jufo-ufo/Breadboard-Computer/paper/JuFo_Langfassung/Langfassung.pdf_correction.pdf

# Platinencomputer - Langfassung

### Alexander Wersching und Simon Walter

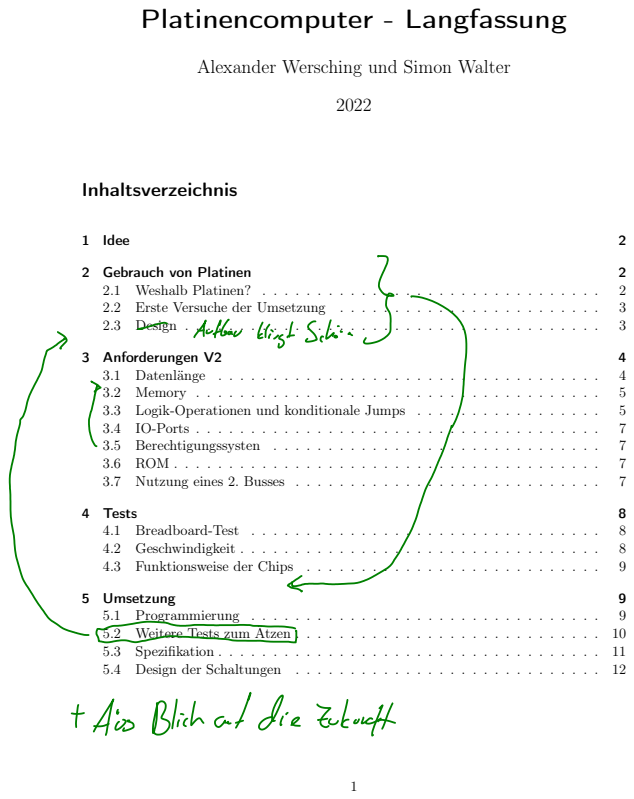
[picture p17: page 1]
Inhaltsverzeichnis; 1 Idee; 2 Gebrauch von Platinen; 3 Anforderungen V2; 4 Tests; 5 Umsetzung

### 1 Idee

Vor ca. 2 Jahren hatte Alex die Idee, er wolle einen 8-bit Computer bauen, die vor 2 Jahren beim Regionalwettbewerb München-West eingereichte Version einer anderen Gruppe
hat | dann | auch | das | Interresse | von | mir | (Simon) | geweckt.
Ein paar Monate später haben wir uns
dann dazu entschieden, tatsächlich einen
eigenen 8-bit-Computer zu bauen und haben auch bald angefangen erste Versuche auf dem Breadboard zu entwickeln. Es gab noch weder eine Möglichkeit diese erste Version automatisch zu betreiben, noch Daten zu schreiben/speichern, oder irgendwie mit der Umgebung zu interagieren, nur 3 Register, 2 Operationen und viele Knöpfe zum Bedienen.

### 2 Gebrauch von Platinen

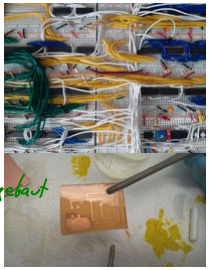
[picture p18: figure]

2.1 Weshalb Platinen?


Bald war aber klar, dass ein einfaches Verwenden von flachen Kabeln als Verbindung zwischen den Breadboards, das Kabelgewirr, das wir bei dem Projekt von vor 2 Jahren gesehen haben und nach Möglichkeit vermeiden wollten, um ein übersichtlicheres Design zu erreichen, nicht lösen kann.

Auf der Suche nach einer Alternative sind wir fast zwangsläufig auf Platinen gekommen, aber weil unser Computer ja nicht mehr wirklich selbst gemacht wäre, wenn wir diese nur professionell Ätzen lassen würden, wollten wir versuchen - zumindest einen Teil - selbst zu ätzen, auch wenn wir dadurch natürlich auf viele neue Probleme gestoßen sind...

2

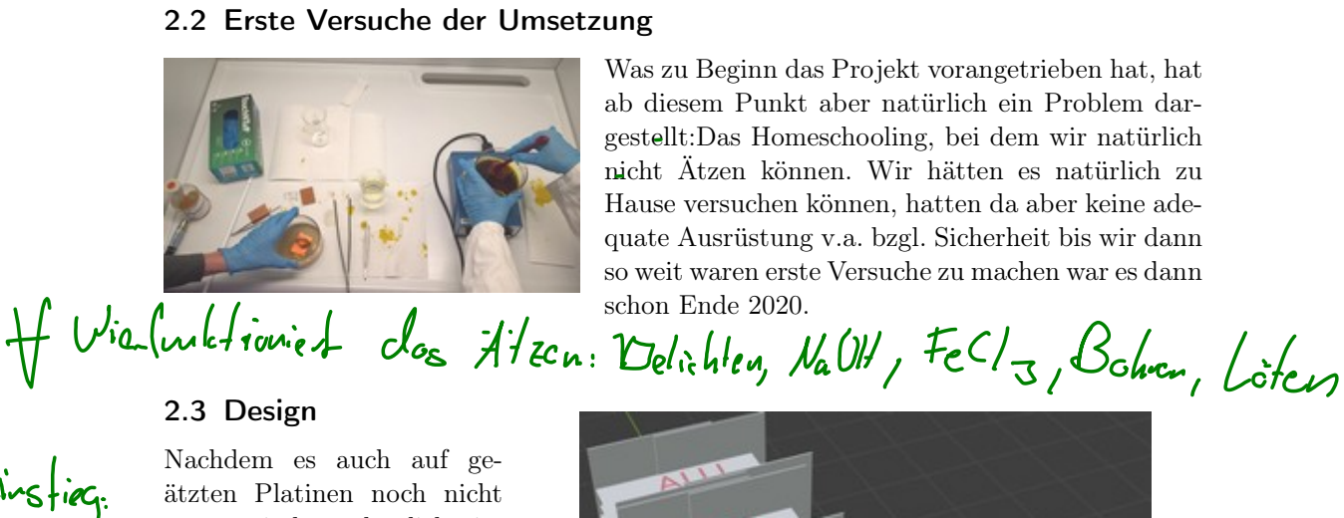
[picture p19: figure]
2.2 Erste Versuche der Umsetzung; schon Ende 2020.; 2.3 Design Nachdem es auch auf ge- ätzten Platinen noch nicht

Was zu Beginn das Projekt vorangetrieben hat, hat ab diesem Punkt aber natürlich ein Problem dargestellt:Das Homeschooling, bei dem wir natürlich nicht Ätzen können. Wir hätten es natürlich zu Hause versuchen können, hatten da aber keine adequate Ausrüstung v.a. bzgl. Sicherheit bis wir dann so weit waren erste Versuche zu machen war es dann


automatisch ordentlich ist und eine derart große Platine für uns nicht machbar gewesen wäre, haben
wir uns dann noch ein 3-
Dimensionales Design ausgedacht.

Offensichtlich ist das mit unseren aktuell geplanten Modulen: am Boden sitzt eine große Bus-Platine, auf der wir alle Module senkrecht
aufstecken.

3

### 3 Anforderungen V2

Im nächsten Lockdown hatten wir dann wieder viel Zeit zu planen, und der geplante Computer wurde immer komplexer.

3.1 Datenlänge
Aus den ursprünglich geplanten 8-bit wurden 16-bit Datenlänge:
Die Address- und Datenlänge besagt, wie viele binäre Ziffern (bits) für eine Adresse und Daten verwendet werden.
Je mehr Ziffern man verwendet desto größere Zahlen können in einer Operation verarbeitet werden wobei die maximal repräsentierbare Zahle 2n − 1 ist wenn n die Anzahl der Binären Ziffern (= Bits) ist.

n teilbar durch 8 zu machen, ist dabei relativ angenehm, weil 8 bit = 1 byte,
und Bytes sind nun mal die Grundlage für das meiste in der Informatik,
zudem kommen einige elementar ICs, z.B. Buffer oder Register, immer mit 8 bits.

Jedoch gilt, je mehr Bits man verwendet, desto mehr Schaltung braucht man und desto größer der Stromverbrauch, wodurch es für uns relativ schnell unrealistisch aufwendig wird

Wir haben uns daher für 16 bit entschieden, womit wir Zahlen bis zwischen 0 und 65535 darstellen können.
Diese Menge ist gerade große genug, um eine Zahl abzubilden, die für die meisten Programme groß genug ist, aber trotzdem auf Platinen noch einigermaßen handhabbar.

4

3.2 Memory
Um auch Daten oder Programme verwenden zu können haben wir dann als erstes noch einen größeren Speicher hinzu gefügt: Memory
Memory ist in 65536 (weil wir genau so viele Adressen in unseren 16bit speichen können) einzelne und unabhängige Speicherzellen (jede 16 Bit groß) aufgeteilt.
Der Computer kann damit auf 65536 words oder 131072 bytes (= 128 kib) direkt zugreifen.
(Die Größe messen wir in words (w) oder in kilowords (kiw), wobei 1 word = 2 bytes = 16 Bit sind.)

Memory wird dabei über LD- und STR-Instruktionen gesteuert.
Die LD-Instruktion kopiert einen Wert aus Memory und schreibt ihn in ein Ziel-Register, während STR an der angegebenen Adresse den Wert mit dem Wert des Quellen-Register überschreibt.

Um aber noch mehr Speicher zu bekommen und das später erwähnte Berechtigungssystem möglichst einfach umsetzen zu können haben wir noch Banken hinzugefügt:
Banken sind externe Memory Module, die eingesteckt werden können. Alle Banken sind gleich groß (16 kiw = 32 kib) und der Computer unterstützt maximal 65536 unterschiedliche Banken. Jede Bank hat dabei eine ID (BID), die von 0 bis 65535 reicht.
Der Computer hat zwei Bank-Slots (Slot 1 0x8000 - 0xbfff und Slot 2 0xc000 -0xffff).

Es kann auf jede dieser Slots eine der theoretisch 65536 Banken gelegt werden.
Bank 1 ist dafür gedacht, dass jeder Prozess dort in seiner eigenen Bank lebt, sodass in dem Prozess absolute Memory Adressen verwendet werden können, weil das Programm immer an der gleichen Stelle liegt. Außerdem wird in der Bank auch der Stack des jeweiligen Prozesses gespeichert, sodass dieser von anderen Prozessen nicht überschrieben werden kann.
Bank 2 dient als potentieller zusätzlichen Speicher des Prozesses, oder als allgemeineren Speicherort, um zwischen den Prozessen Daten zu übermitteln.

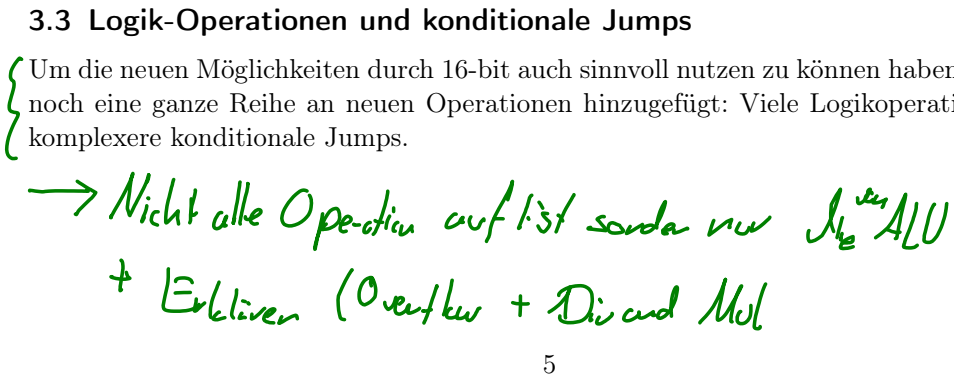
[picture p20: figure]
3.3 Logik-Operationen und konditionale Jumps; komplexere konditionale Jumps.

Um die neuen Möglichkeiten durch 16-bit auch sinnvoll nutzen zu können haben wir dann noch eine ganze Reihe an neuen Operationen hinzugefügt: Viele Logikoperationen und

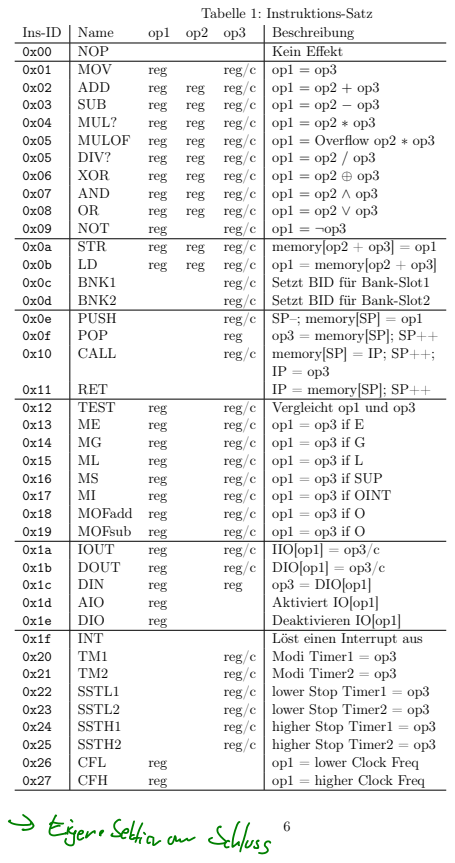
[picture p21: page 6]
Ins-ID; Name; Beschreibung; NOP; Kein Effekt; MOV; reg; reg/c; ADD; reg reg reg/c; SUB; MUL?; MULOF reg reg reg/c; op1 = Overflow op2 ∗ op3; DIV?; XOR; AND; NOT; STR; memory[op2 + op3] = op1; op1 = memory[op2 + op3]; BNK1; Setzt BID für Bank-Slot1; BNK2; Setzt BID für Bank-Slot2; PUSH; SP–; memory[SP] = op1; POP; op3 = memory[SP]; SP++; CALL; memory[SP] = IP; SP++;; RET; IP = memory[SP]; SP++; TEST; Vergleicht op1 und op3; op1 = op3 if SUP; op1 = op3 if OINT; MOFadd reg; MOFsub reg; IOUT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

Tabelle 1: Instruktions-Satz

3.4 IO-Ports
Dazu hat sich die Idee von komplexer IO-Interaktion mit dem Computer ergeben: universelle Ports zum Anschließen von Festplatten, Sensoren, einfachen Tastaturen, LCD-Displays und einer Grafikkarte.
Die theoretisch 65536 Anschlüsse, wobei jedem eine Anschluss-ID zugewiesen ist, kommunizieren mit IO-Geräten über 4 Kommandos, die als 4 separate Pins zwischen dem Controller und dem Gerät umgesetzt sind:
1. Einen Befehl an das IO-Gerät schicken (auf Programm-Ebene);
2. Daten zu einem vorherigen Befahl an das Gerät schreiben;
3. Die Anfrage der IO-Gerätes Daten an den Computer zurück zu schreiben, was bei diesem normalerweise einen Interrupt auslöst;
4. Bestätigen des Computers, das das Externe Gerät schreiben darf.

3.5 Berechtigungssysten
Die vermutlich die größte Änderung war danach, dass wir ein Berechtigungssystem einführen wollten. Dafür haben wir dann Flaggen, Interrupts und noch mehr Instruktionen hinzugefügt.

3.6 ROM
Um den Computer komplett unabhängig funktionsfähig machen zu können, haben wir uns dann überlegt einen Teil des RAMs durch ROM zu ersetzen, um automatisch Programme von einem externen Speichermedium laden zu können.

3.7 Nutzung eines 2. Busses
Um Memory innerhalb einer Instruktion zu beschreiben, muss dieses sowohl eine 16-bit Adresse über die Position in Memory erhalten, als auch den 16-bit Wert, der dort gespeichert werden soll, damit diese beiden Daten parallel übermittelt werden können brauchen wir also 2*16bit. Wir hätten dafür natürlich auch irgendwelche Kabel verlegen können, aber wir wollen in unserem System die Daten immer auf dem Bus haben, damit diese auch von anderen Modulen gelesen werden könnten, und die Adresse muss im Anwendungsfall als Stack vor Benutzung um eins erhöht oder verringert werden, was in unserem System durch die ALU erfolgen sollte, wobei diese nur auf den Bus ihre Daten auseben kann.

7

### 4 Tests

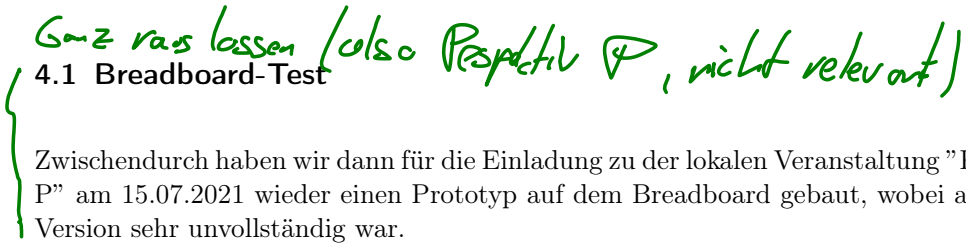
[picture p22: figure]
4.1 Breadboard-Test; Version sehr unvollständig war.

Zwischendurch haben wir dann für die Einladung zu der lokalen Veranstaltung ”Persvektive P” am 15.07.2021 wieder einen Prototyp auf dem Breadboard gebaut, wobei auch diese

4.2 Geschwindigkeit
Um einen Eindruck zu bekommen, wie komplex unsere Programme werden können, ohne übermäßig lange zu brauchen, haben wir dann versucht zu errechnen, wie schnell wir den Computer maximal laufen lassen können, ohne fehlerhafte Ergebnisse zu erhalten. Also haben den "Propagation-delay", die Zeit, bis der Chip den Output liefert, den der laut der Eingabe haben müsste, aller Komponenten gemessen, die wir verwenden wollen. Die meisten
Chips, die wir jetzt vorhaben zu verwenden, haben
eine Verzögerung von ungefähr 8 Nanosekunden, al-

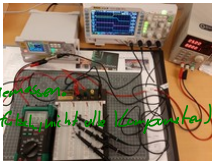
[picture p23: figure]

lerdings haben wir bei den verschiedenen Versionen, die wir getestet haben, teilweise weitaus höhere Werte bis zu 150ns erreicht, was an sich noch nicht so schlecht ist, aber wenn wir damit rechnen, dass wir Reihen von bis zu 40 Chips in einem Clock-Zyklus haben, limitiert das die Geschwindigkeit schon sehr.

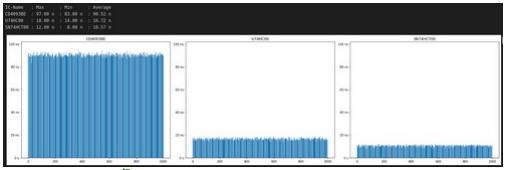
[picture p24: figure]

4.3 Funktionsweise der Chips
Wir wollen als Basis für unseren Computer ja Chips kaufen, aber wie funktionieren die eigentlich? Wir haben also versucht den Aufbau herauszufinden, indem wir einfach einen geöffnet haben, wobei ”Einfach” nicht so ganz stimmt, weil die Hülle aus Epoxidharz

8

besteht, was sich fast nicht auflösen lässt. Also mussten wir mechanisch abtragen, also Schleifen. Leider haben wir es damit nie geschafft das gesamte Silizium/die Verbindungsbahnen frei zu legen, sodass wir keinen Schaltplan erstellen könnten, es gab uns aber

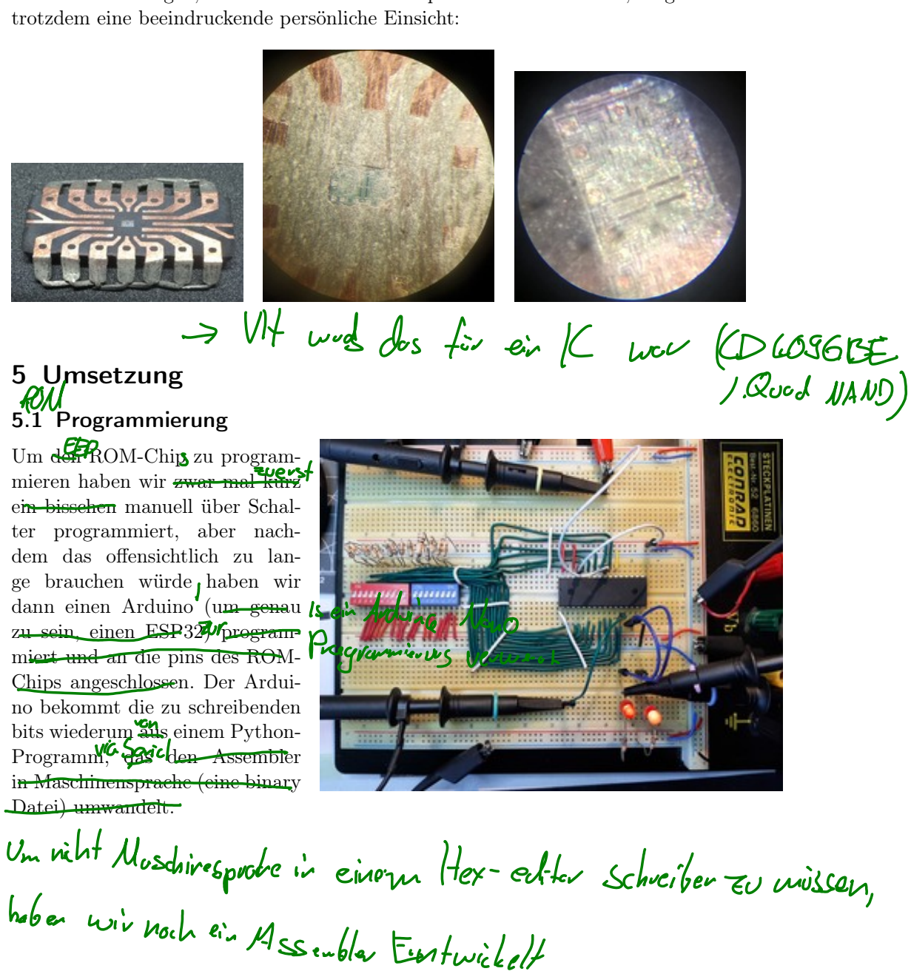
[picture p25: figure]
trotzdem eine beeindruckende persönliche Einsicht:; 5 Umsetzung; 5.1 Programmierung Um den ROM-Chip zu program- mieren haben wir zwar mal kurz ein bisschen manuell über Schal- ter programmiert, aber nach- dem das offensichtlich zu lan- ge brauchen würde haben wir dann einen Arduino (um genau zu sein, einen ESP32) program- miert und an die pins des ROM- Chips angeschlossen. Der Ardui- no bekommt die zu schreibenden bits wiederum aus einem Python- Programm, das den Assembler in Maschinensprache (eine binary Datei) umwandelt.

9

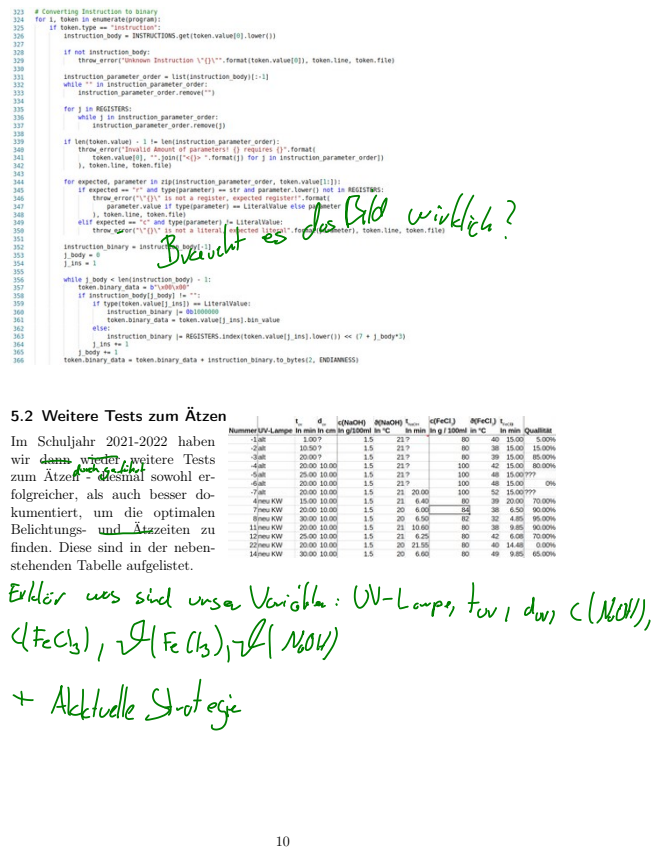
[picture p26: page 10]

5.2 Weitere Tests zum Ätzen
Im Schuljahr 2021-2022 haben
wir dann wieder weitere Tests
zum Ätzen - diesmal sowohl er-
folgreicher, als auch besser do-
kumentiert, um die optimalen
Belichtungs- und Ätzzeiten zu
finden. Diese sind in der neben-
stehenden Tabelle aufgelistet.

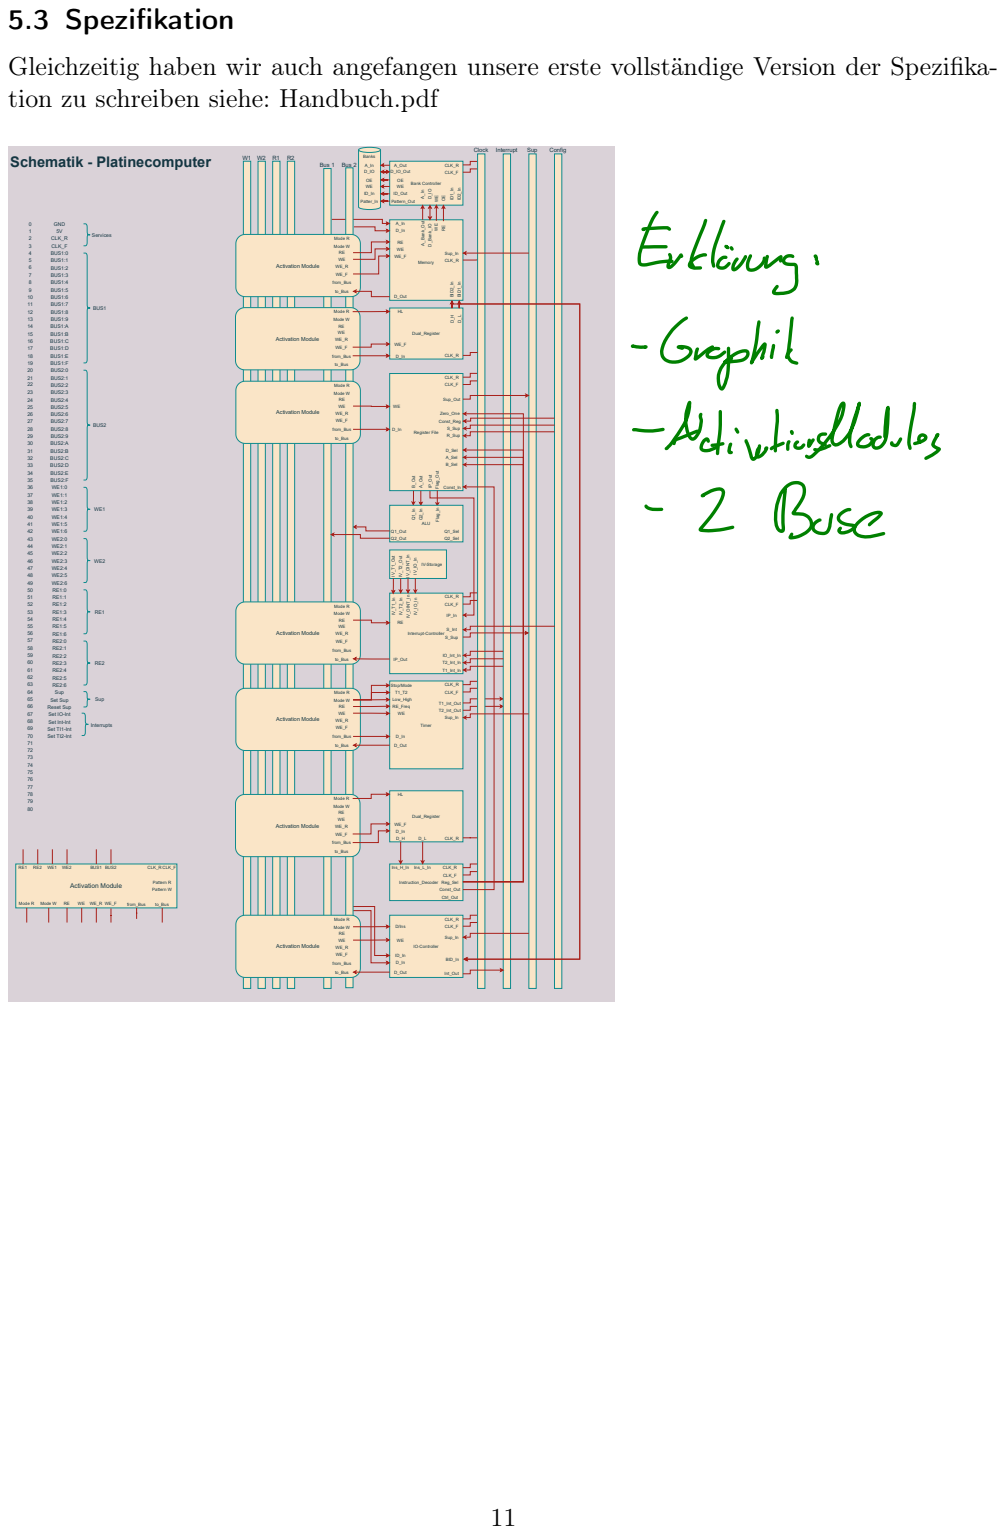
[picture p27: page 11]
Memory; D_Out; CLK_R WE A_Bank_Out; Bank Controller D_Bank_IO A_In D_IO WE; CLK_R; IO-Controller; D/Ins; CLK_F; Sup_In; Sup_In BID¹_In; Interrupt-Controller; IV-Storage; IV_T1_In IV_T1_Out RE; IP_Out; S_Sup; IO_Int_In; Int_Out; T1_Int_In; T2_Int_In; S_Int; CLK_FBID²_In; Instruction_Decoder; Ins_H_In; Ctrl_Out; Register File A_Out; Flag_Out; D_Sel; A_Sel; B_Sel; Sup_Out; R_Sup; Zero_One; B_Out; ALU; Q1_Out; Q2_Out; Q2_Sel Flag_In; Q1_Sel; Q2_In Timer; T1_Int_Out; T2_Int_Out; Low_High; Stop/Mode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

5.3 Spezifikation
Gleichzeitig haben wir auch angefangen unsere erste vollständige Version der Spezifika-
tion zu schreiben siehe: Handbuch.pdf

Set IO-Int
Set Int-Int
Set TI1-Int
Set TI2-Int

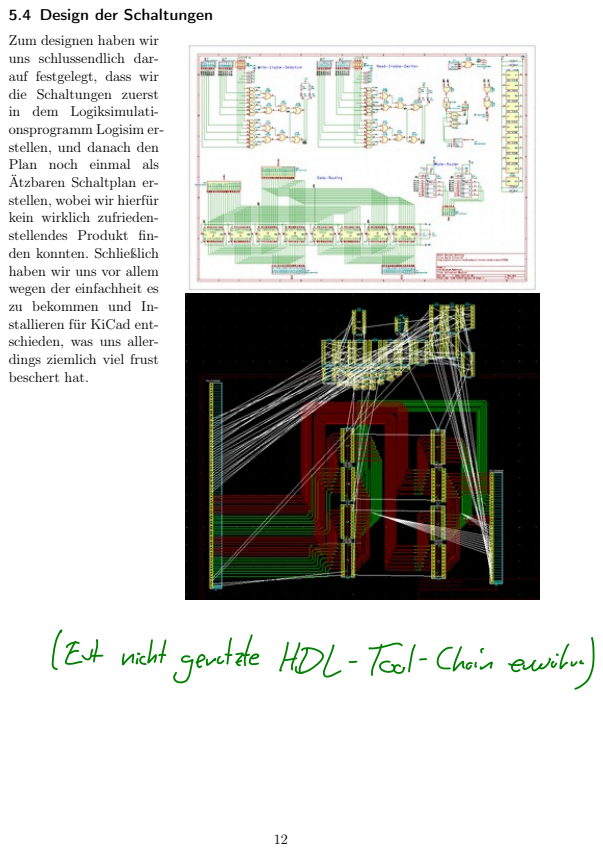
[picture p28: page 12]

5.4 Design der Schaltungen
Zum designen haben wir
uns schlussendlich dar-
auf festgelegt, dass wir
die Schaltungen zuerst
in dem Logiksimulati-
onsprogramm Logisim er-
stellen, und danach den
Plan noch einmal als
Ätzbaren Schaltplan er-
stellen, wobei wir hierfür
kein wirklich zufrieden-
stellendes Produkt fin-
den konnten. Schließlich
haben wir uns vor allem
wegen der einfachheit es
zu bekommen und In-
stallieren für KiCad ent-
schieden, was uns aller-
dings ziemlich viel frust
beschert hat.
