jufo-ufo/Breadboard-Computer/images/1Bilder_Dokumentation.odt

8Bit-Prozessor

23.7.2020:

- 1.er aufbau der Clock mit hilfe des NE555: noch mit starker Übersteuerung (Grund noch unbekannt)
- 1.er test einer Clock durch Spulen: Berechnungen haben gestimmt, noch keine “Dauerwelle”
- Erforschen der funktionen weiterer komponenten
- Vertrautmachen mit dem Oszi und der Stromquelle
