jufo-ufo/Breadboard-Computer/circets/Dual_Register/manufactor_sheet_top.pdf

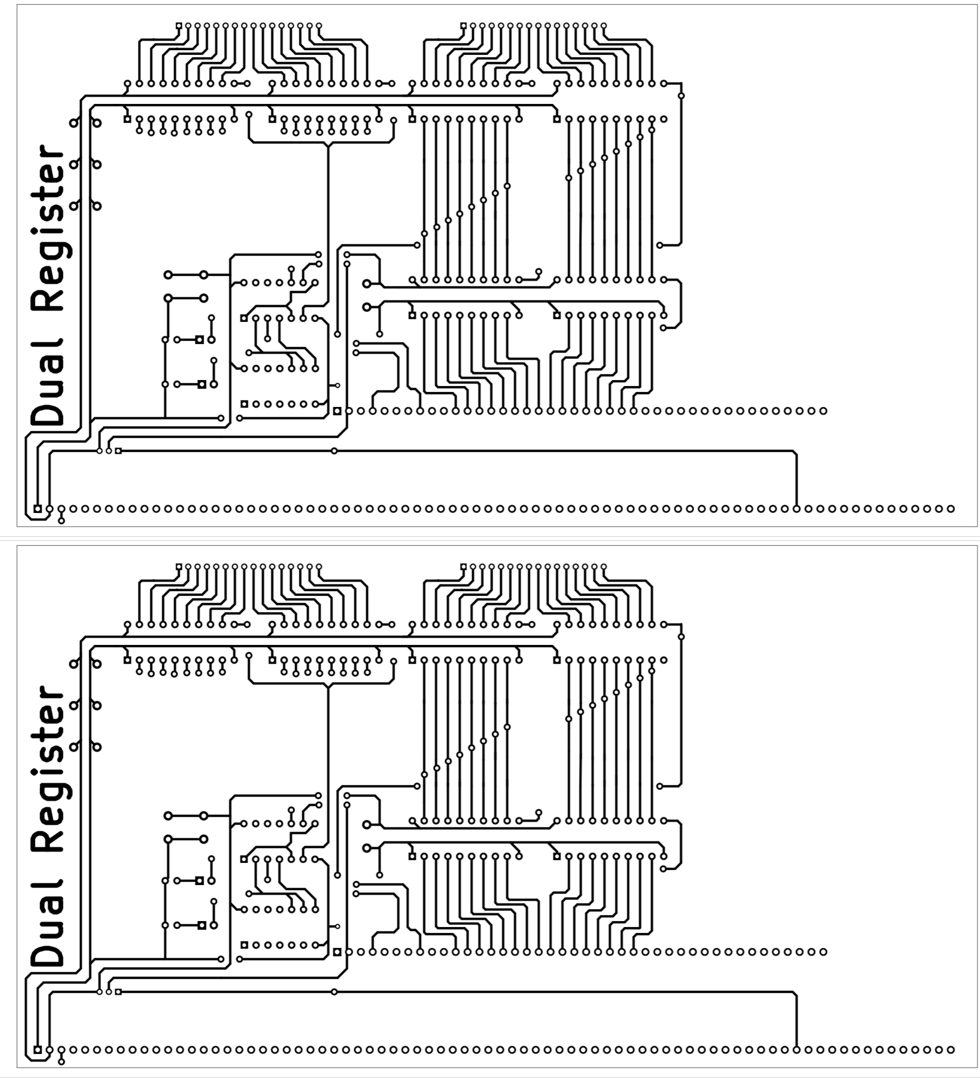
[picture p29: page 1]
