jufo-ufo/Breadboard-Computer/circets/Activation_Module/logic_schematic.png

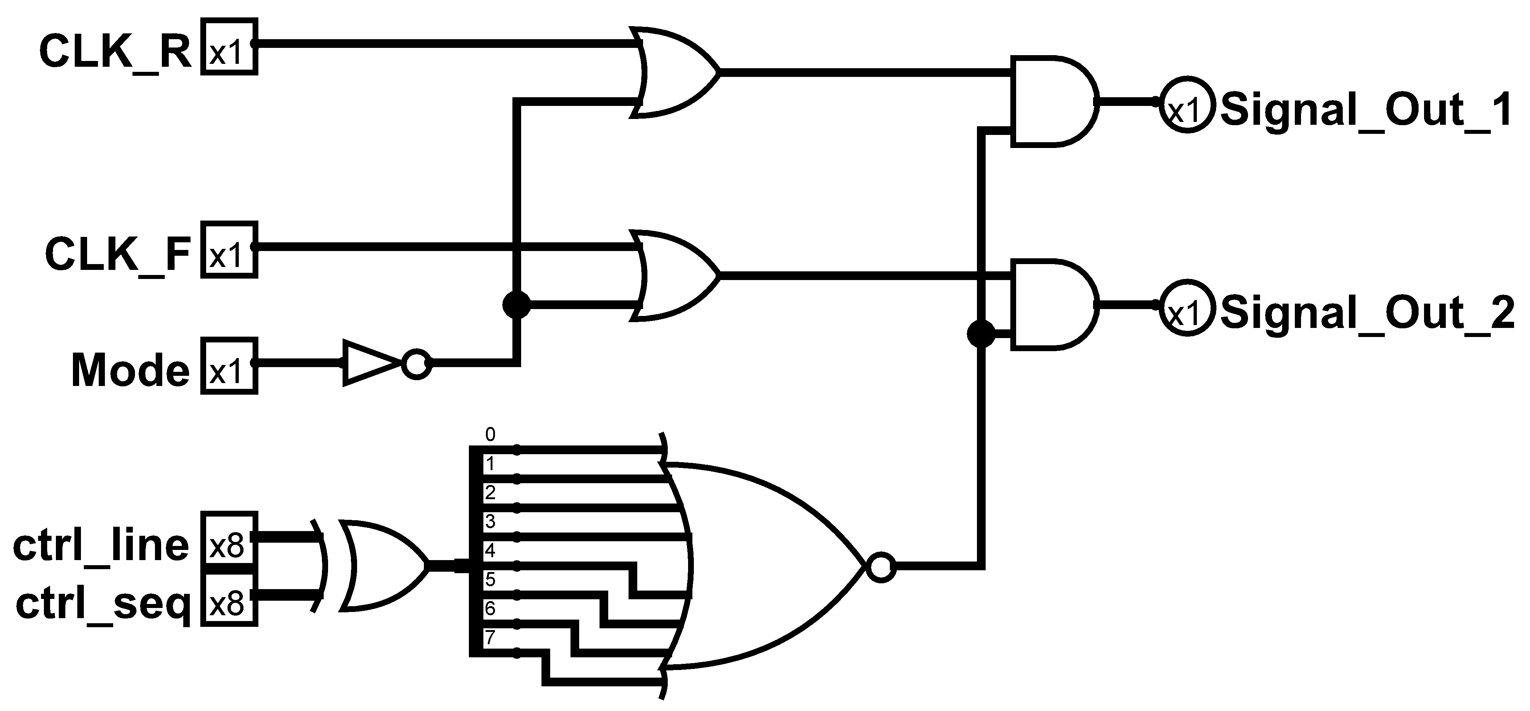
circets/Activation_Module/logic_schematic.png
