jufo-ufo/Breadboard-Computer/images/3D_Desighn_V2.png

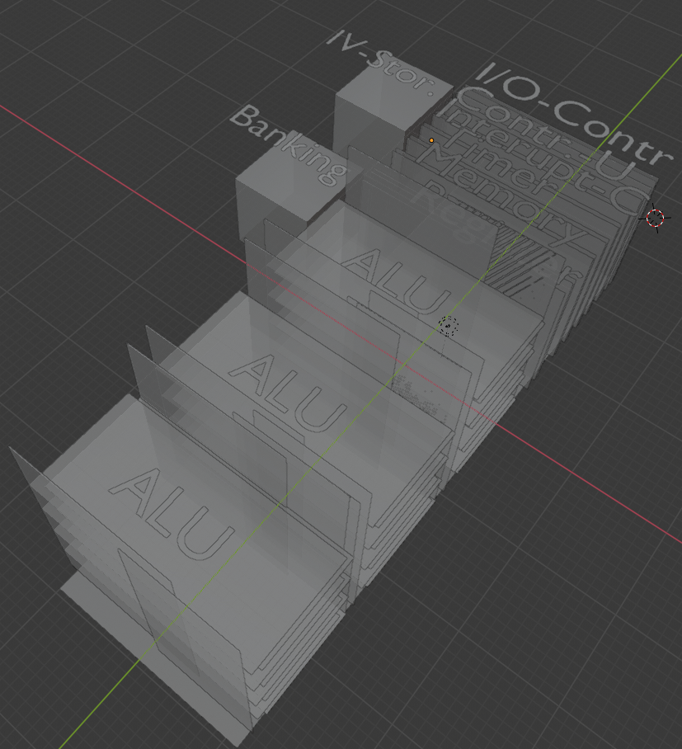
images/3D_Desighn_V2.png
