jufo-ufo/Breadboard-Computer/images/20211208_200820.jpg

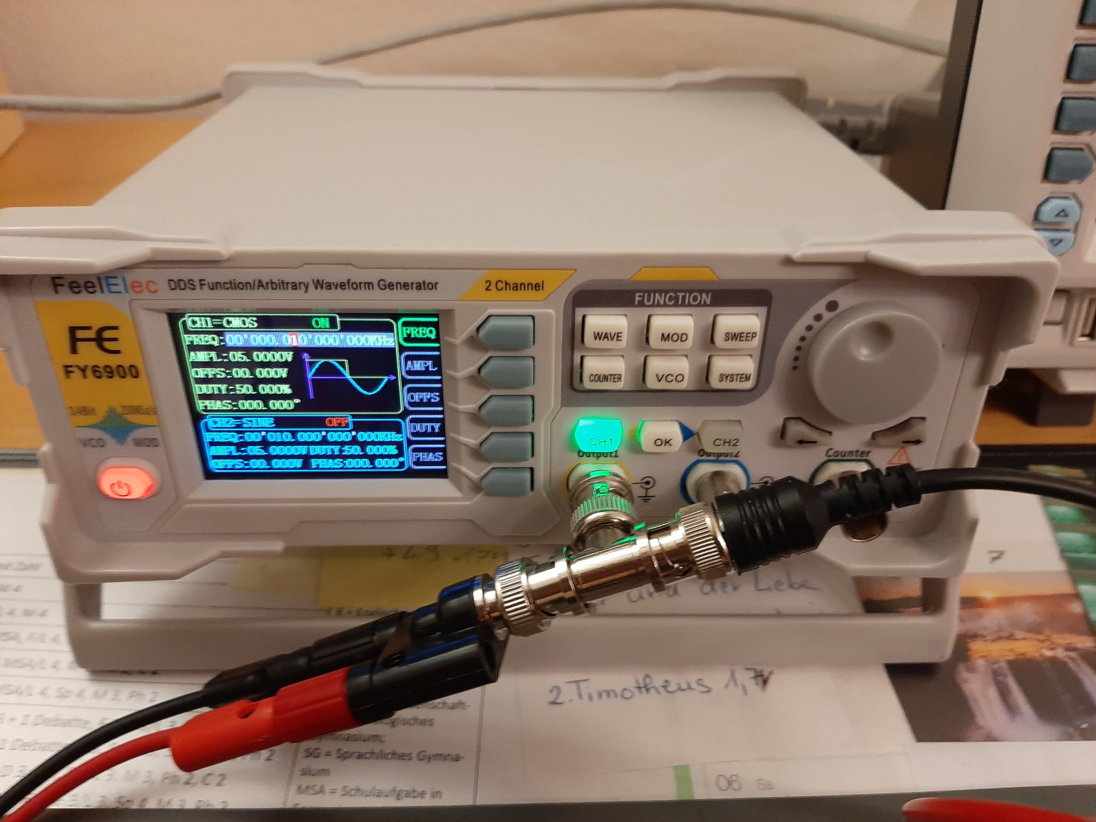
images/20211208_200820.jpg
