jufo-ufo/Breadboard-Computer/images/20211208_200826.jpg

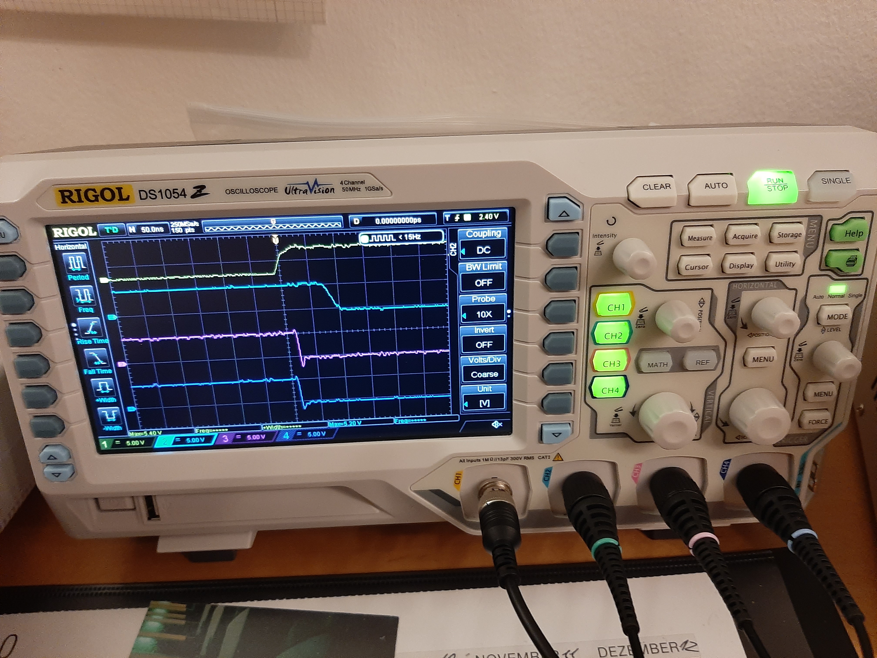
images/20211208_200826.jpg
