jufo-ufo/Breadboard-Computer/images/20211219_222546.jpg

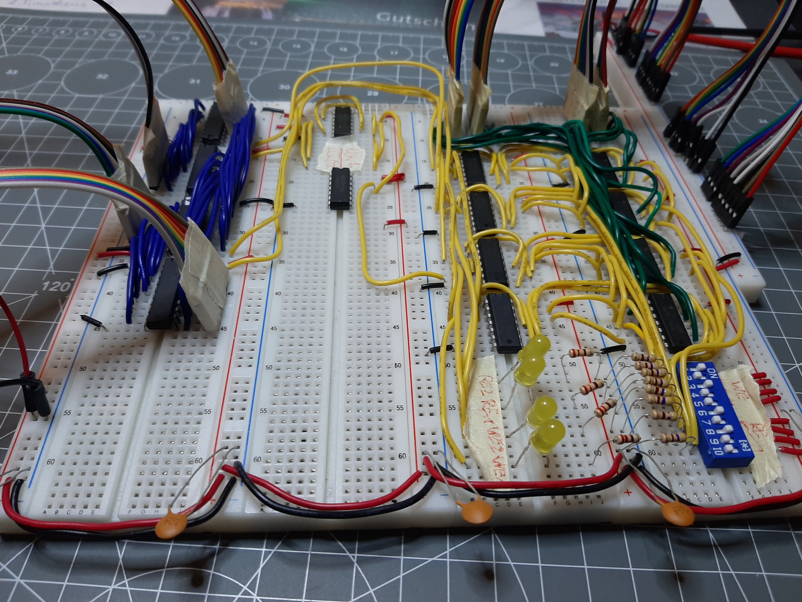
images/20211219_222546.jpg
