jufo-ufo/Breadboard-Computer/images/20211219_222552.jpg

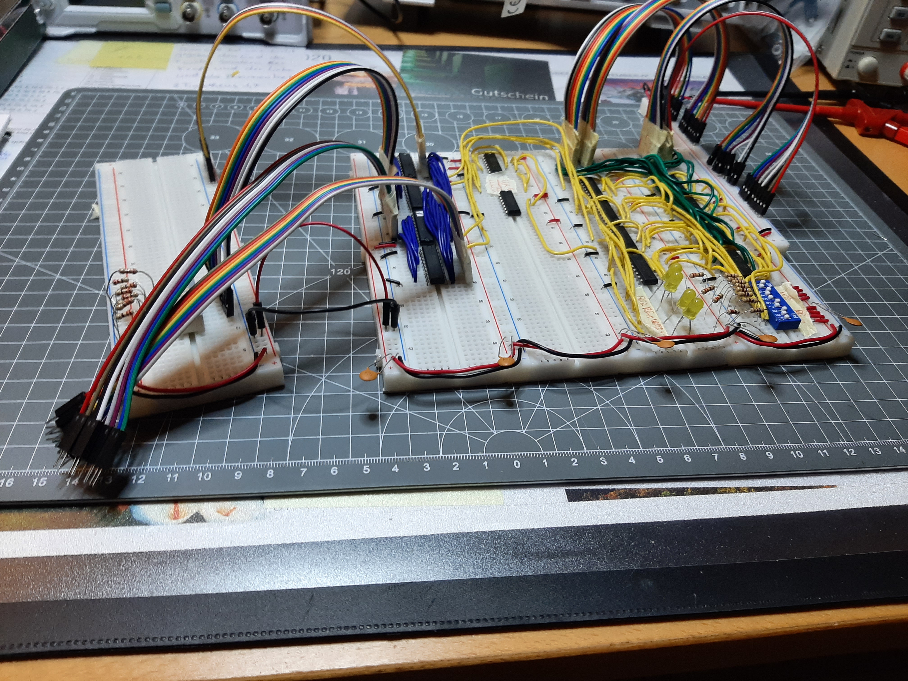
images/20211219_222552.jpg
