jufo-ufo/Breadboard-Computer/images/20220110_205530.jpg

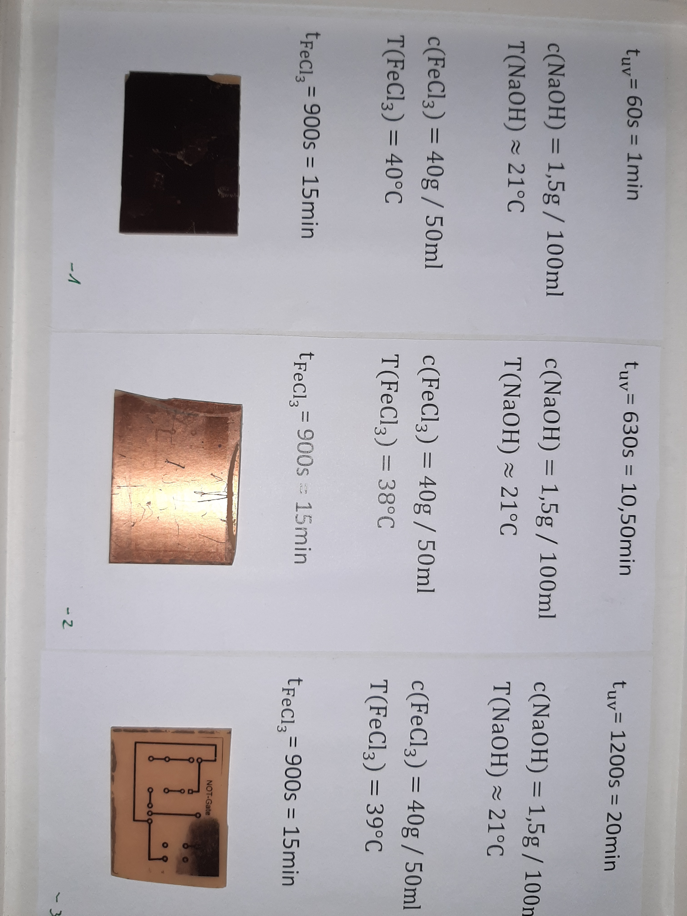
images/20220110_205530.jpg
