jufo-ufo/Breadboard-Computer/images/20220110_205549.jpg

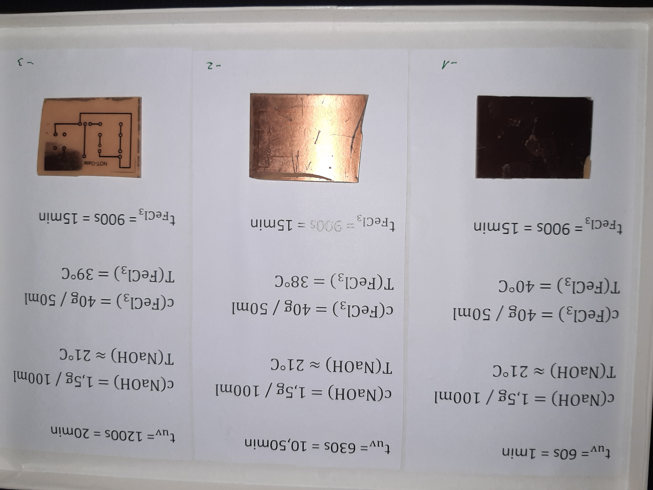
images/20220110_205549.jpg
