jufo-ufo/Breadboard-Computer/images/20220110_205553.jpg

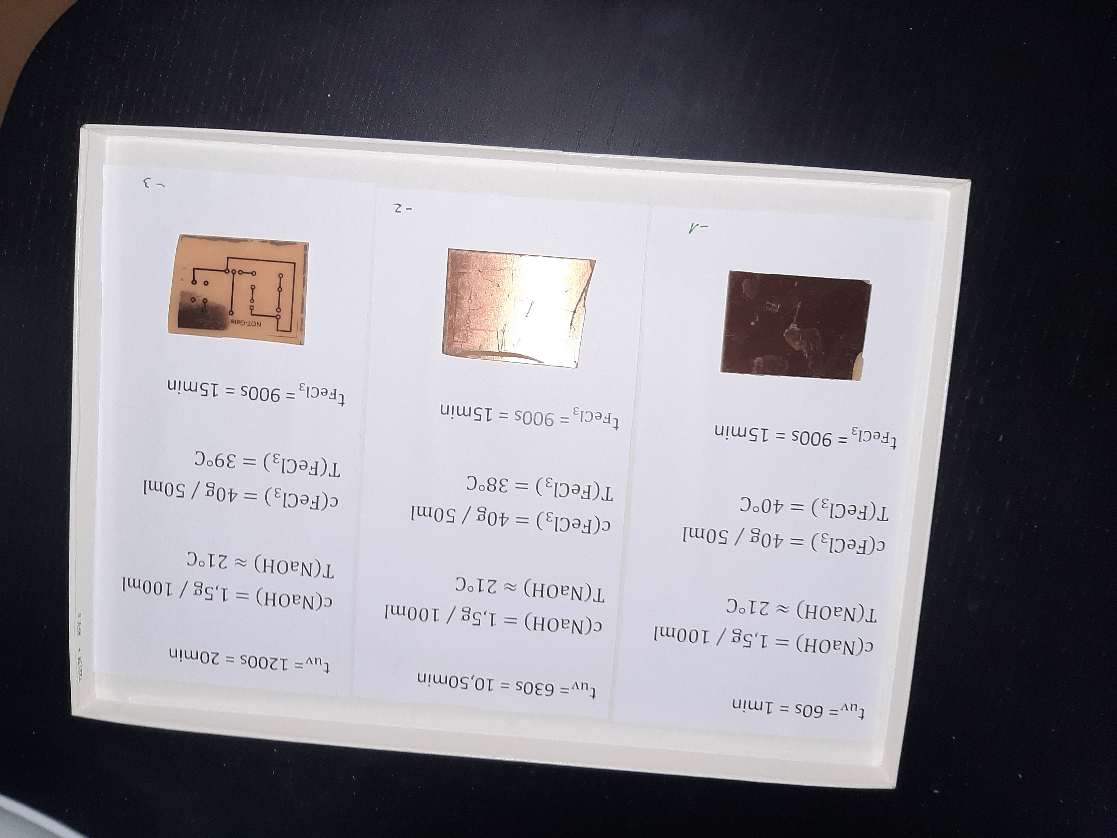
images/20220110_205553.jpg
