jufo-ufo/Breadboard-Computer/images/20220110_205558.jpg

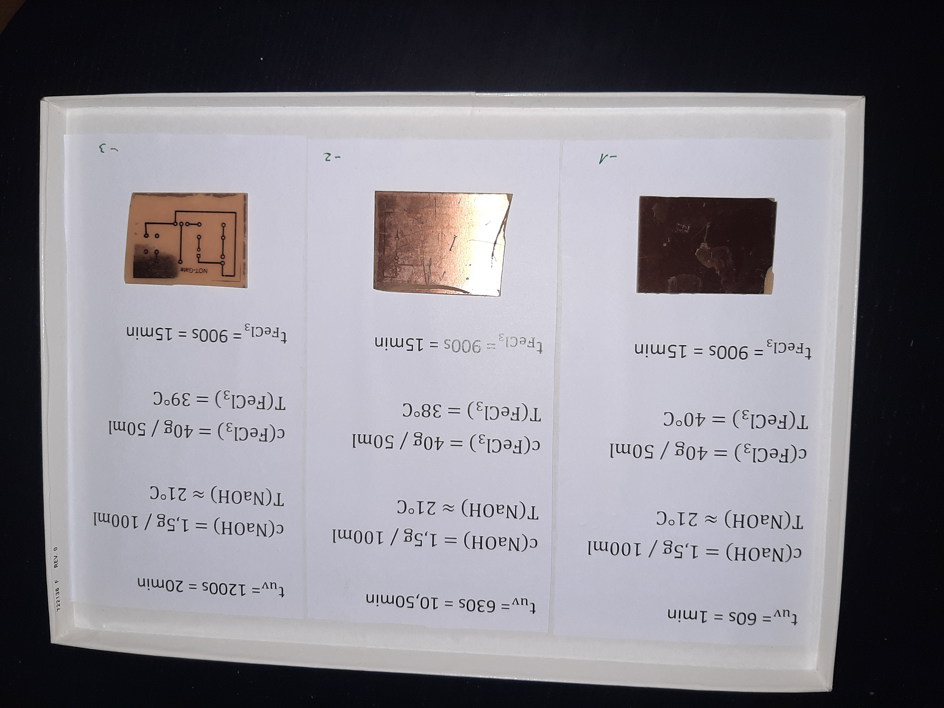
images/20220110_205558.jpg
