jufo-ufo/Breadboard-Computer/images/20220110_205615.jpg

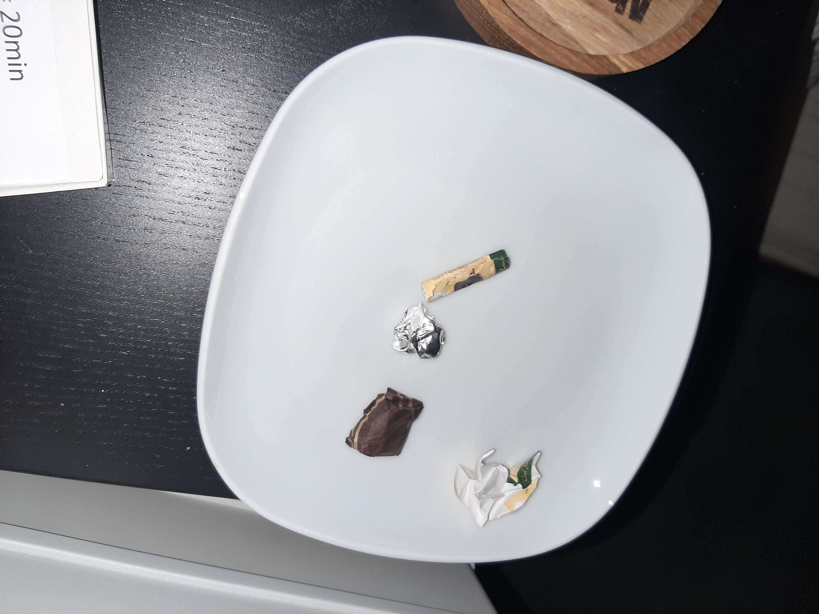
images/20220110_205615.jpg
