jufo-ufo/Breadboard-Computer/images/Activation_Module_V01_BB_01.jpg

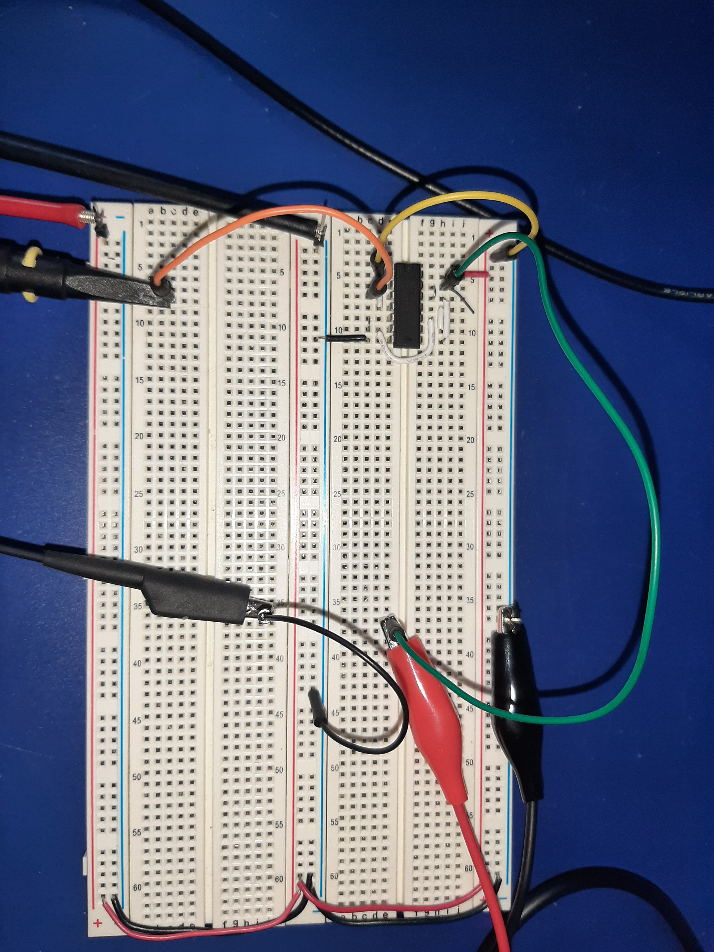
images/Activation_Module_V01_BB_01.jpg
