jufo-ufo/Breadboard-Computer/images/Activation_Module_V01_BB_02.jpg

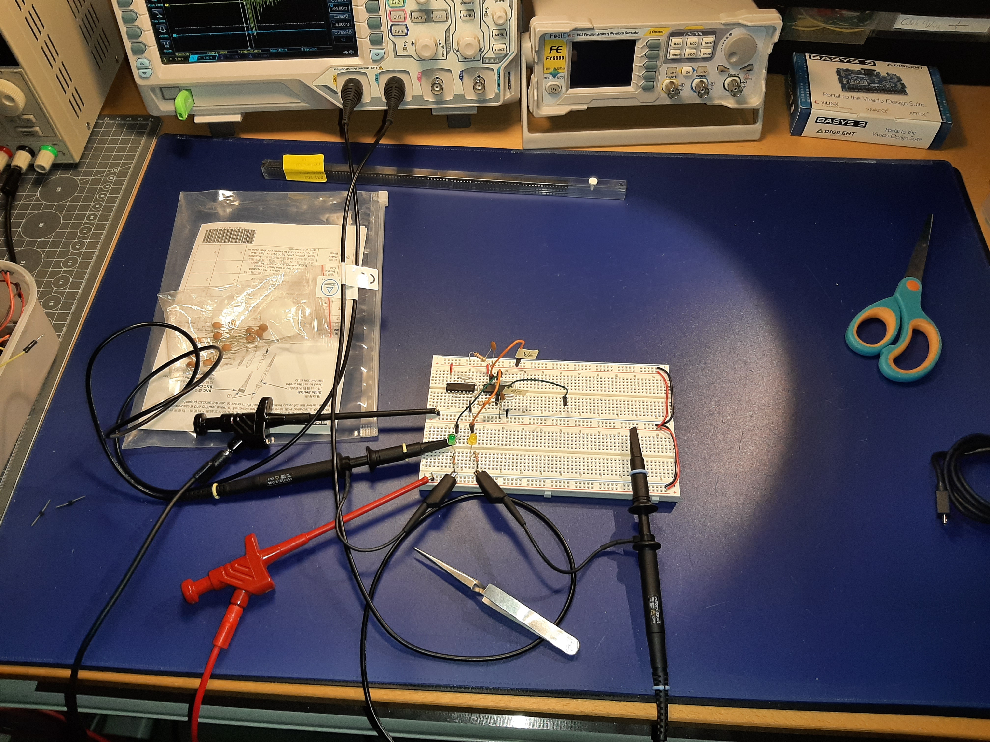
images/Activation_Module_V01_BB_02.jpg
