jufo-ufo/Breadboard-Computer/images/Activation_Module_V01_BB_03.jpg

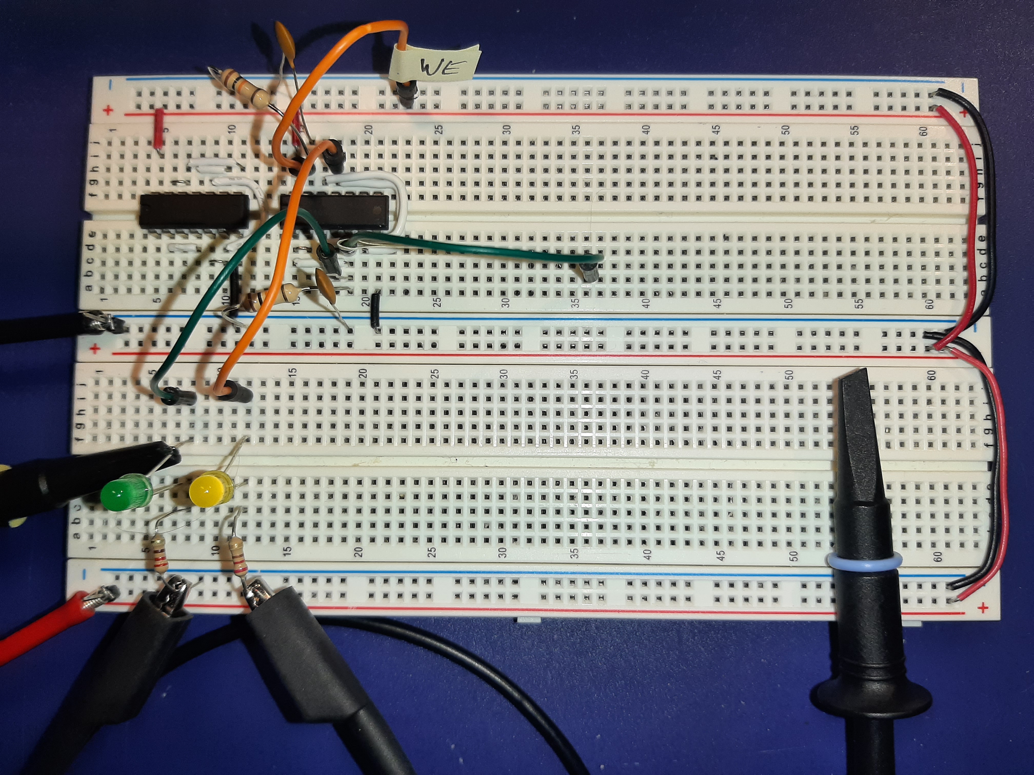
images/Activation_Module_V01_BB_03.jpg
