jufo-ufo/Breadboard-Computer/images/aetzen_tabelle.png

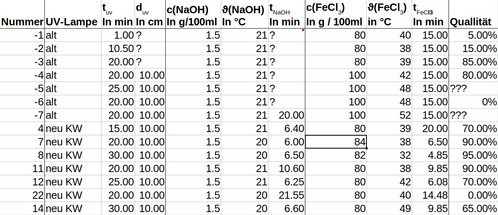
images/aetzen_tabelle.png
