jufo-ufo/Breadboard-Computer/images/Alt Lücken_01.jpg

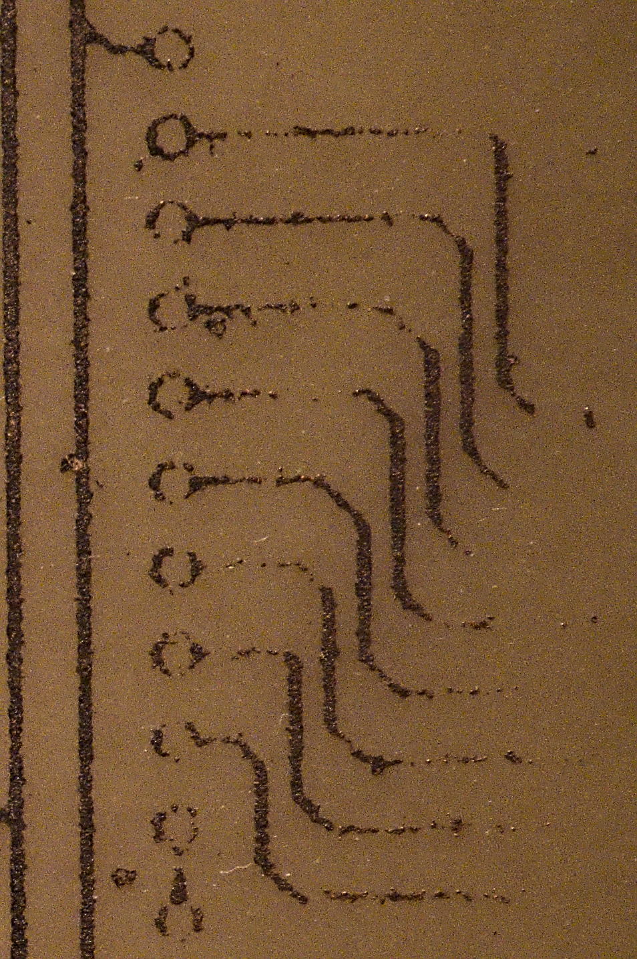
images/Alt Lücken_01.jpg
