jufo-ufo/Breadboard-Computer/images/ALU-1.PNG

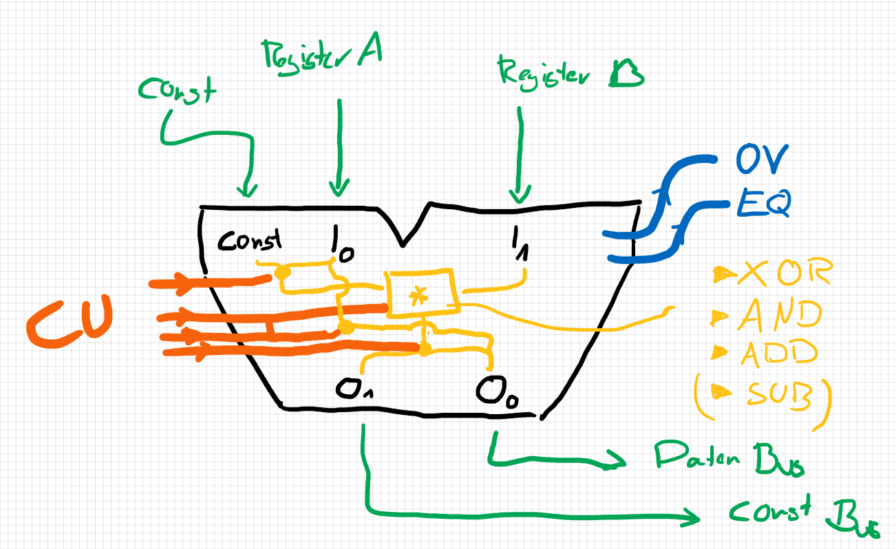
images/ALU-1.PNG
