jufo-ufo/Breadboard-Computer/images/AS6C1008-55PCN_A_LH_Load.png

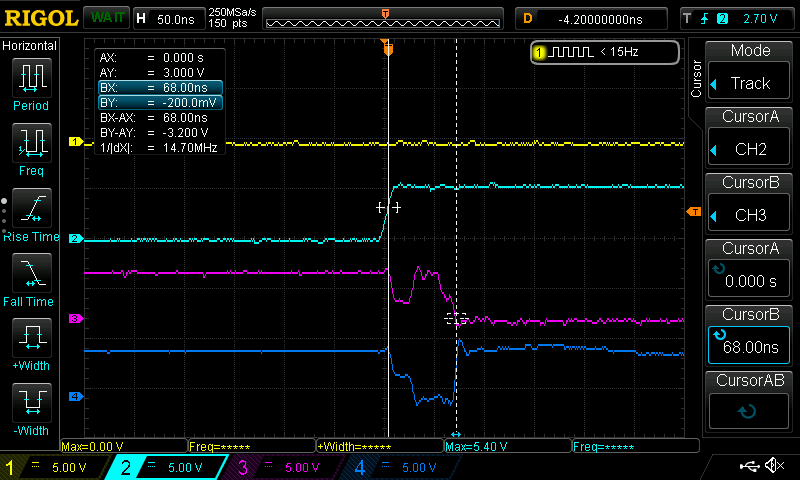
images/AS6C1008-55PCN_A_LH_Load.png
