jufo-ufo/Breadboard-Computer/images/AS6C1008-55PCN_OE_HL_Output.png

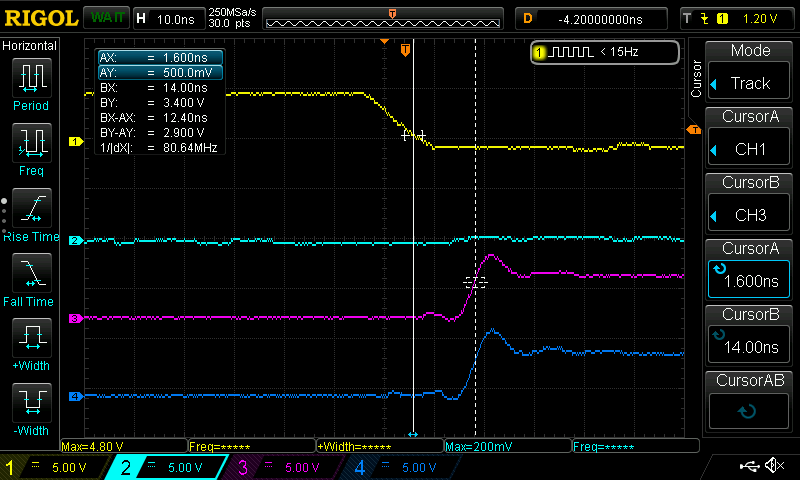
images/AS6C1008-55PCN_OE_HL_Output.png
