jufo-ufo/Breadboard-Computer/images/BreadBoards_02.jpg

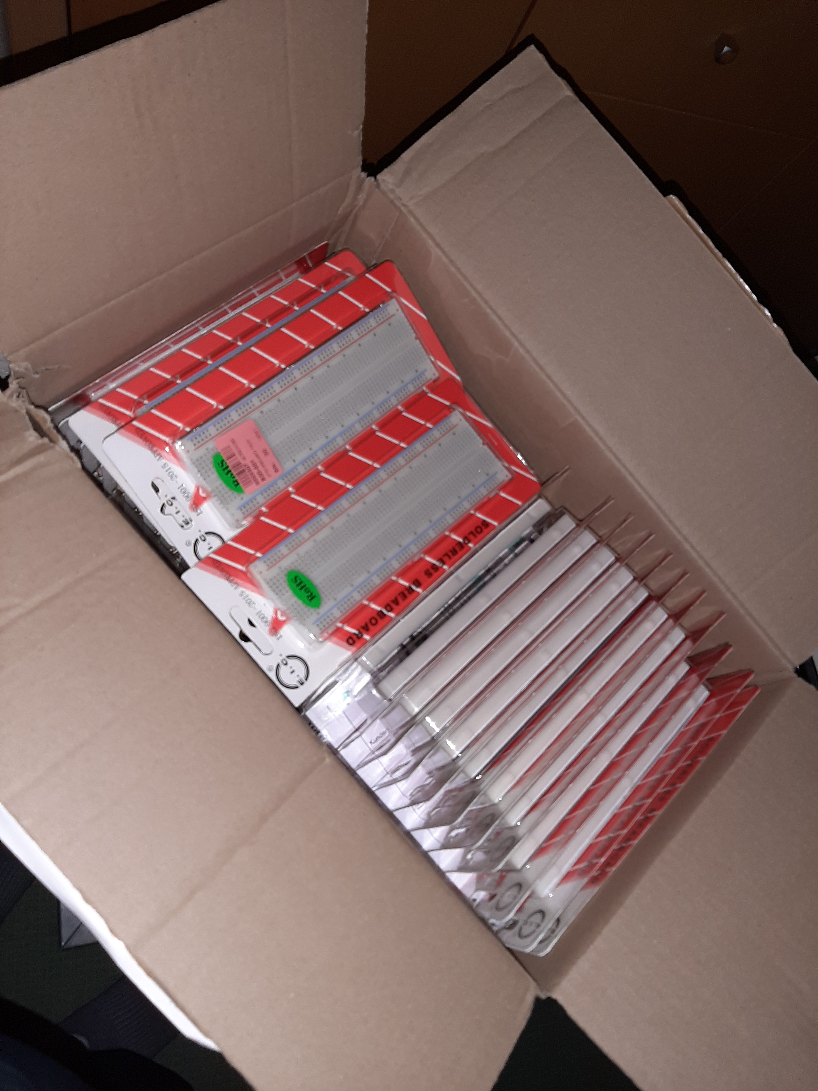
images/BreadBoards_02.jpg
