jufo-ufo/Breadboard-Computer/images/BreadBoards_03.jpg

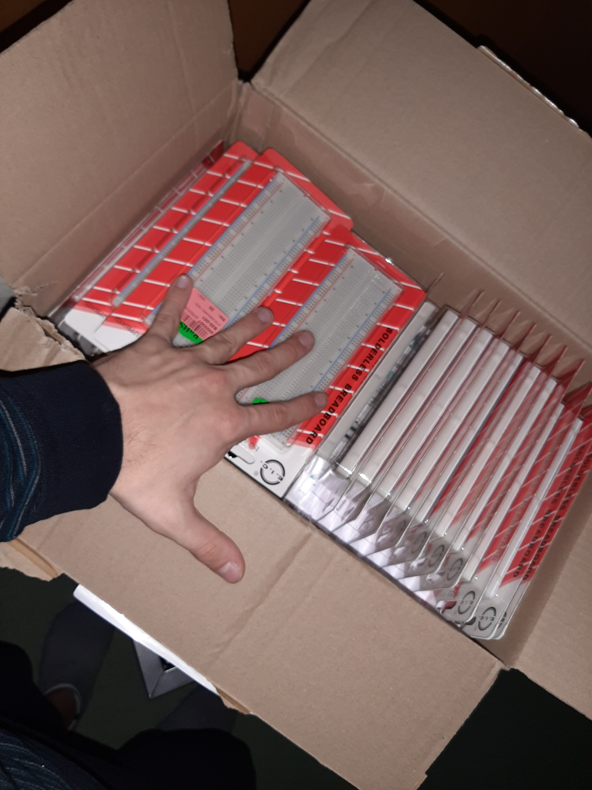
images/BreadBoards_03.jpg
