jufo-ufo/Breadboard-Computer/images/Button_01.jpg

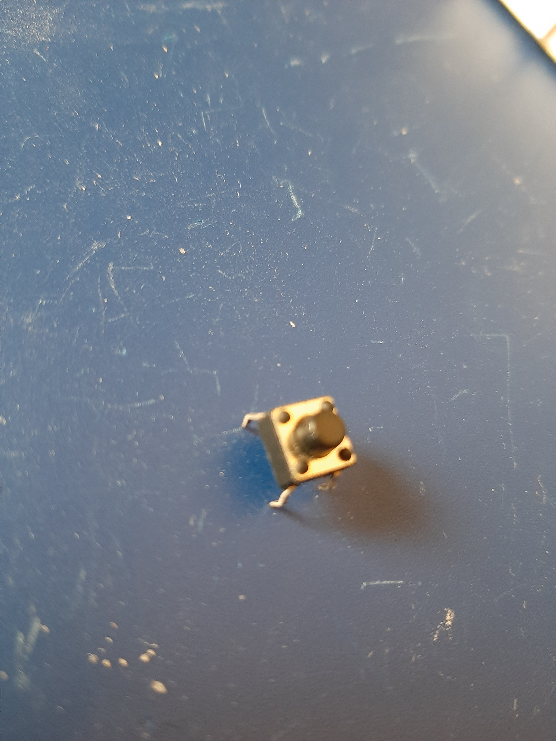
images/Button_01.jpg
