jufo-ufo/Breadboard-Computer/images/CD4098BE_HL.png

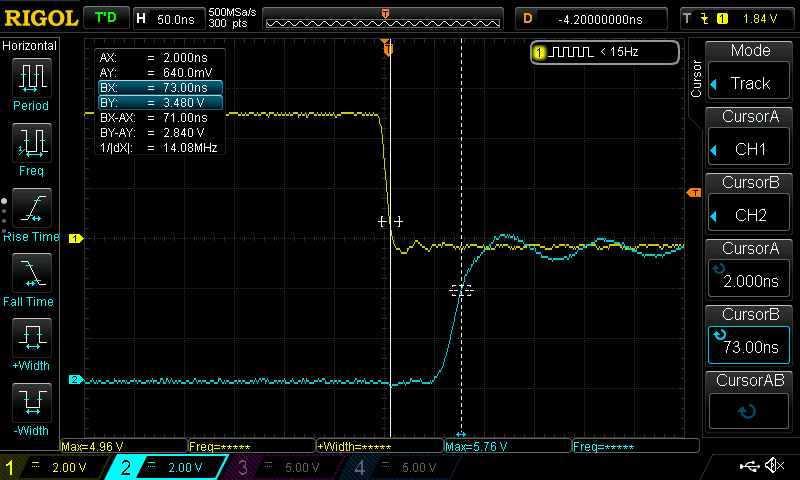
images/CD4098BE_HL.png
