jufo-ufo/Breadboard-Computer/images/computer_simple_logic_schmatic.png

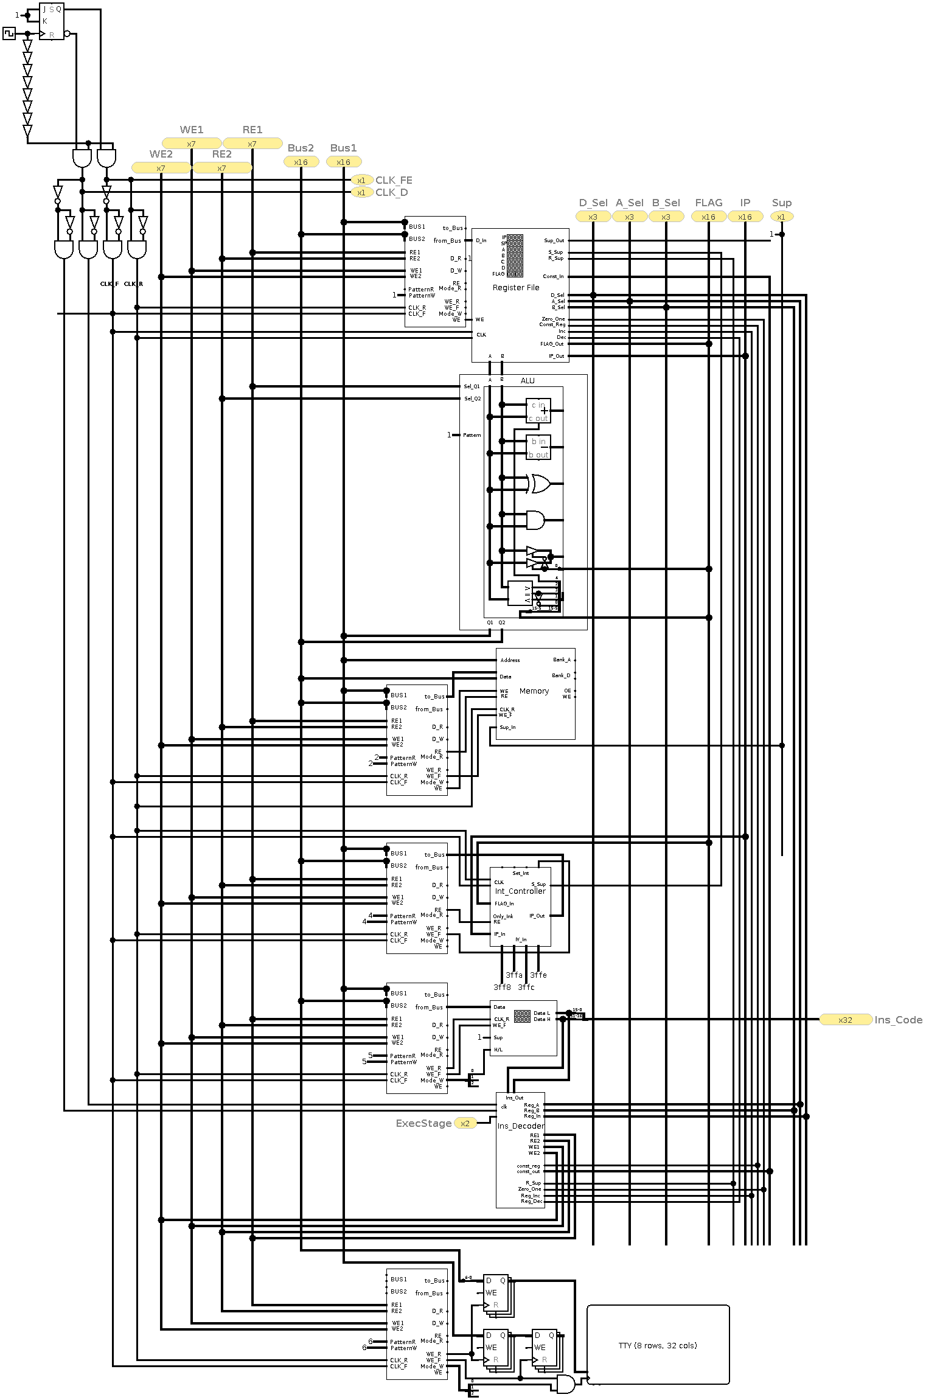
images/computer_simple_logic_schmatic.png
