jufo-ufo/Breadboard-Computer/images/Computer_V01_Chaos_07.jpg

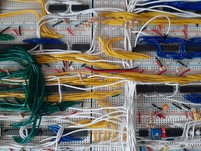
images/Computer_V01_Chaos_07.jpg
