jufo-ufo/Breadboard-Computer/images/Die Messung.jpg

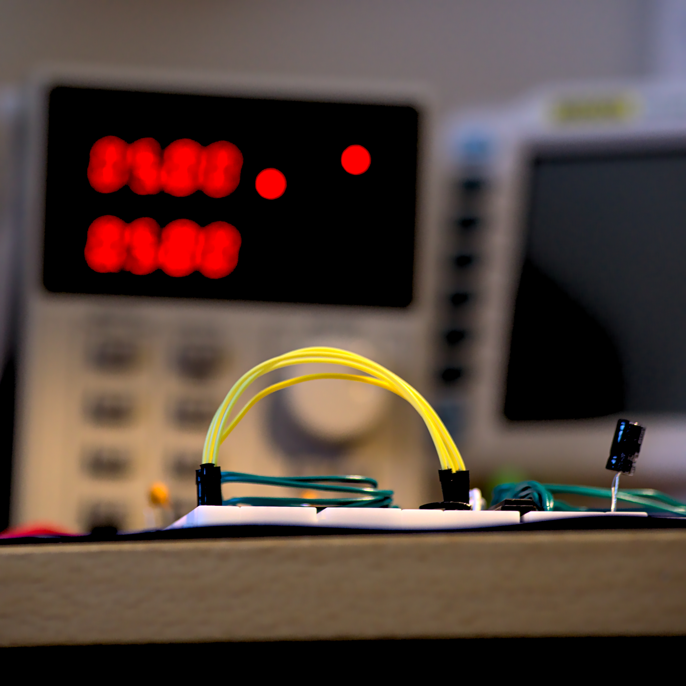
images/Die Messung.jpg
