jufo-ufo/Breadboard-Computer/images/E2_Cl_1,0,1_WP_20200723_15_37_34_Pro_Li.jpg

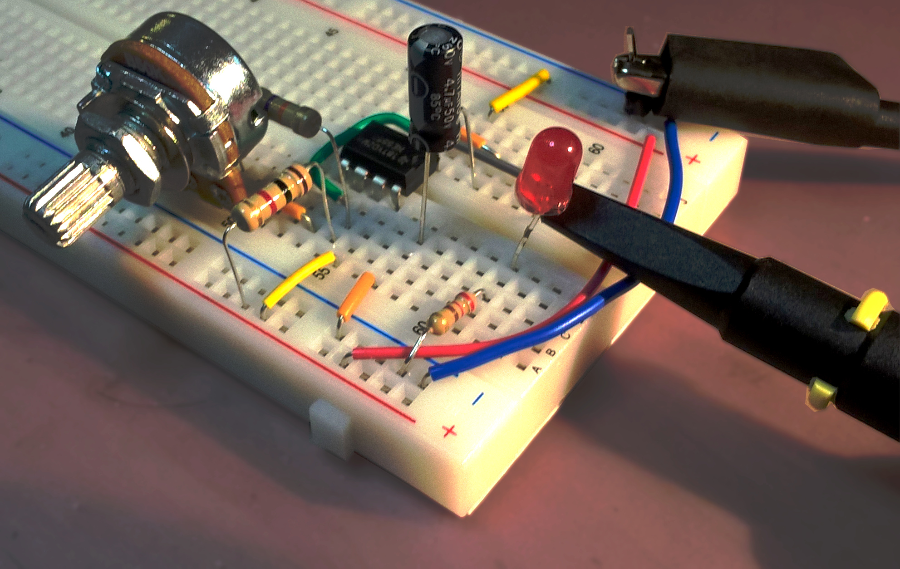
images/E2_Cl_1,0,1_WP_20200723_15_37_34_Pro_Li.jpg
