jufo-ufo/Breadboard-Computer/images/E2_Cl_1,1,1_WP_20200723_15_51_01_Pro_LI.jpg

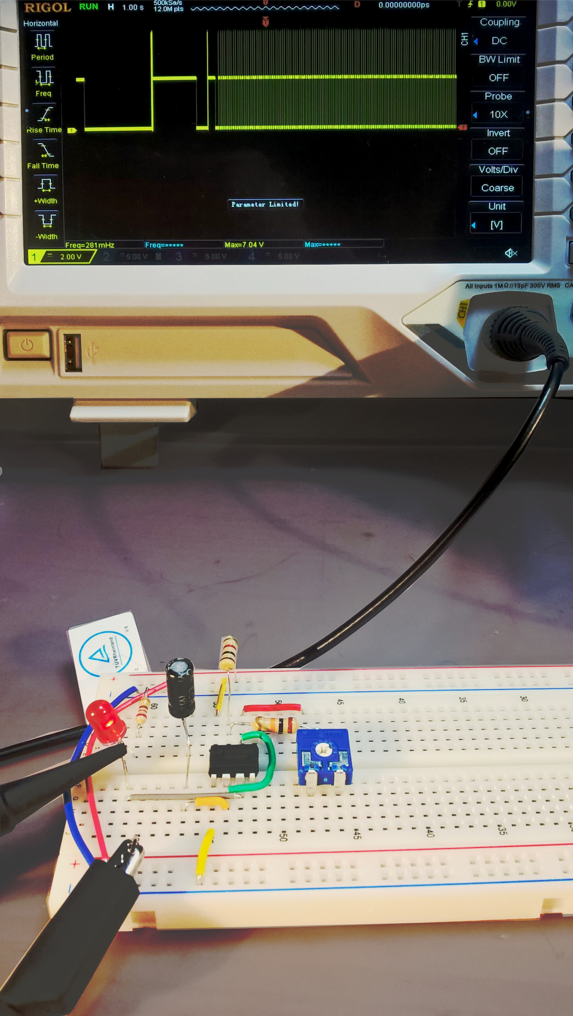
images/E2_Cl_1,1,1_WP_20200723_15_51_01_Pro_LI.jpg
