jufo-ufo/Breadboard-Computer/images/E2_Cl_2,0,1_WP_20200723_15_39_46_Pro_LI.jpg

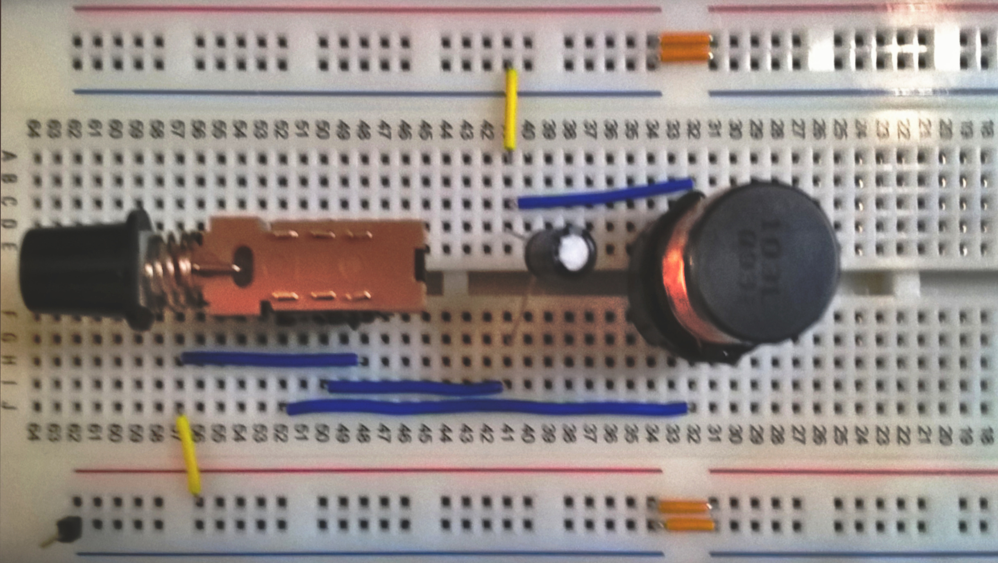
images/E2_Cl_2,0,1_WP_20200723_15_39_46_Pro_LI.jpg
