jufo-ufo/Breadboard-Computer/images/E_Cl_1,0,1_WP_20200723_15_37_34_Pro_Li.jpg

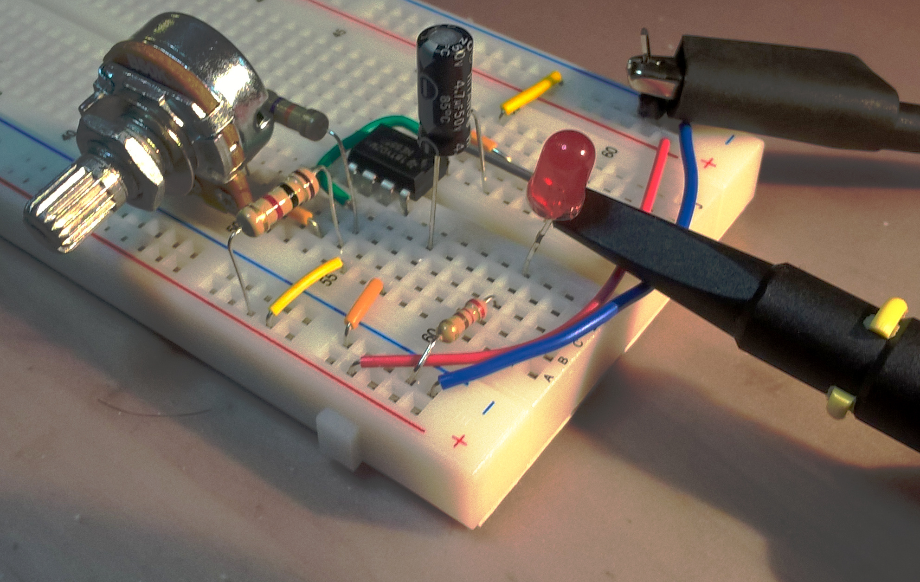
images/E_Cl_1,0,1_WP_20200723_15_37_34_Pro_Li.jpg
