jufo-ufo/Breadboard-Computer/images/E_Cl_1,0,1_WP_20200723_15_39_24_Pro_LI.jpg

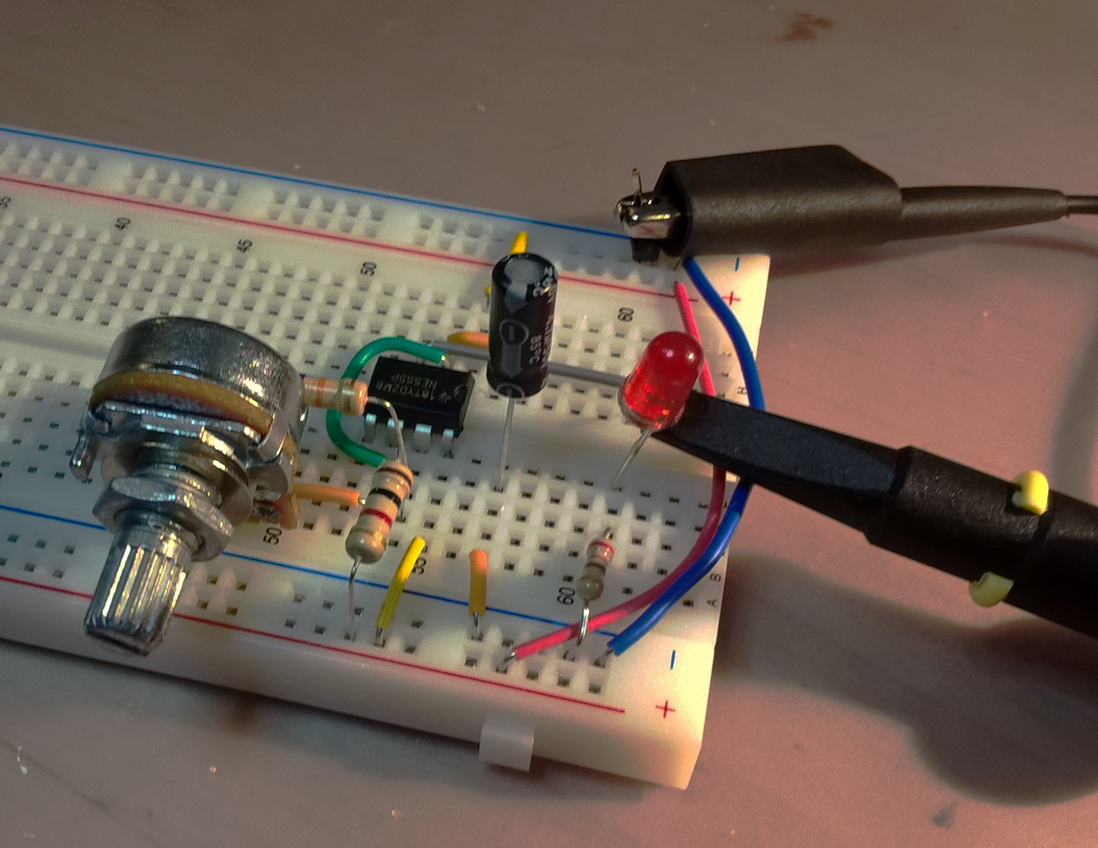
images/E_Cl_1,0,1_WP_20200723_15_39_24_Pro_LI.jpg
