jufo-ufo/Breadboard-Computer/images/E_Cl_1,1,1_WP_20200723_15_51_03_Pro_LI.jpg

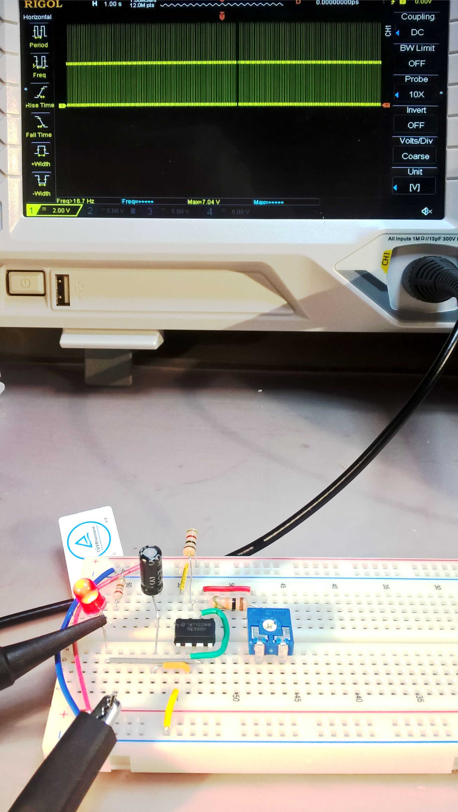
images/E_Cl_1,1,1_WP_20200723_15_51_03_Pro_LI.jpg
