jufo-ufo/Breadboard-Computer/images/E_Cl_2,0,1_WP_20200723_15_39_46_Pro_LI.jpg

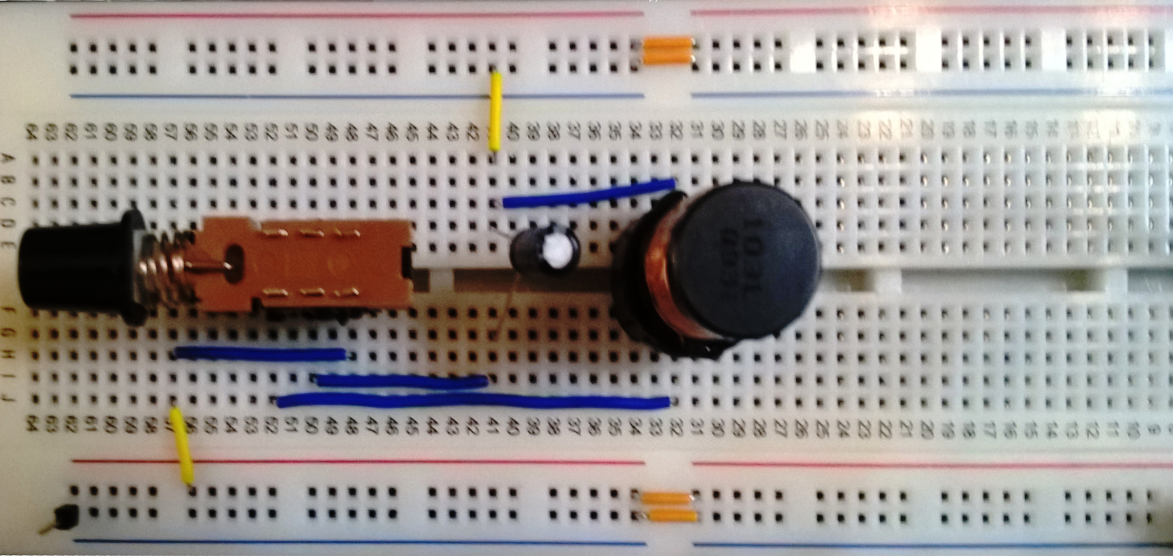
images/E_Cl_2,0,1_WP_20200723_15_39_46_Pro_LI.jpg
