jufo-ufo/Breadboard-Computer/images/Handy/AW1_01.jpg

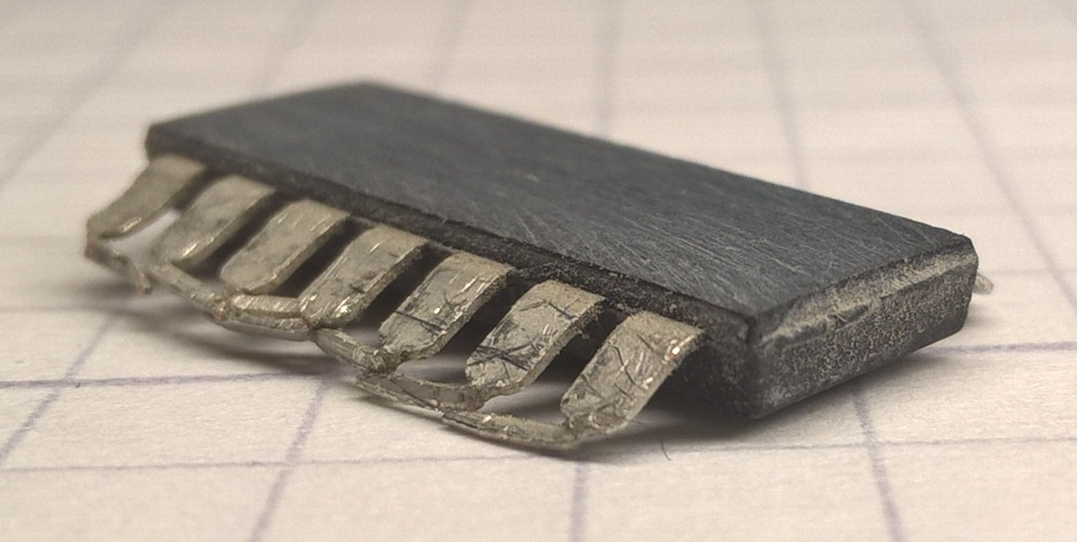
images/Handy/AW1_01.jpg
