jufo-ufo/Breadboard-Computer/images/Handy/AW1_04.jpg

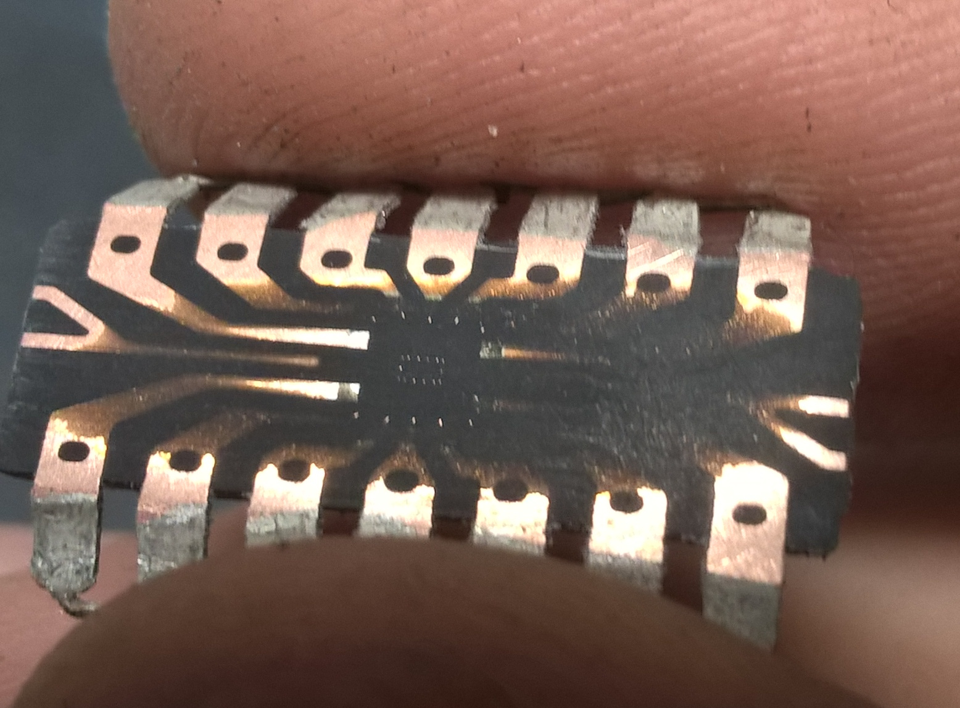
images/Handy/AW1_04.jpg
