jufo-ufo/Breadboard-Computer/images/Handy/AW1_07.jpg

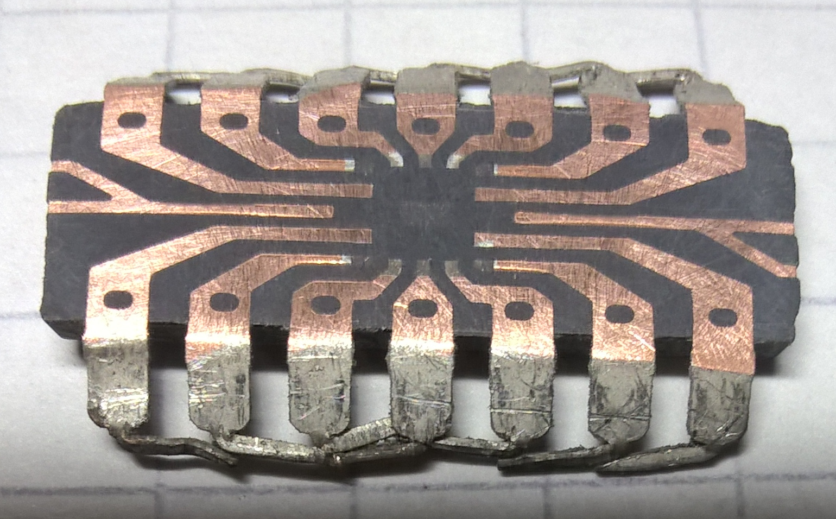
images/Handy/AW1_07.jpg
