jufo-ufo/Breadboard-Computer/images/Handy/AW1_08.jpg

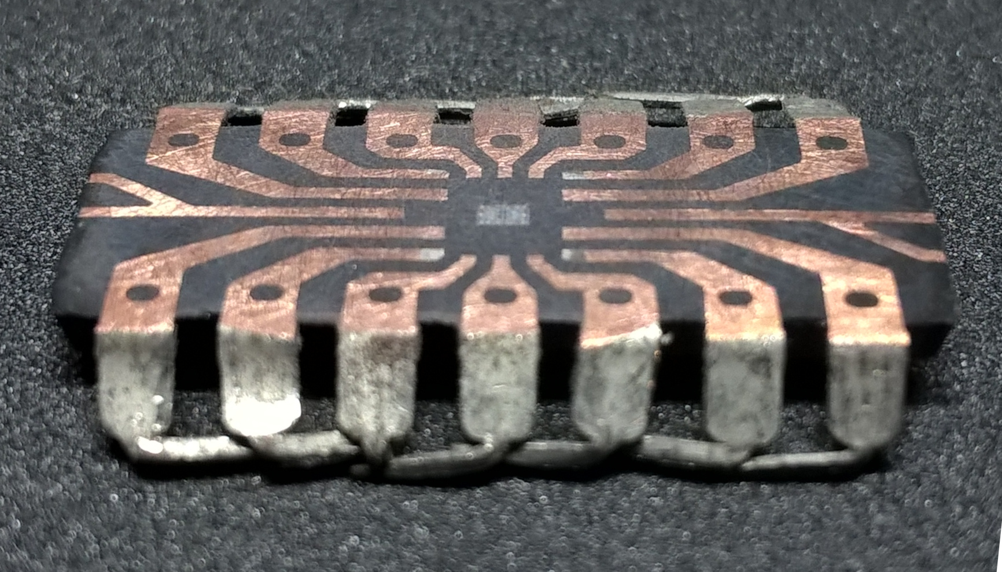
images/Handy/AW1_08.jpg
