jufo-ufo/Breadboard-Computer/images/Handy/AW1_11.jpg

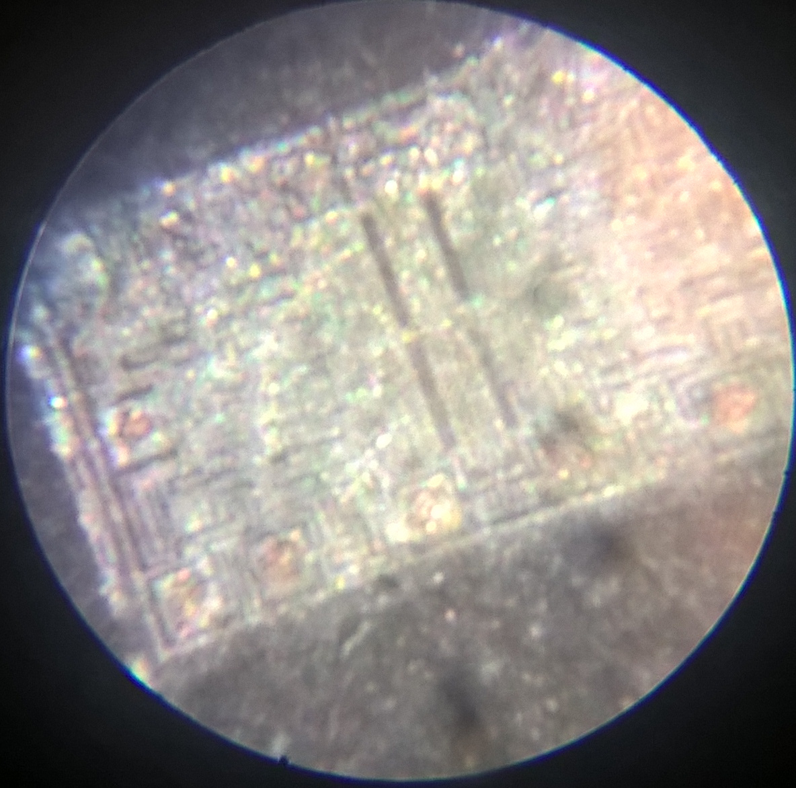
images/Handy/AW1_11.jpg
