jufo-ufo/Breadboard-Computer/images/Handy/AW1_12.jpg

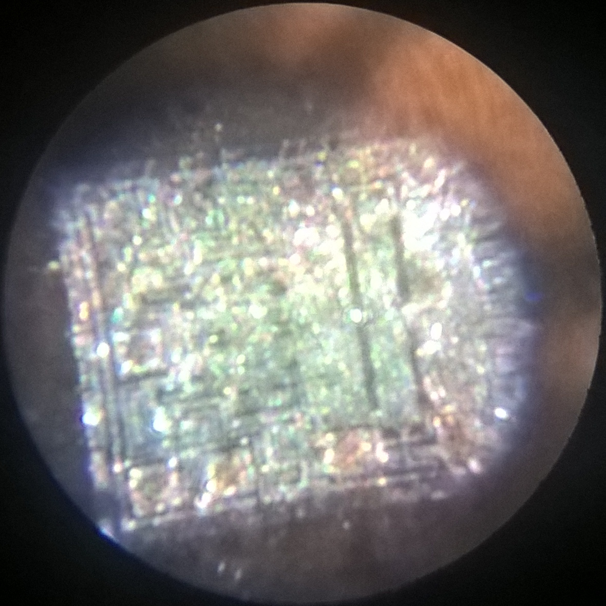
images/Handy/AW1_12.jpg
