jufo-ufo/Breadboard-Computer/images/Handy/Chip_Internal/WP_20210917_11_34_52_Pro.jpg

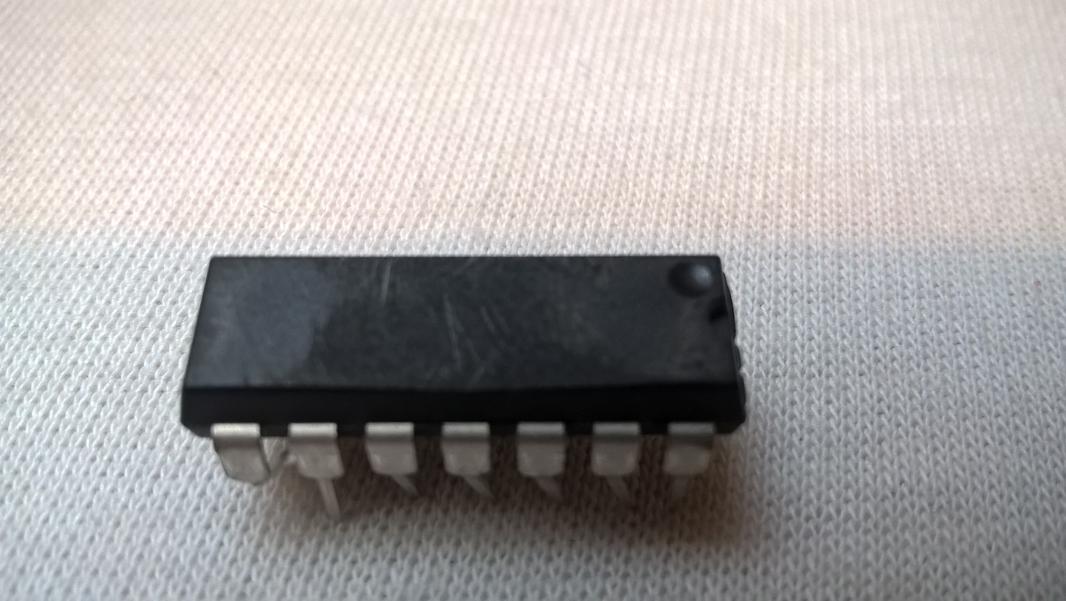
images/Handy/Chip_Internal/WP_20210917_11_34_52_Pro.jpg
