jufo-ufo/Breadboard-Computer/images/Handy/Chip_Internal/WP_20210917_15_44_31_Pro.jpg

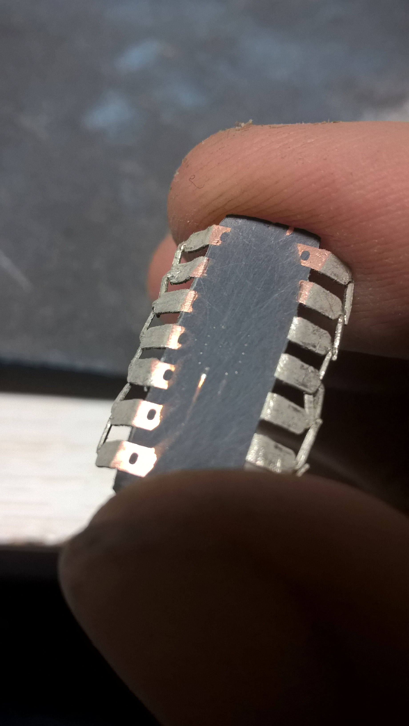
images/Handy/Chip_Internal/WP_20210917_15_44_31_Pro.jpg
