jufo-ufo/Breadboard-Computer/images/Handy/Chip_Internal/WP_20210917_15_47_55_Pro.jpg

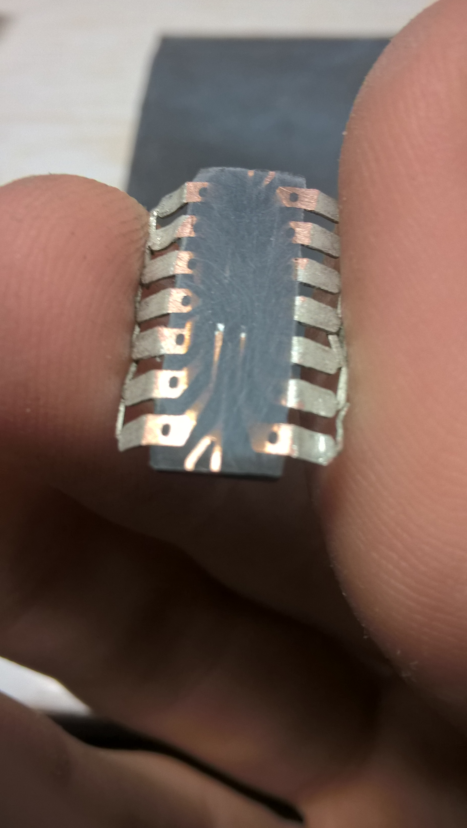
images/Handy/Chip_Internal/WP_20210917_15_47_55_Pro.jpg
