jufo-ufo/Breadboard-Computer/images/Handy/Chip_Internal/WP_20210917_15_48_05_Pro.jpg

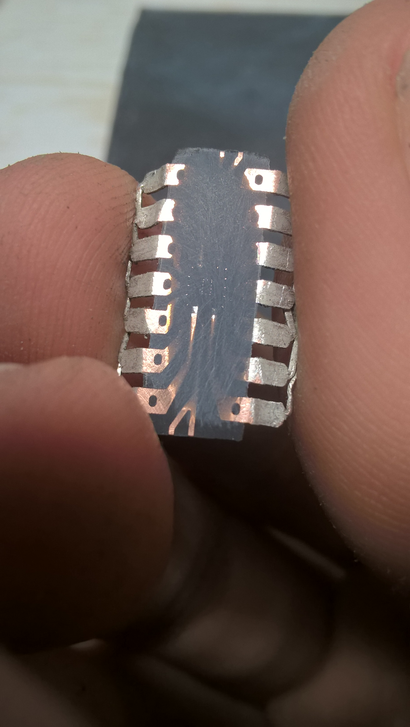
images/Handy/Chip_Internal/WP_20210917_15_48_05_Pro.jpg
