jufo-ufo/Breadboard-Computer/images/Handy/Chip_Internal/WP_20210917_15_48_15_Pro.jpg

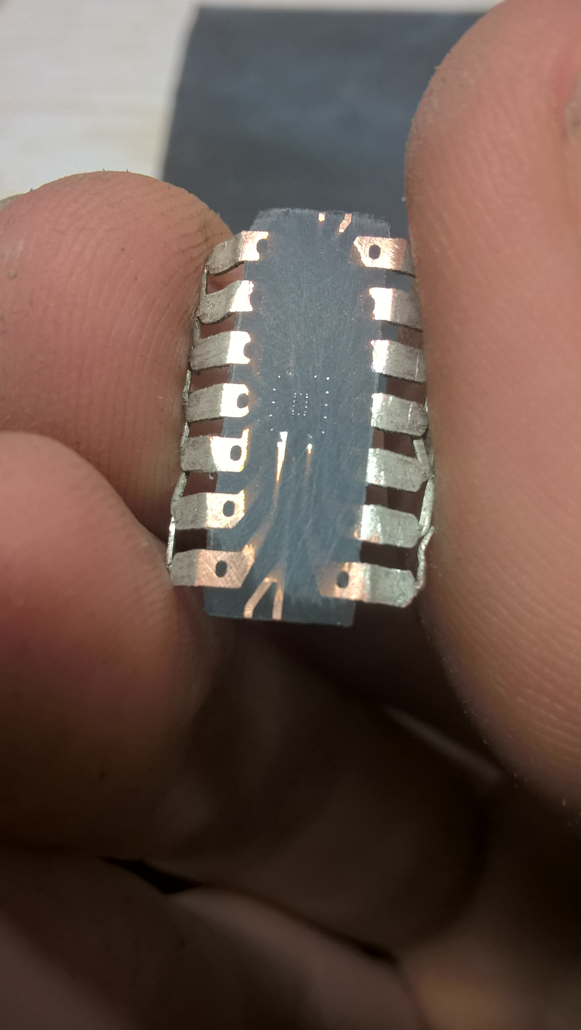
images/Handy/Chip_Internal/WP_20210917_15_48_15_Pro.jpg
