jufo-ufo/Breadboard-Computer/images/Handy/Chip_Internal/WP_20210917_16_27_23_Pro.jpg

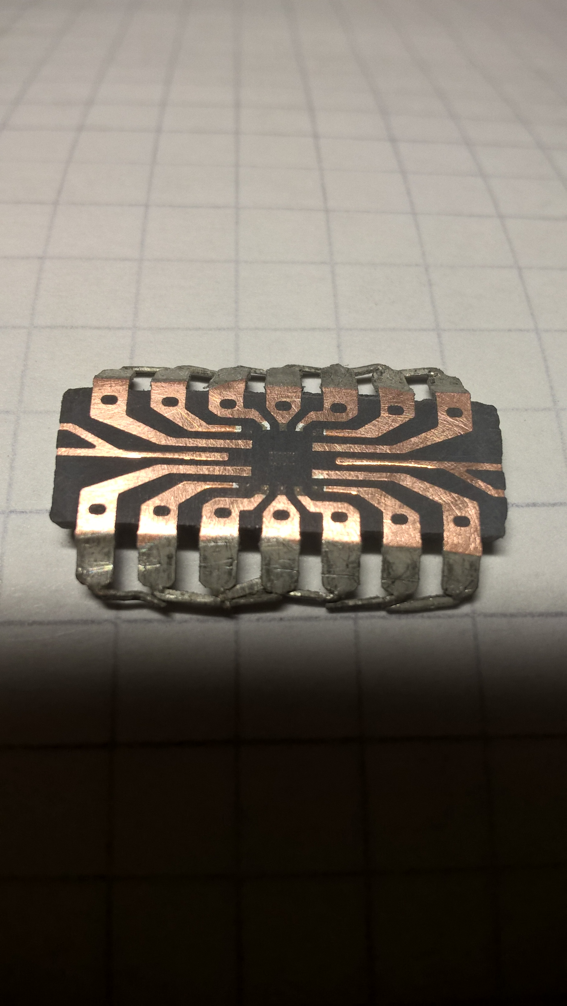
images/Handy/Chip_Internal/WP_20210917_16_27_23_Pro.jpg
