jufo-ufo/Breadboard-Computer/images/Handy/Chip_Internal/WP_20210917_16_41_42_Pro.jpg

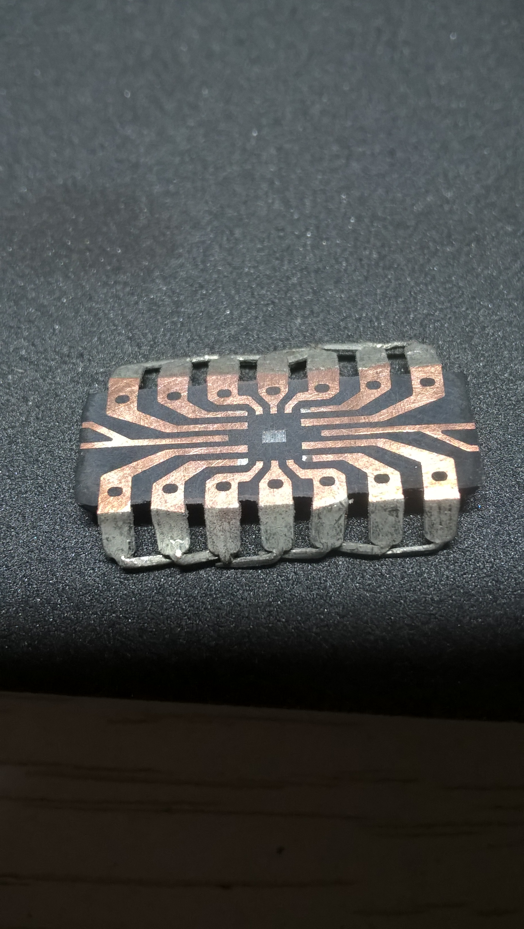
images/Handy/Chip_Internal/WP_20210917_16_41_42_Pro.jpg
