jufo-ufo/Breadboard-Computer/images/Handy/Chip_Internal/WP_20210917_16_53_45_Pro.jpg

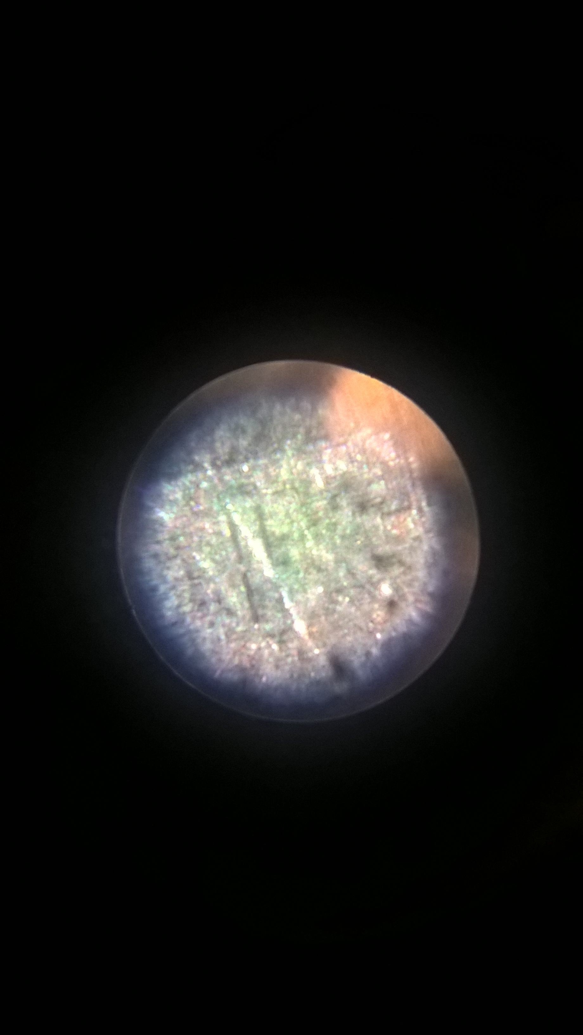
images/Handy/Chip_Internal/WP_20210917_16_53_45_Pro.jpg
