jufo-ufo/Breadboard-Computer/images/Handy/Chip_Internal/WP_20210917_17_05_36_Pro.jpg

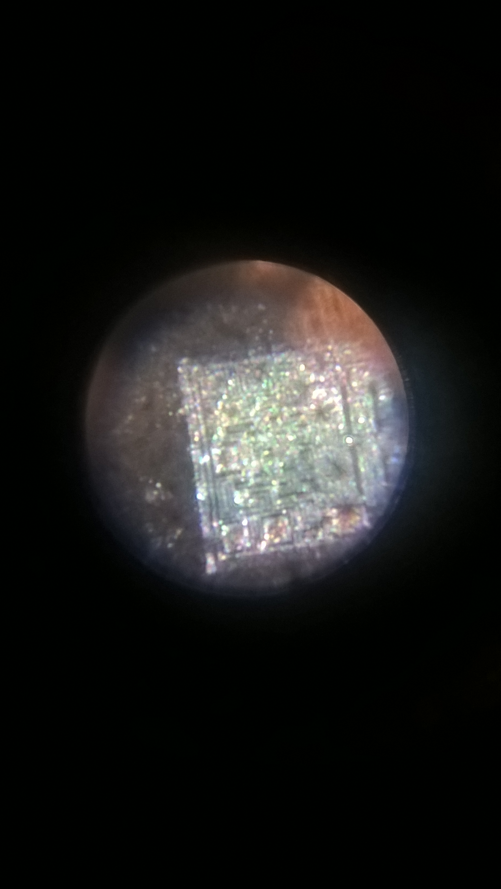
images/Handy/Chip_Internal/WP_20210917_17_05_36_Pro.jpg
