jufo-ufo/Breadboard-Computer/images/Handy/Chip_Internal/WP_20210917_17_08_53_Pro.jpg

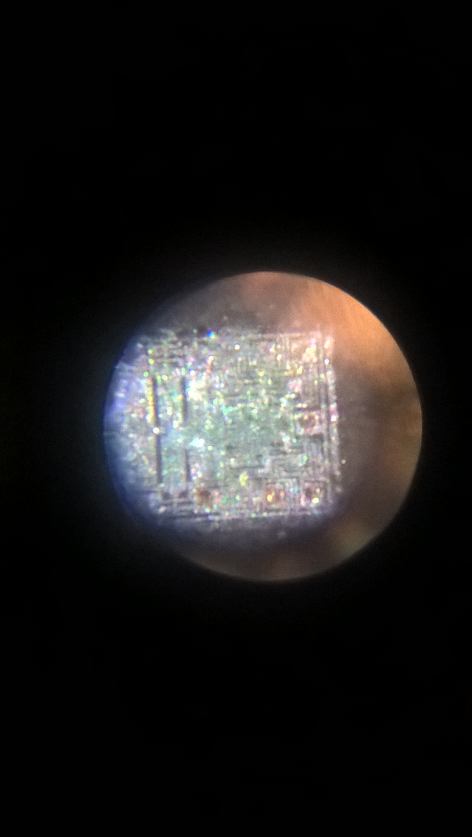
images/Handy/Chip_Internal/WP_20210917_17_08_53_Pro.jpg
