jufo-ufo/Breadboard-Computer/images/Handy/WP_20200723_15_39_46_Pro_LI.jpg

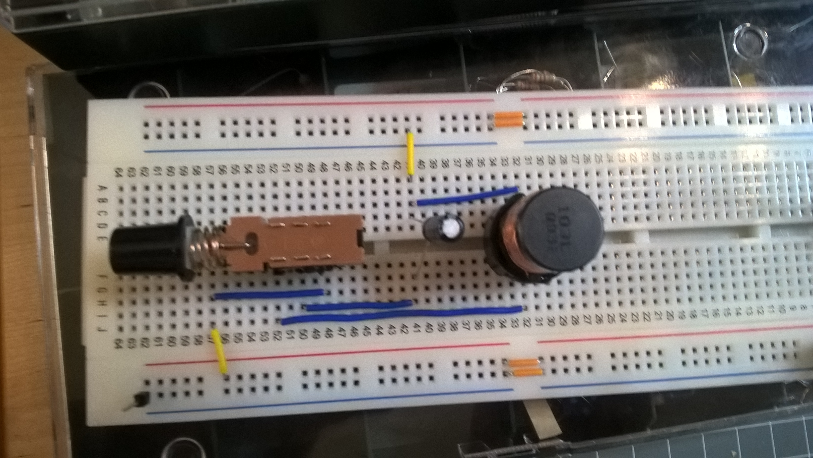
images/Handy/WP_20200723_15_39_46_Pro_LI.jpg
