jufo-ufo/Breadboard-Computer/images/Handy/WP_20200723_15_41_38_Pro_LI.jpg

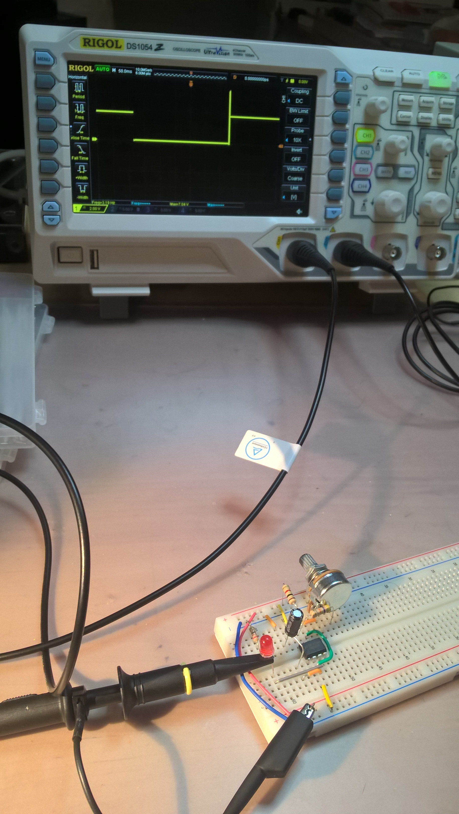
images/Handy/WP_20200723_15_41_38_Pro_LI.jpg
