jufo-ufo/Breadboard-Computer/images/Handy/WP_20200723_15_50_23_Pro_LI.jpg

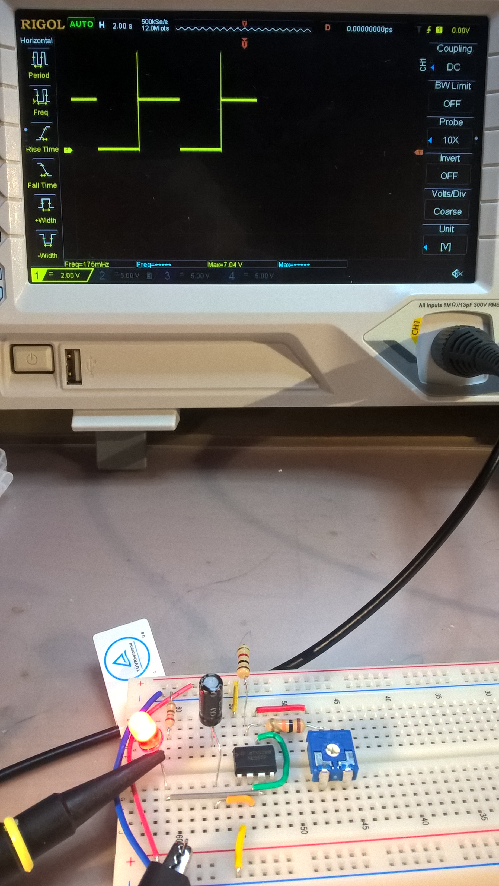
images/Handy/WP_20200723_15_50_23_Pro_LI.jpg
