jufo-ufo/Breadboard-Computer/images/Handy/WP_20200723_15_51_03_Pro.jpg

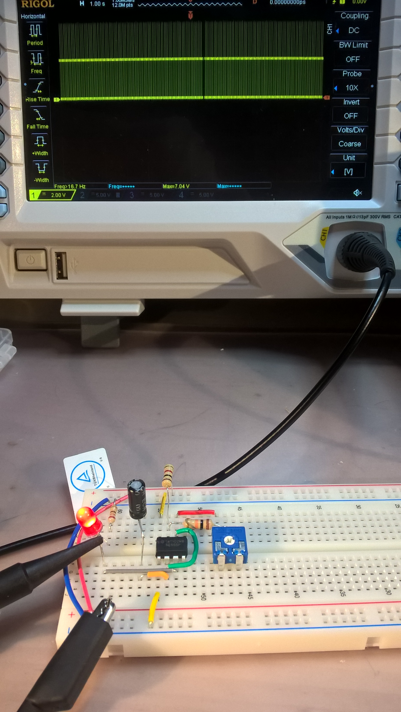
images/Handy/WP_20200723_15_51_03_Pro.jpg
