jufo-ufo/Breadboard-Computer/images/Handy/WP_20200723_15_52_55_Pro_LI.jpg

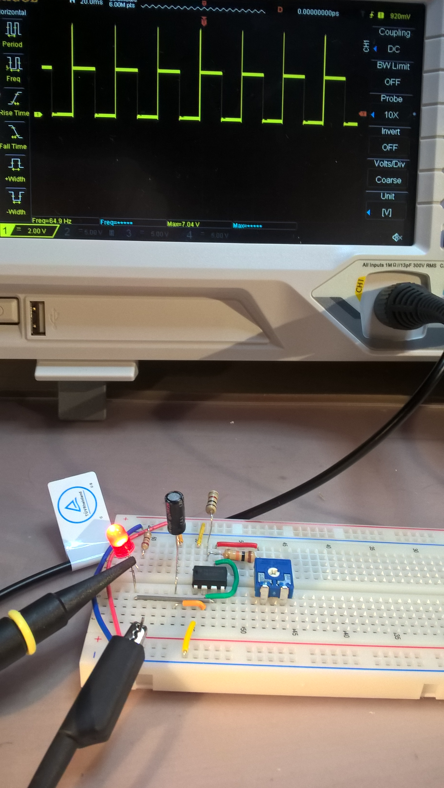
images/Handy/WP_20200723_15_52_55_Pro_LI.jpg
