jufo-ufo/Breadboard-Computer/images/Handy/WP_20200827_14_12_05_Pro.jpg

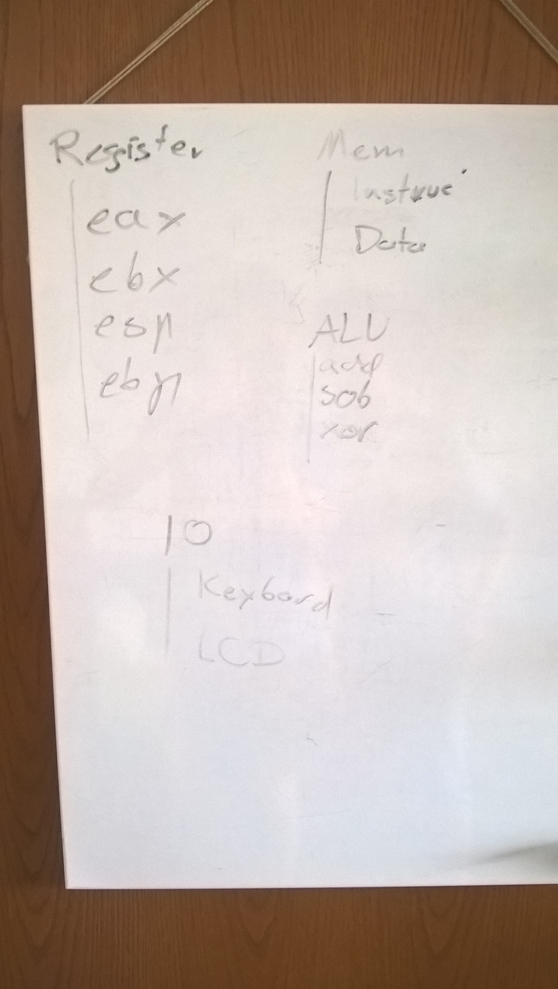
images/Handy/WP_20200827_14_12_05_Pro.jpg
