jufo-ufo/Breadboard-Computer/images/Handy/WP_20200827_16_18_14_Pro.jpg

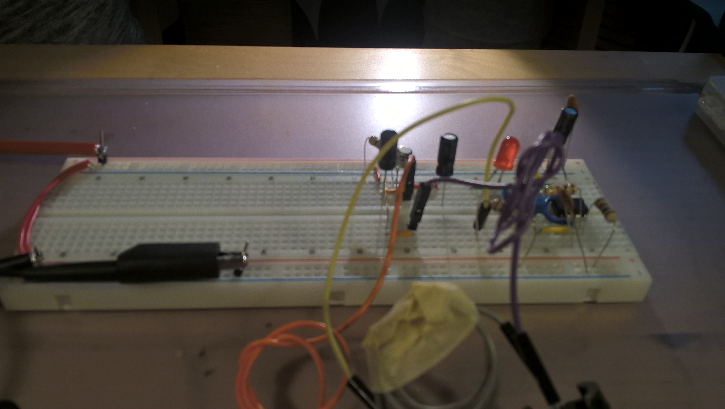
images/Handy/WP_20200827_16_18_14_Pro.jpg
