jufo-ufo/Breadboard-Computer/images/Handy/WP_20200827_16_18_53_Pro.jpg

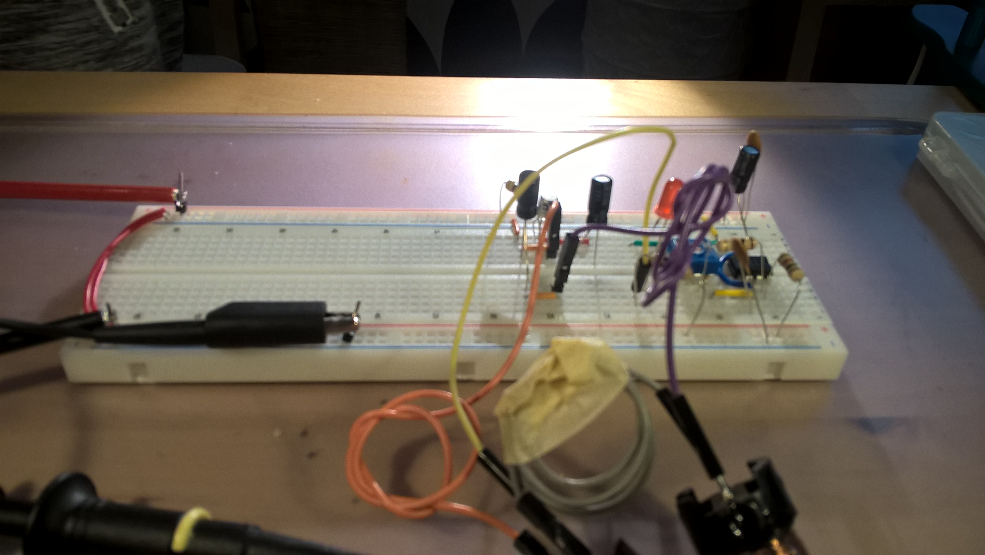
images/Handy/WP_20200827_16_18_53_Pro.jpg
