jufo-ufo/Breadboard-Computer/images/Handy/WP_20200827_16_18_55_Pro.jpg

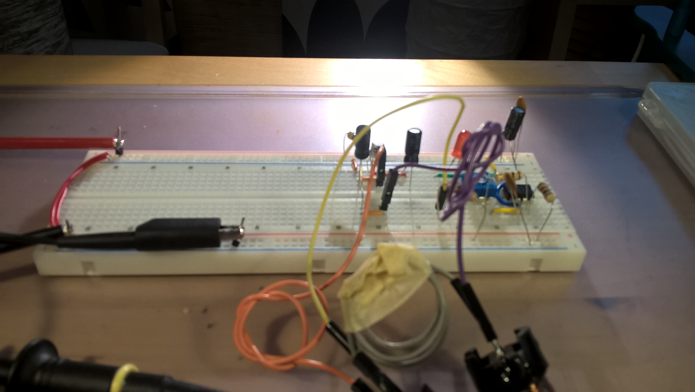
images/Handy/WP_20200827_16_18_55_Pro.jpg
