jufo-ufo/Breadboard-Computer/images/Handy/WP_20200827_16_19_35_Pro.jpg

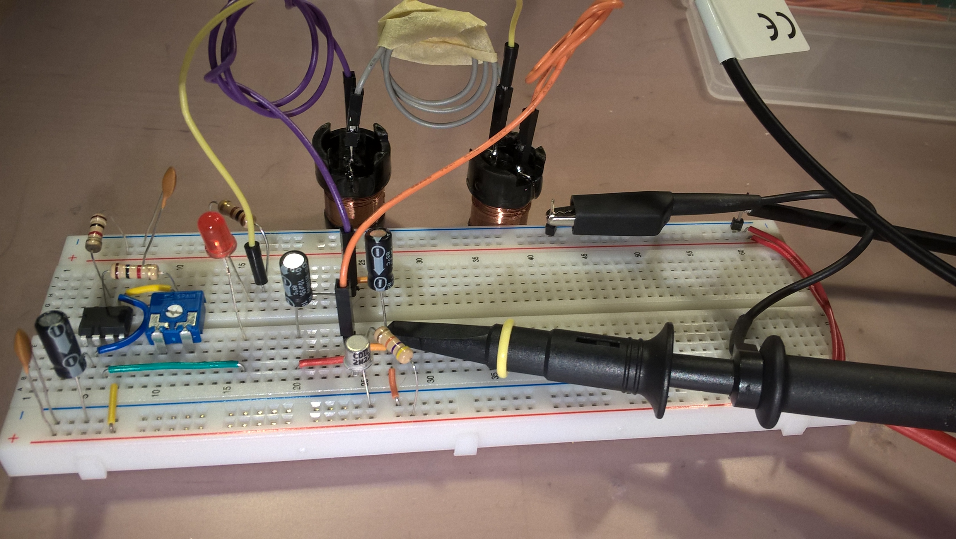
images/Handy/WP_20200827_16_19_35_Pro.jpg
