jufo-ufo/Breadboard-Computer/images/Handy/WP_20200827_16_19_47_Pro.jpg

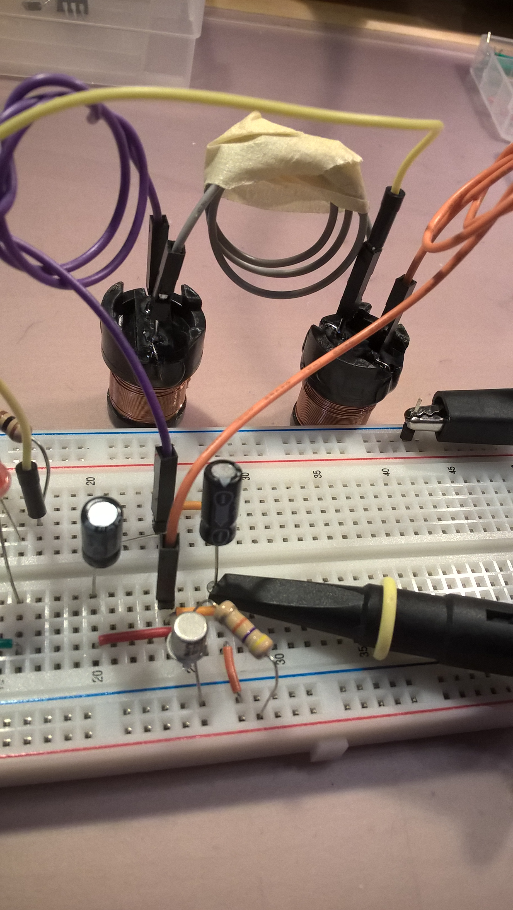
images/Handy/WP_20200827_16_19_47_Pro.jpg
