jufo-ufo/Breadboard-Computer/images/Handy/WP_20210613_11_29_26_Pro.jpg

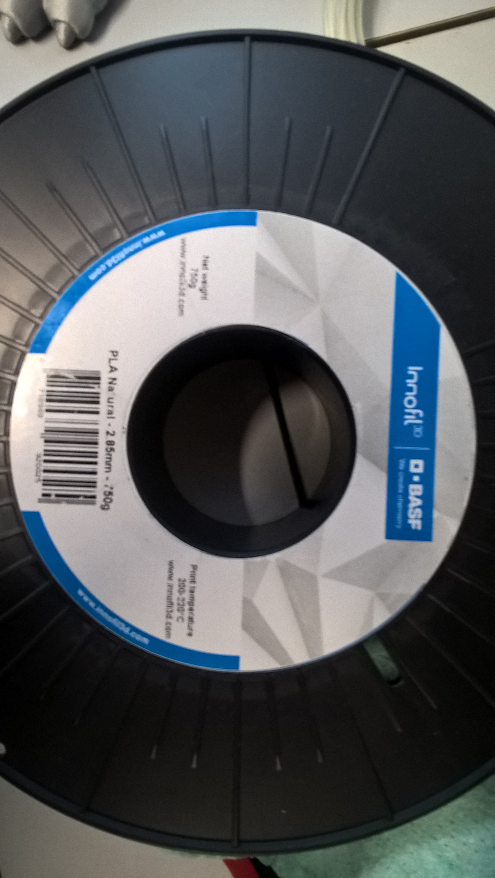
images/Handy/WP_20210613_11_29_26_Pro.jpg
