jufo-ufo/Breadboard-Computer/images/Handy/WP_20210613_11_29_43_Pro.jpg

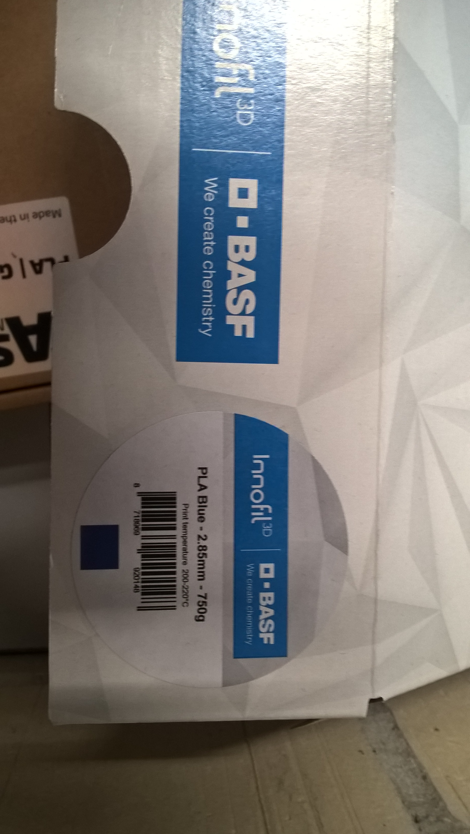
images/Handy/WP_20210613_11_29_43_Pro.jpg
