jufo-ufo/Breadboard-Computer/images/Handy/WP_20210704_20_40_22_Pro.jpg

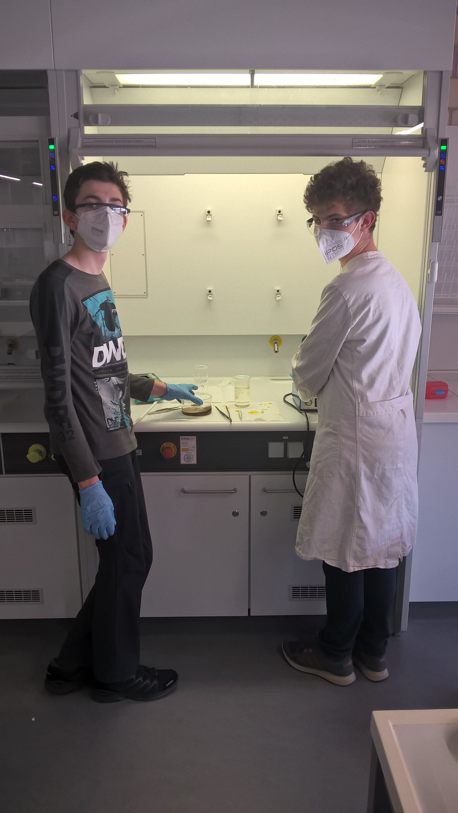
images/Handy/WP_20210704_20_40_22_Pro.jpg
