jufo-ufo/Breadboard-Computer/images/Handy/WP_20210704_20_40_26_Pro.jpg

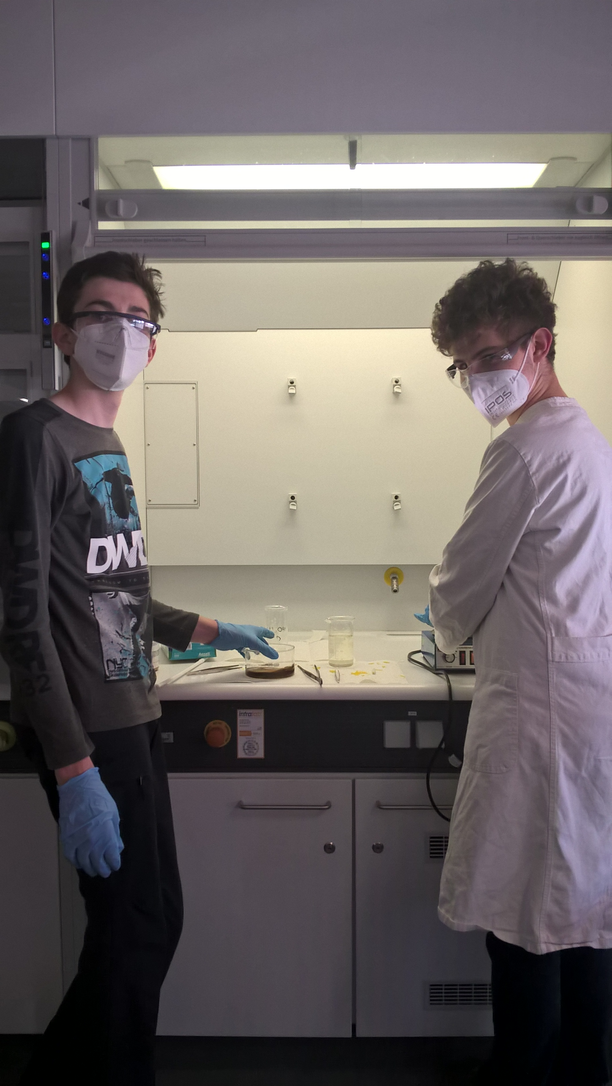
images/Handy/WP_20210704_20_40_26_Pro.jpg
