jufo-ufo/Breadboard-Computer/images/Handy/WP_20210704_20_50_03_Pro.jpg

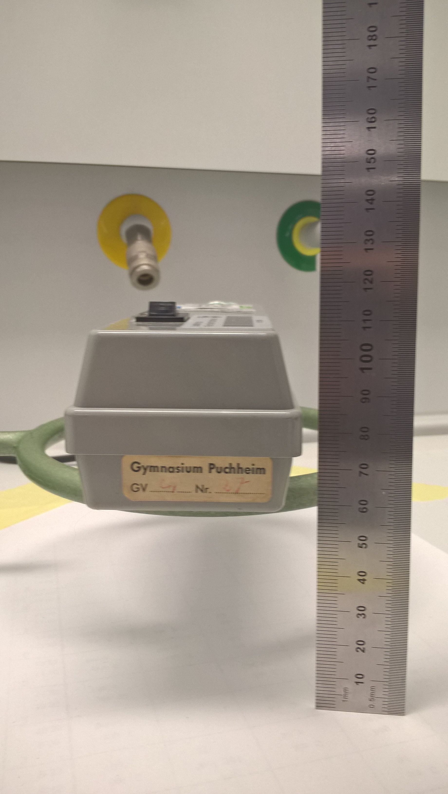
images/Handy/WP_20210704_20_50_03_Pro.jpg
