jufo-ufo/Breadboard-Computer/images/Handy/WP_20210704_20_50_20_Pro.jpg

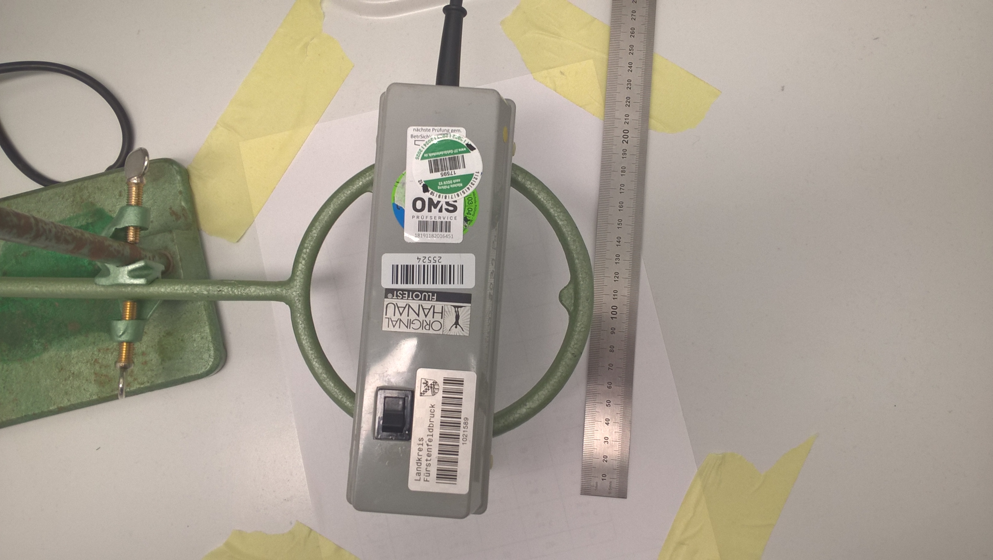
images/Handy/WP_20210704_20_50_20_Pro.jpg
