jufo-ufo/Breadboard-Computer/images/Handy/WP_20210704_20_52_17_Pro.jpg

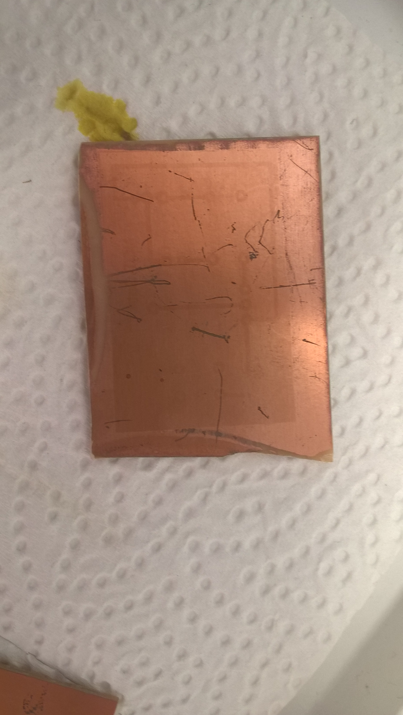
images/Handy/WP_20210704_20_52_17_Pro.jpg
