jufo-ufo/Breadboard-Computer/images/Handy/WP_20210704_20_53_24_Pro.jpg

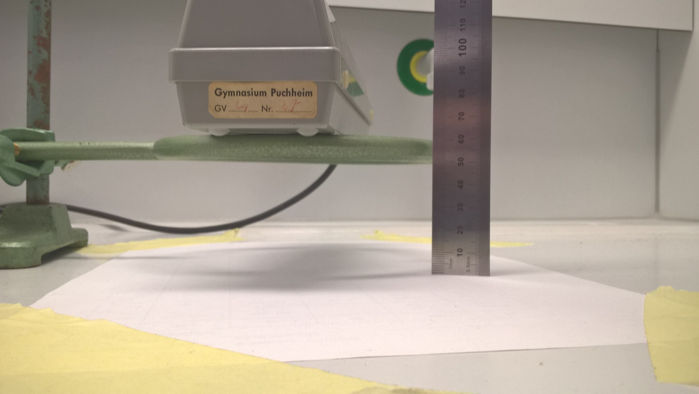
images/Handy/WP_20210704_20_53_24_Pro.jpg
