jufo-ufo/Breadboard-Computer/images/Handy/WP_20210704_20_53_40_Pro.jpg

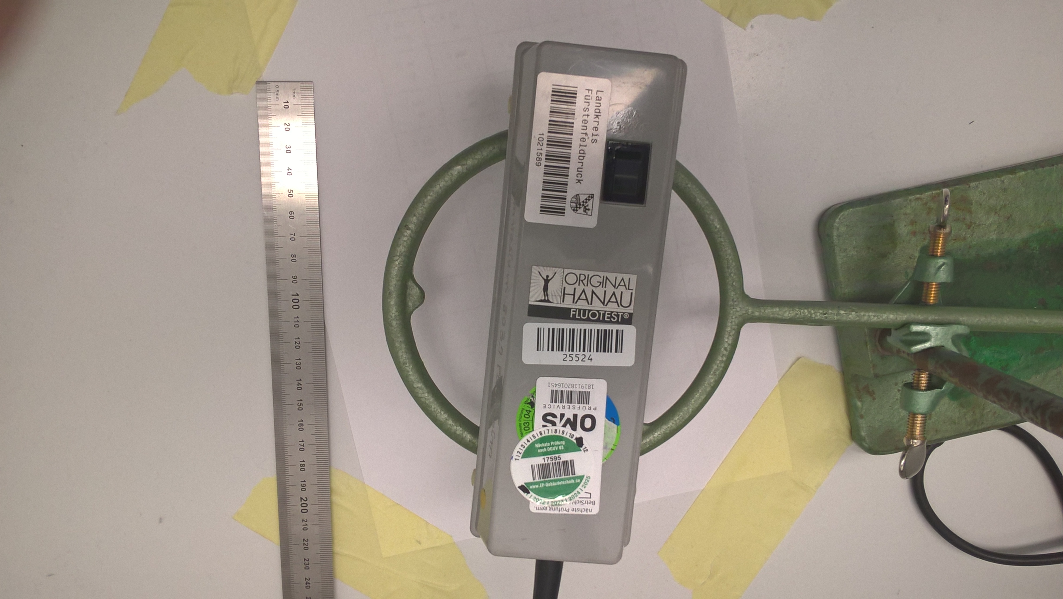
images/Handy/WP_20210704_20_53_40_Pro.jpg
