jufo-ufo/Breadboard-Computer/images/Handy/WP_20210704_20_54_10_Pro.jpg

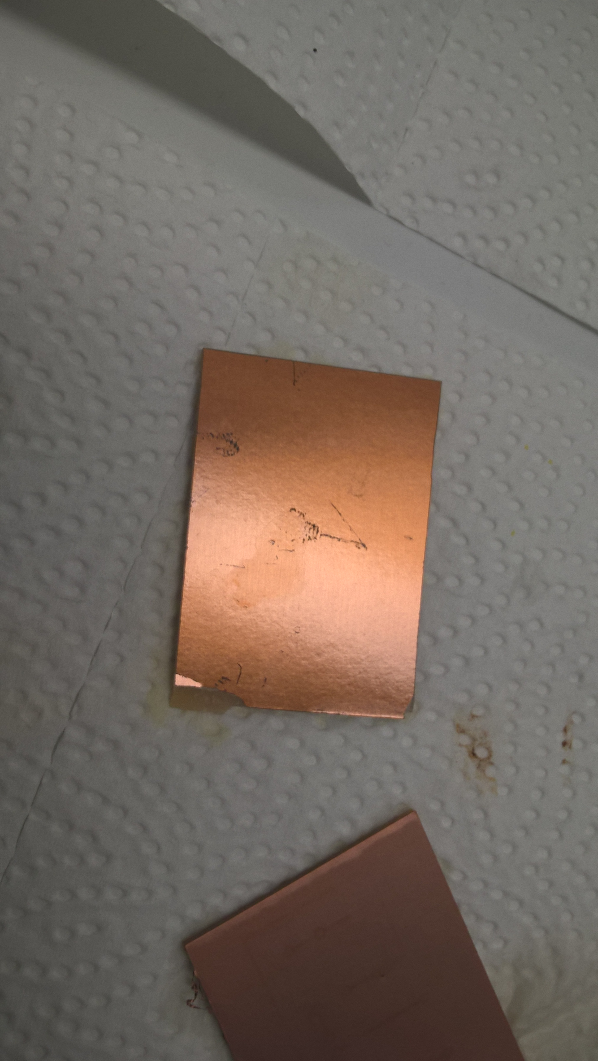
images/Handy/WP_20210704_20_54_10_Pro.jpg
