jufo-ufo/Breadboard-Computer/images/Handy/WP_20210704_20_54_21_Pro_.jpg

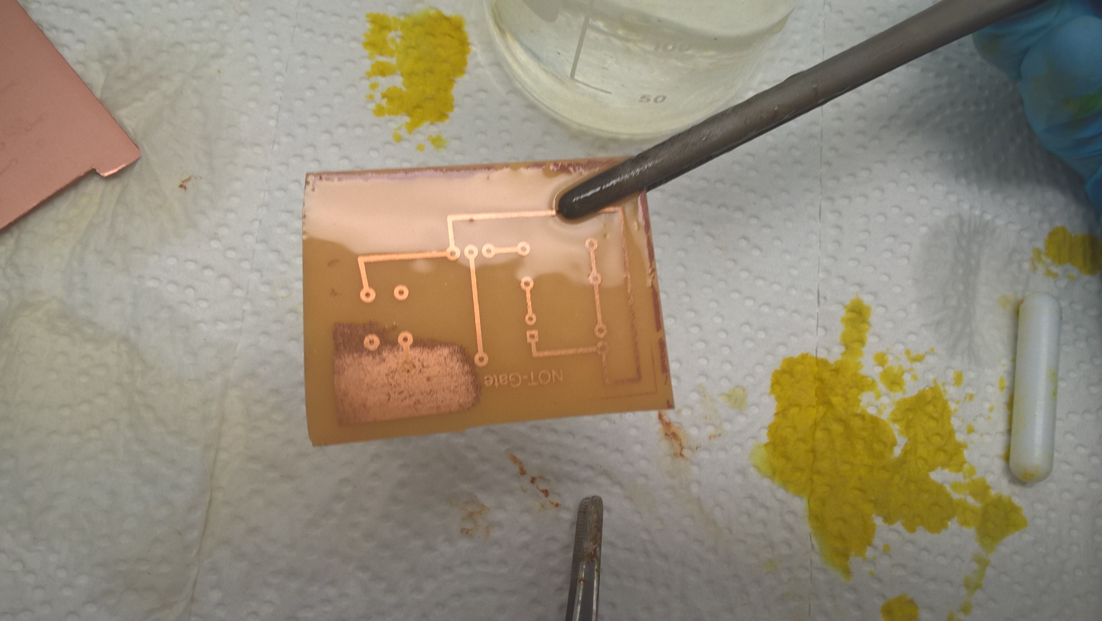
images/Handy/WP_20210704_20_54_21_Pro_.jpg
