jufo-ufo/Breadboard-Computer/images/Handy/WP_20210704_20_54_23_Pro.jpg

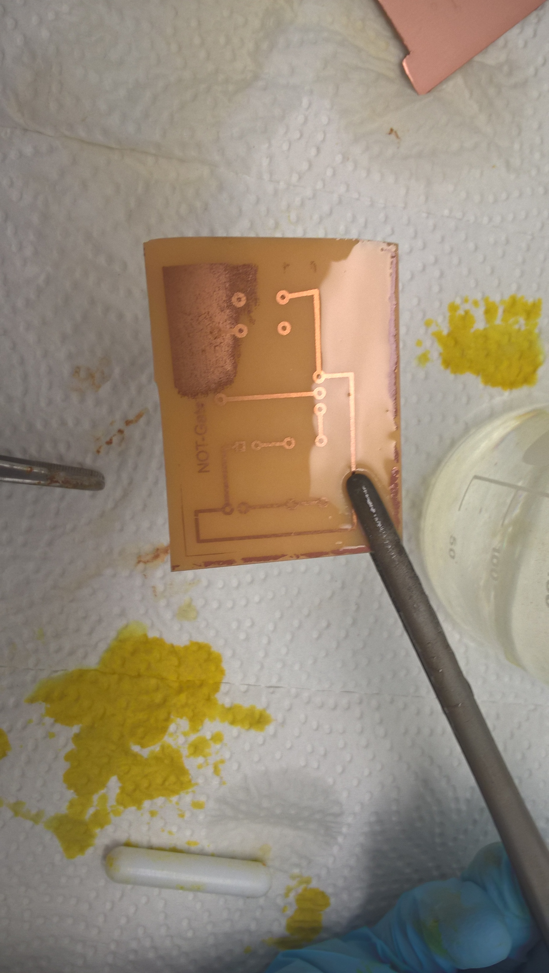
images/Handy/WP_20210704_20_54_23_Pro.jpg
