jufo-ufo/Breadboard-Computer/images/Handy/WP_20210704_20_54_25_Pro.jpg

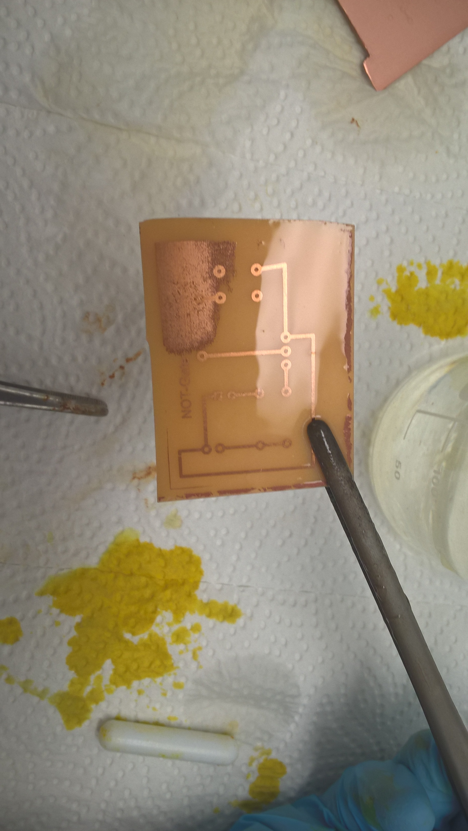
images/Handy/WP_20210704_20_54_25_Pro.jpg
