jufo-ufo/Breadboard-Computer/images/Handy/WP_20210706_14_21_39_Pro.jpg

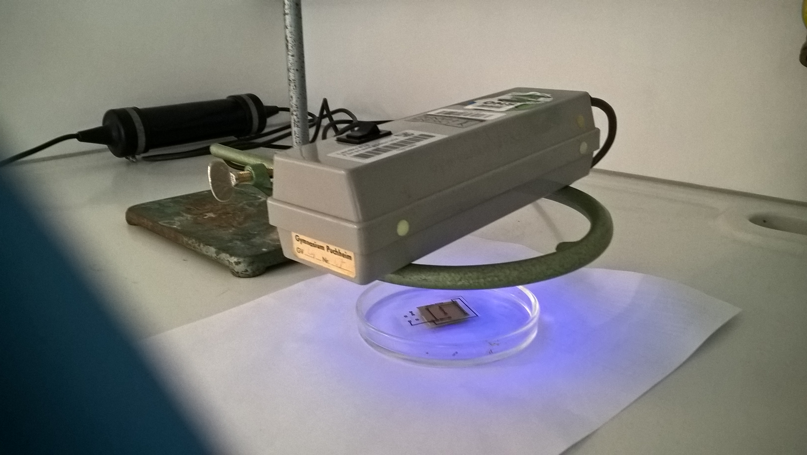
images/Handy/WP_20210706_14_21_39_Pro.jpg
