jufo-ufo/Breadboard-Computer/images/Handy/WP_20210706_14_22_03_Pro.jpg

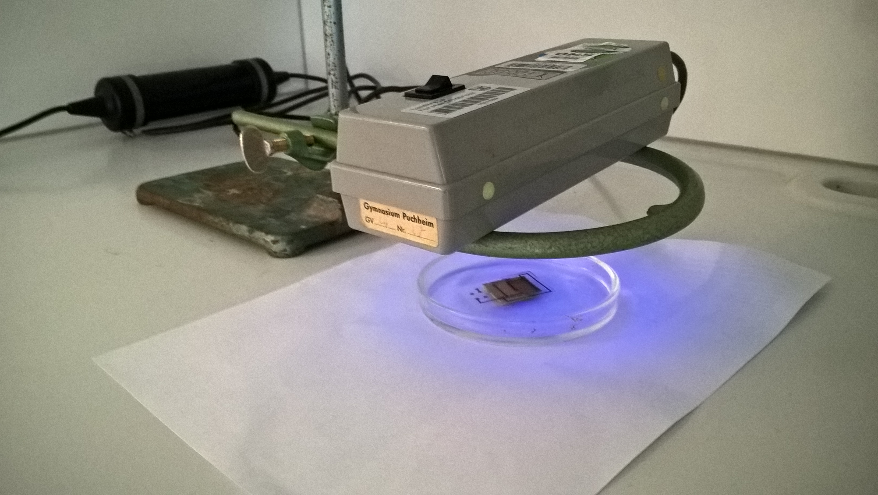
images/Handy/WP_20210706_14_22_03_Pro.jpg
