jufo-ufo/Breadboard-Computer/images/Handy/Chip_Internal/WP_20210917_11_38_46_Pro.jpg

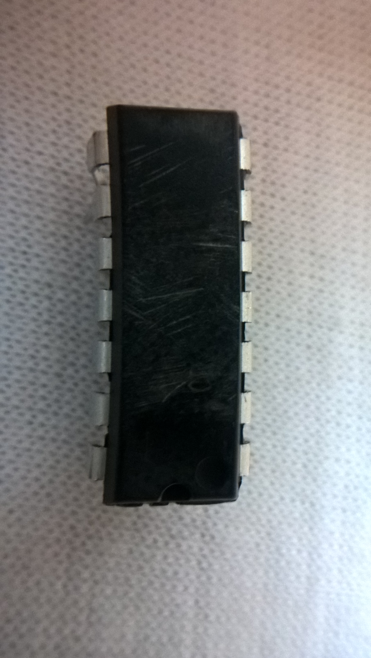
images/Handy/WP_20210917_11_38_46_Pro.jpg
