jufo-ufo/Breadboard-Computer/images/Handy/Chip_Internal/WP_20210917_15_24_53_Pro.jpg

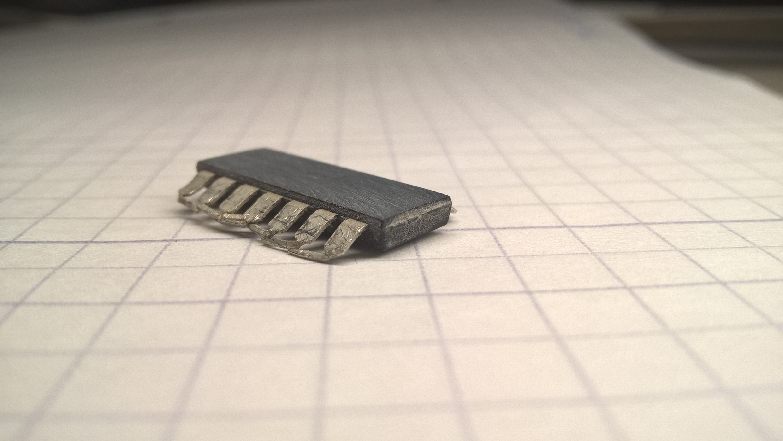
images/Handy/WP_20210917_15_24_53_Pro.jpg
