jufo-ufo/Breadboard-Computer/images/Handy/Chip_Internal/WP_20210917_15_25_36_Pro.jpg

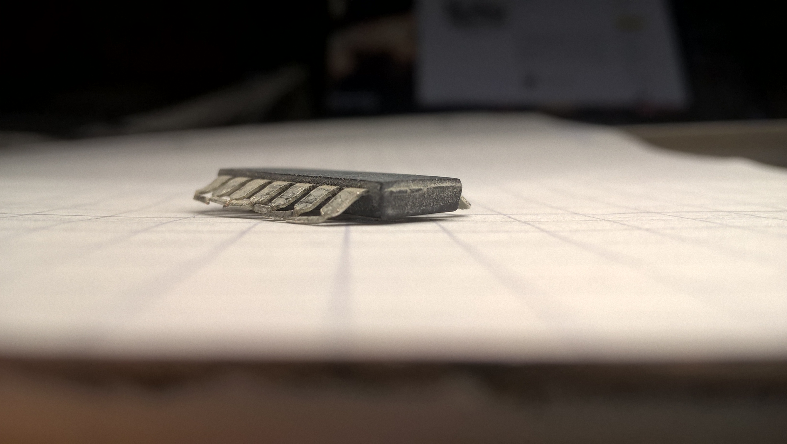
images/Handy/WP_20210917_15_25_36_Pro.jpg
