jufo-ufo/Breadboard-Computer/images/Handy/Chip_Internal/WP_20210917_15_53_03_Pro.jpg

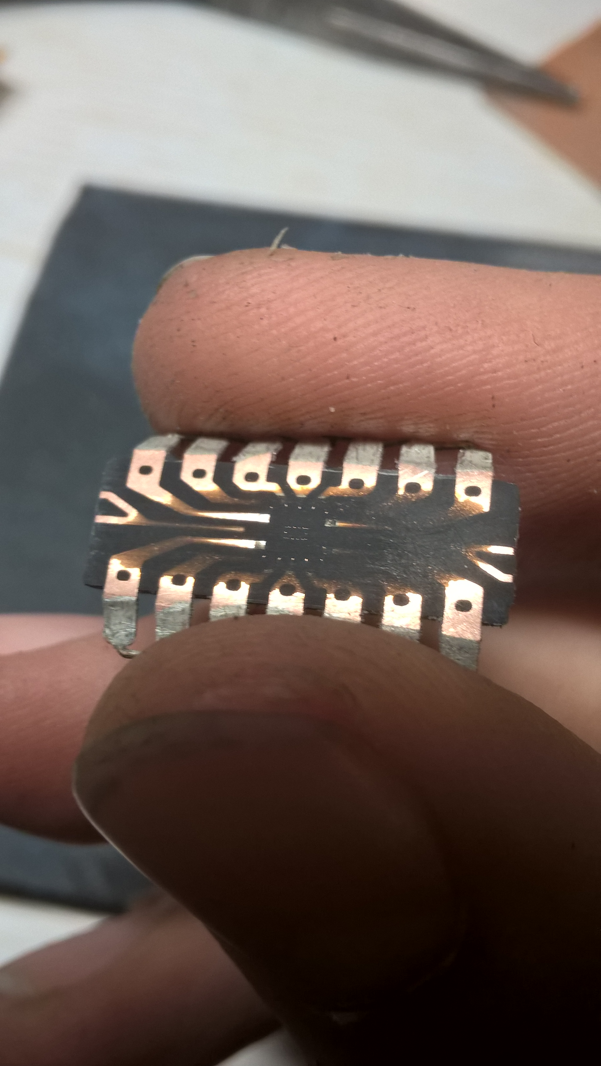
images/Handy/WP_20210917_15_53_03_Pro.jpg
