jufo-ufo/Breadboard-Computer/images/Handy/Chip_Internal/WP_20210917_16_01_44_Pro.jpg

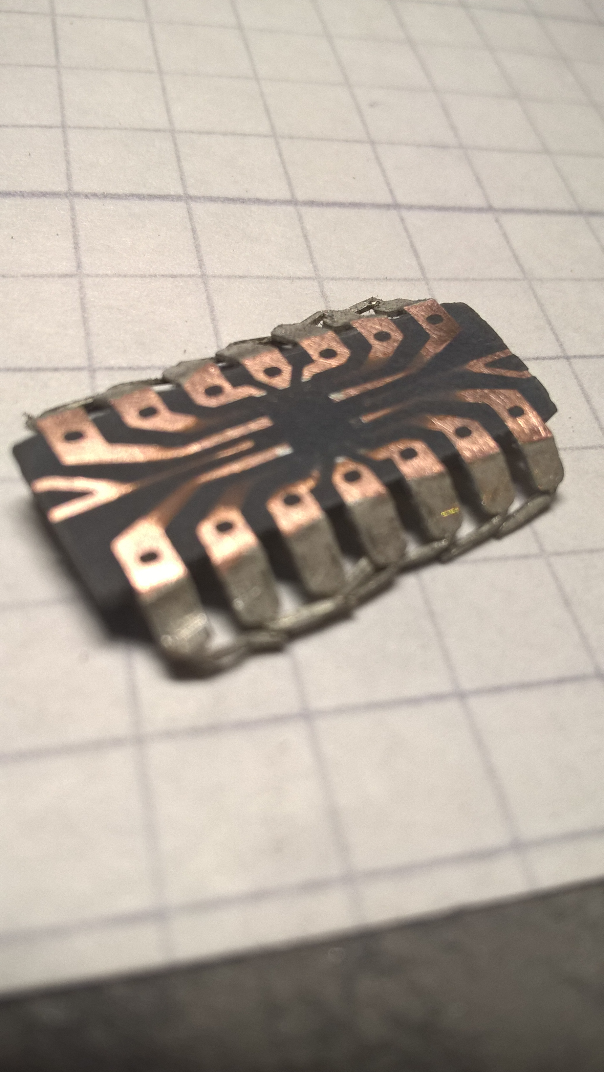
images/Handy/WP_20210917_16_01_44_Pro.jpg
