jufo-ufo/Breadboard-Computer/images/Handy/Chip_Internal/WP_20210917_16_18_44_Pro.jpg

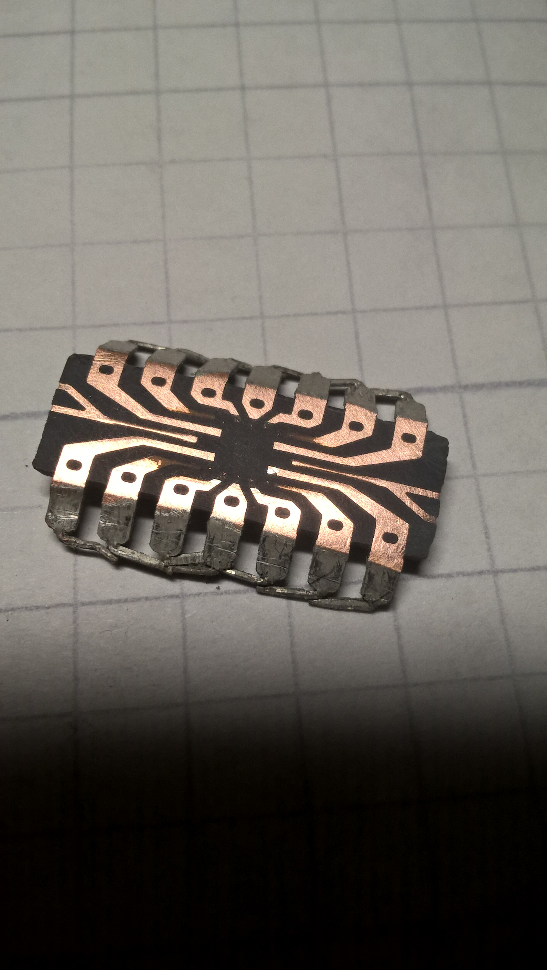
images/Handy/WP_20210917_16_18_44_Pro.jpg
