jufo-ufo/Breadboard-Computer/images/Handy/Chip_Internal/WP_20210917_16_42_20_Pro.jpg

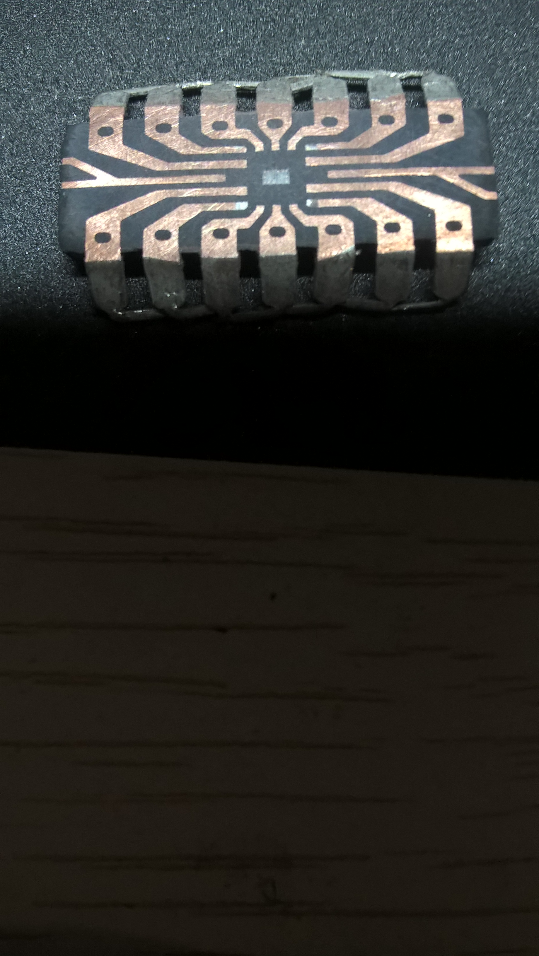
images/Handy/WP_20210917_16_42_20_Pro.jpg
