jufo-ufo/Breadboard-Computer/images/Handy/Chip_Internal/WP_20210917_17_07_32_Pro.jpg

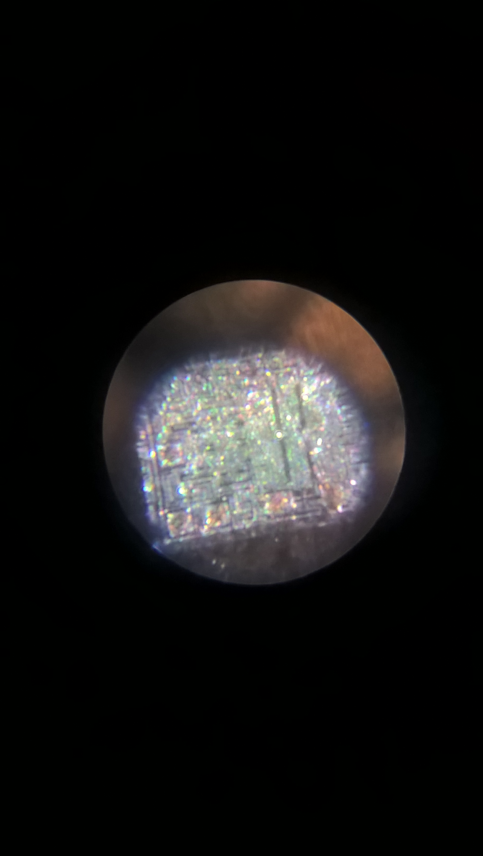
images/Handy/WP_20210917_17_07_32_Pro.jpg
