jufo-ufo/Breadboard-Computer/images/Handy/Chip_Internal/WP_20210917_17_09_54_Pro.jpg

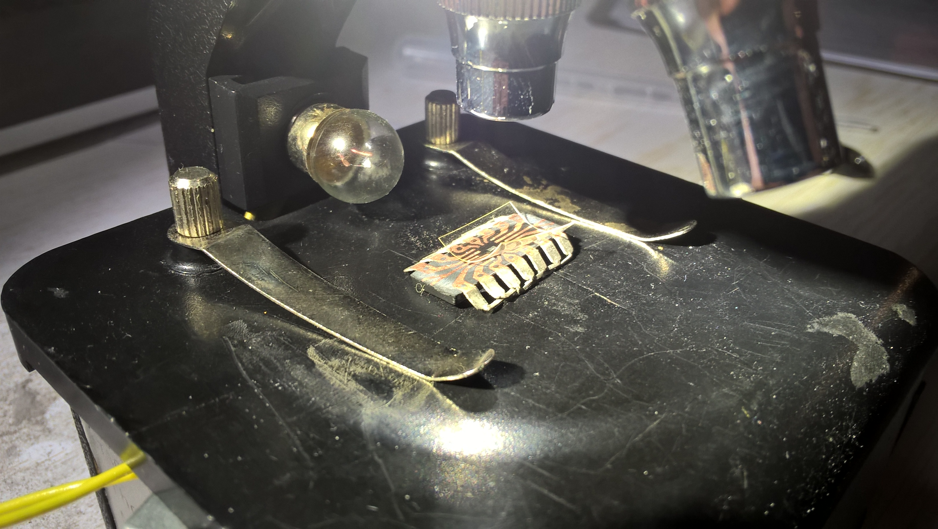
images/Handy/WP_20210917_17_09_54_Pro.jpg
