jufo-ufo/Breadboard-Computer/images/Handy/WP_20211112_13_23_42_Pro.jpg

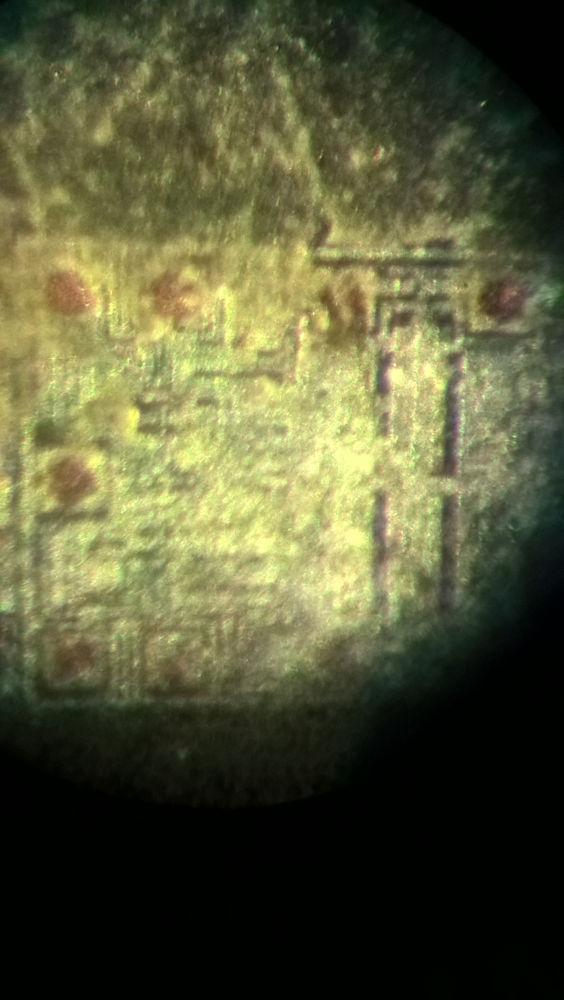
images/Handy/WP_20211112_13_23_42_Pro.jpg
