jufo-ufo/Breadboard-Computer/images/Handy/WP_20211112_13_27_35_Pro.jpg

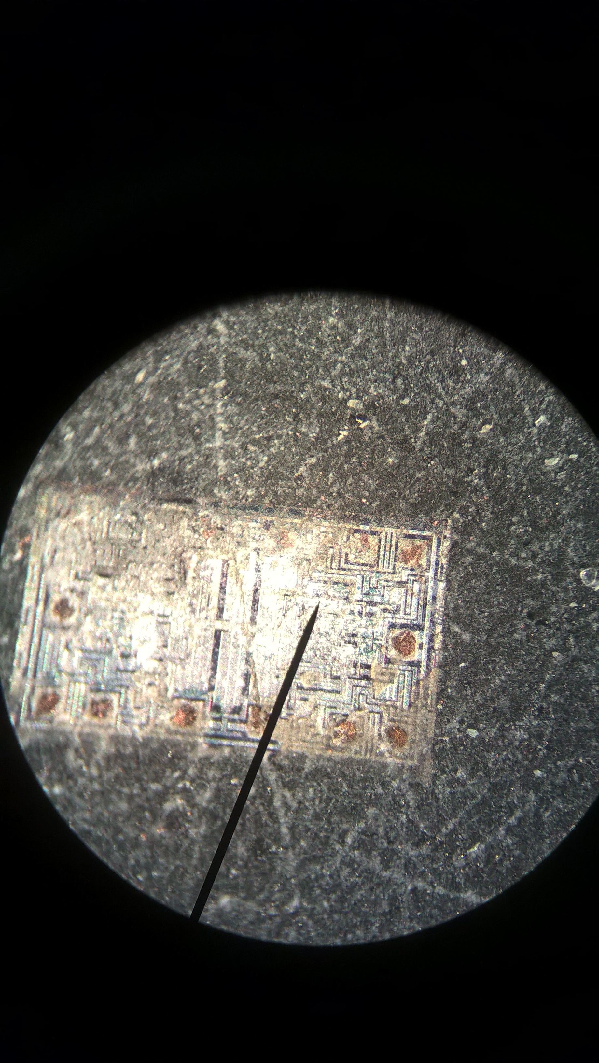
images/Handy/WP_20211112_13_27_35_Pro.jpg
