jufo-ufo/Breadboard-Computer/images/Handy/WP_20211112_13_34_37_Pro.jpg

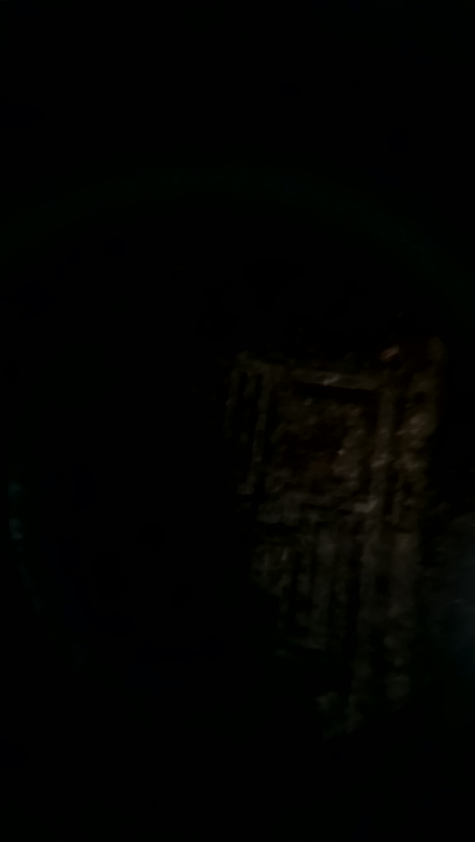
images/Handy/WP_20211112_13_34_37_Pro.jpg
