jufo-ufo/Breadboard-Computer/images/Handy/WP_20211112_13_34_51_Pro.jpg

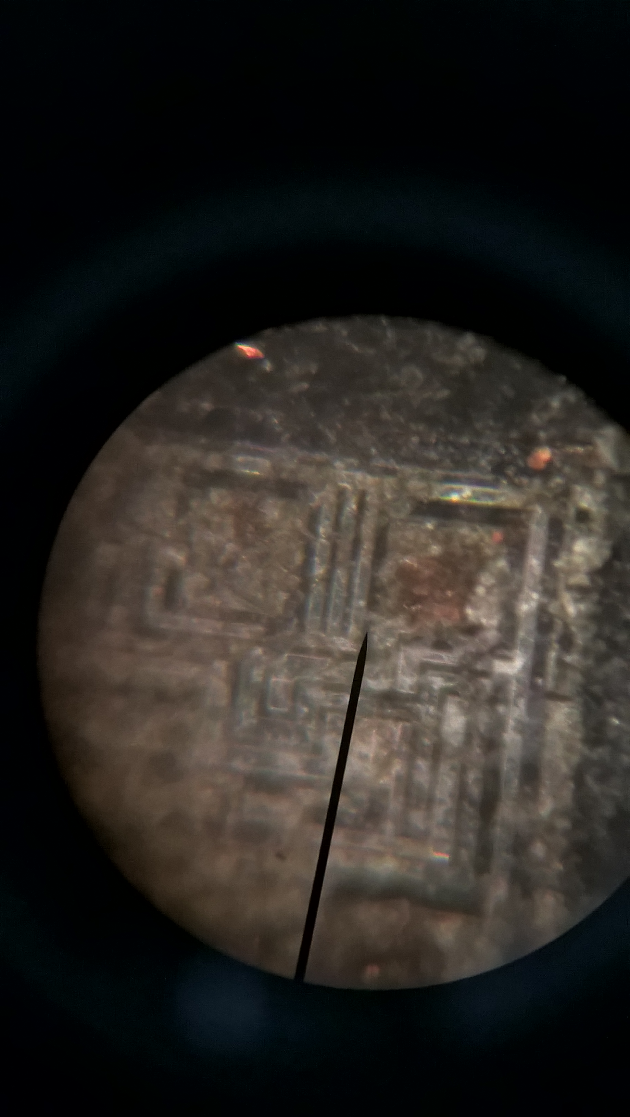
images/Handy/WP_20211112_13_34_51_Pro.jpg
