jufo-ufo/Breadboard-Computer/images/Handy/WP_20211112_13_36_11_Pro.jpg

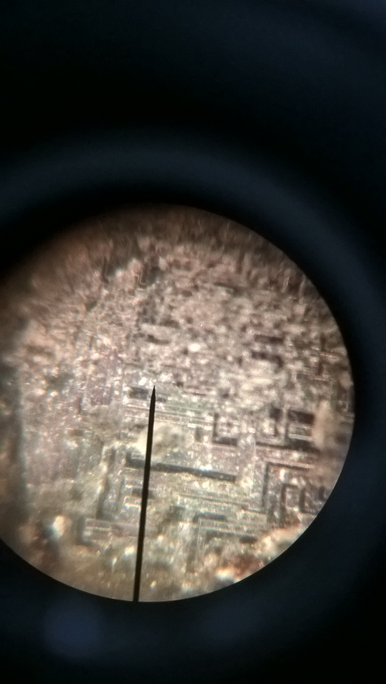
images/Handy/WP_20211112_13_36_11_Pro.jpg
