jufo-ufo/Breadboard-Computer/images/Handy/WP_20211112_13_38_47_Pro.jpg

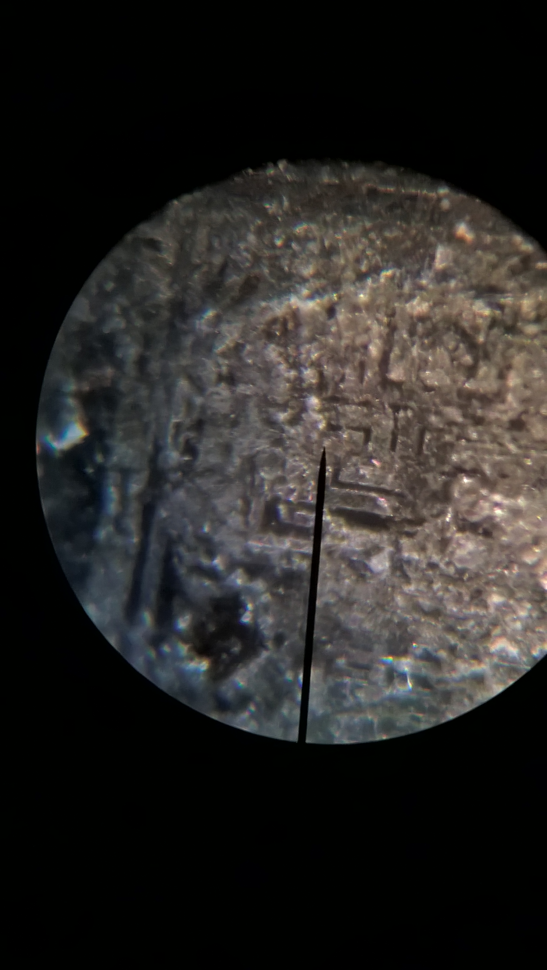
images/Handy/WP_20211112_13_38_47_Pro.jpg
