jufo-ufo/Breadboard-Computer/images/Handy/WP_20211112_13_45_44_Pro.jpg

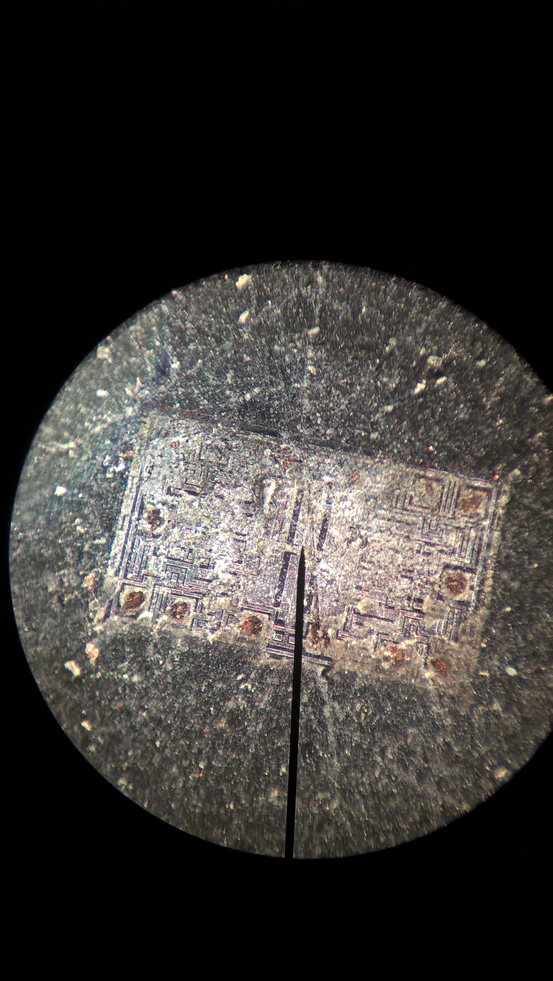
images/Handy/WP_20211112_13_45_44_Pro.jpg
