jufo-ufo/Breadboard-Computer/images/Handy/WP_20211112_13_45_53_Pro.jpg

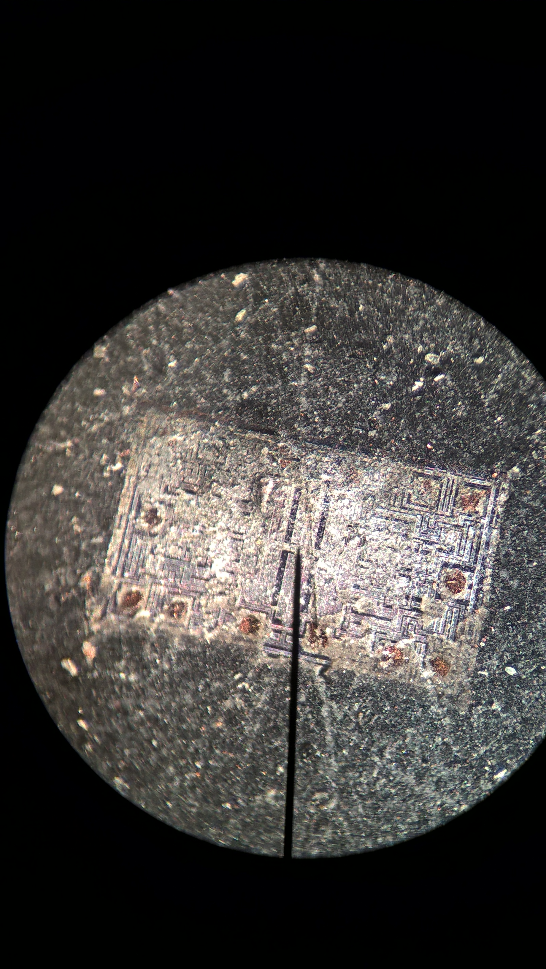
images/Handy/WP_20211112_13_45_53_Pro.jpg
