jufo-ufo/Breadboard-Computer/images/Handy/WP_20211112_13_46_32_Pro.jpg

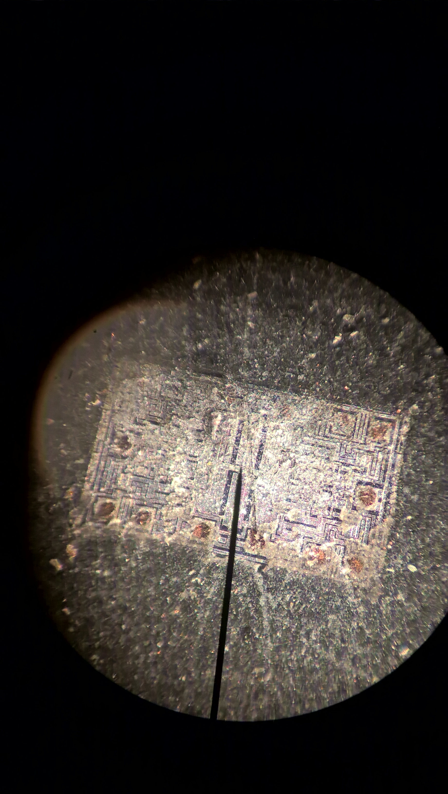
images/Handy/WP_20211112_13_46_32_Pro.jpg
