jufo-ufo/Breadboard-Computer/images/Handy/WP_20211112_13_55_27_Pro.jpg

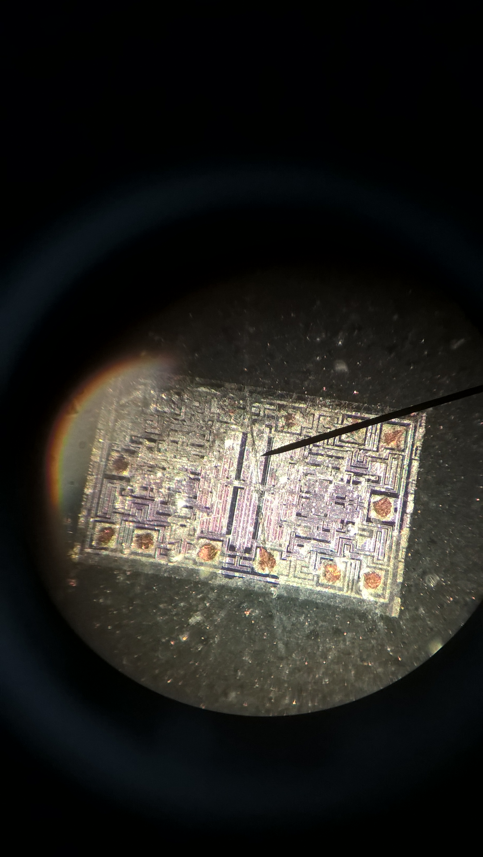
images/Handy/WP_20211112_13_55_27_Pro.jpg
