jufo-ufo/Breadboard-Computer/images/Handy/WP_20211112_13_56_14_Pro.jpg

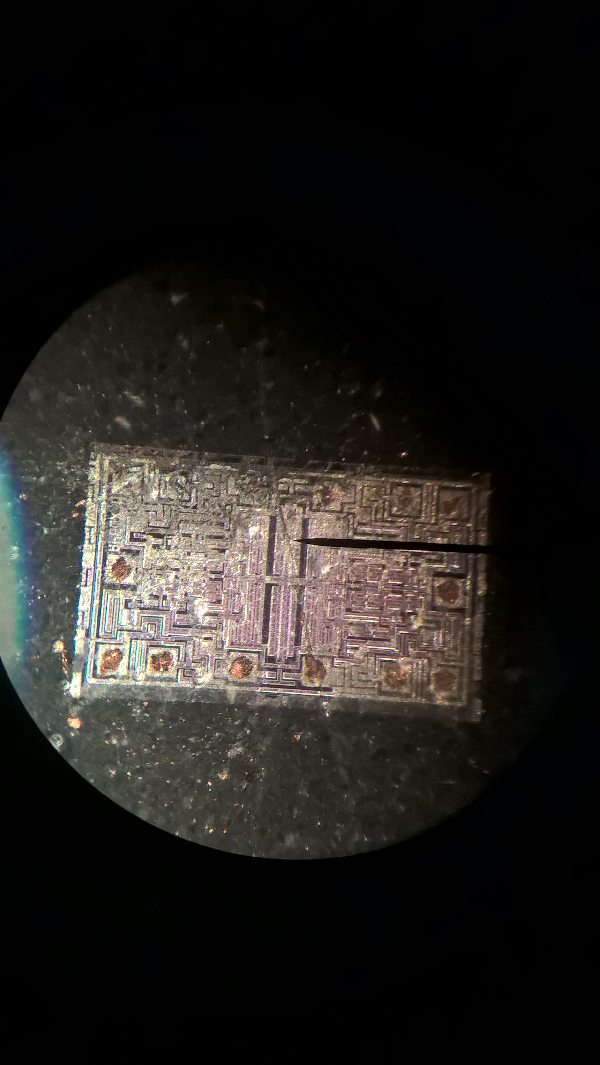
images/Handy/WP_20211112_13_56_14_Pro.jpg
