jufo-ufo/Breadboard-Computer/images/Handy/WP_20211112_13_57_40_Pro.jpg

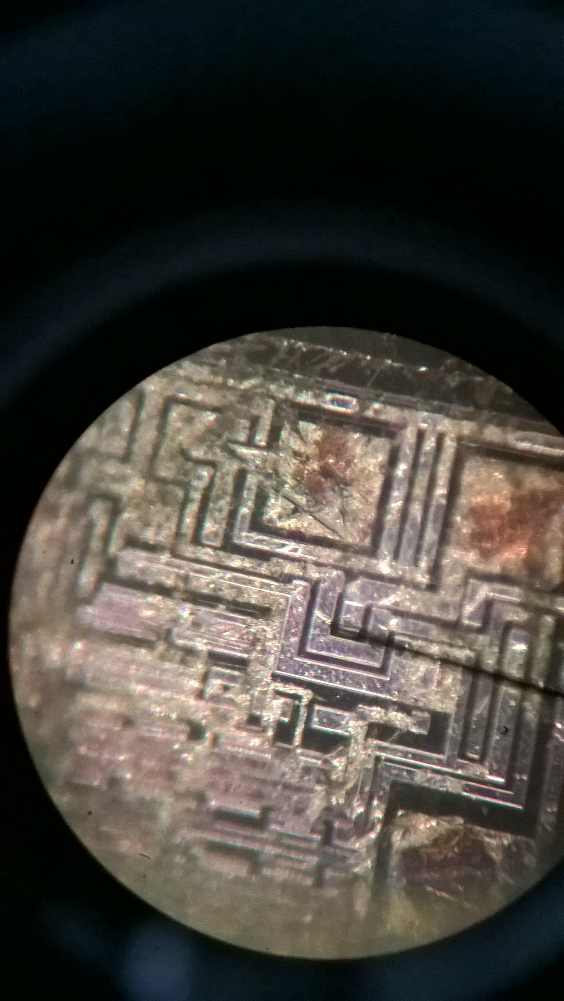
images/Handy/WP_20211112_13_57_40_Pro.jpg
