jufo-ufo/Breadboard-Computer/images/Handy/WP_20211112_14_12_54_Pro.jpg

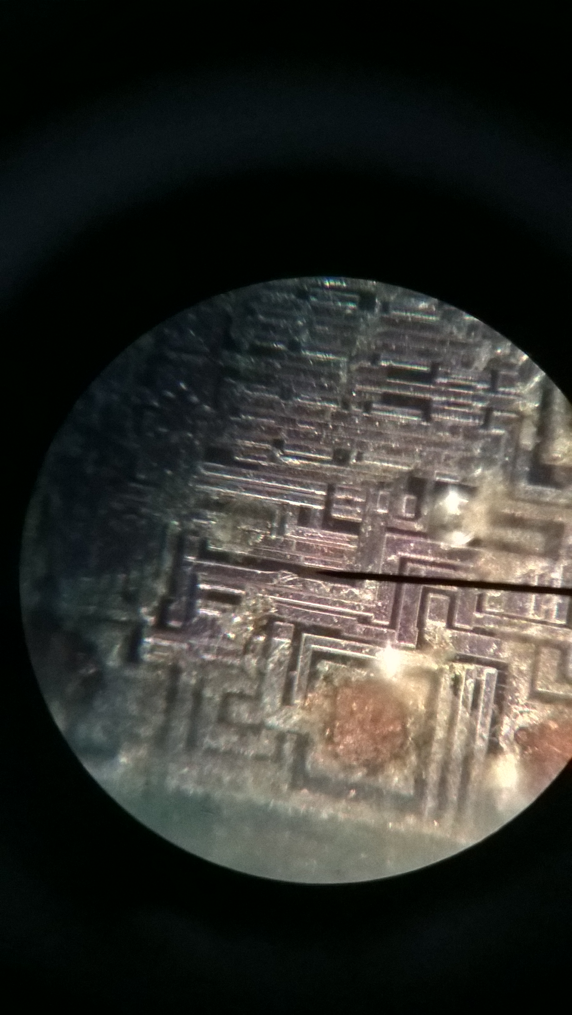
images/Handy/WP_20211112_14_12_54_Pro.jpg
