jufo-ufo/Breadboard-Computer/images/Handy/WP_20211112_14_13_55_Pro.jpg

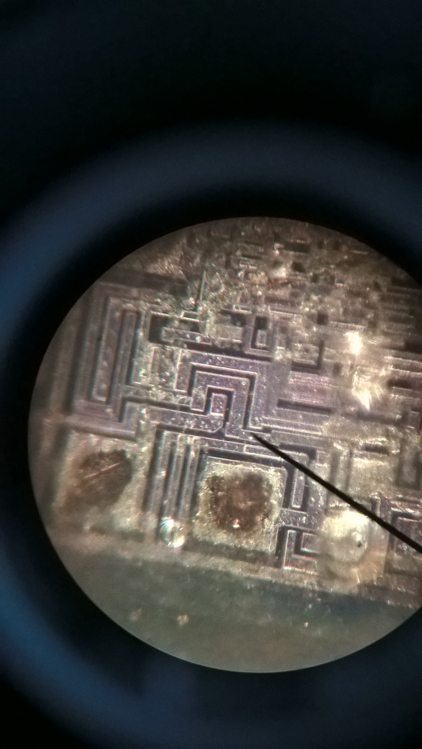
images/Handy/WP_20211112_14_13_55_Pro.jpg
