jufo-ufo/Breadboard-Computer/images/Handy/WP_20211112_14_19_33_Pro.jpg

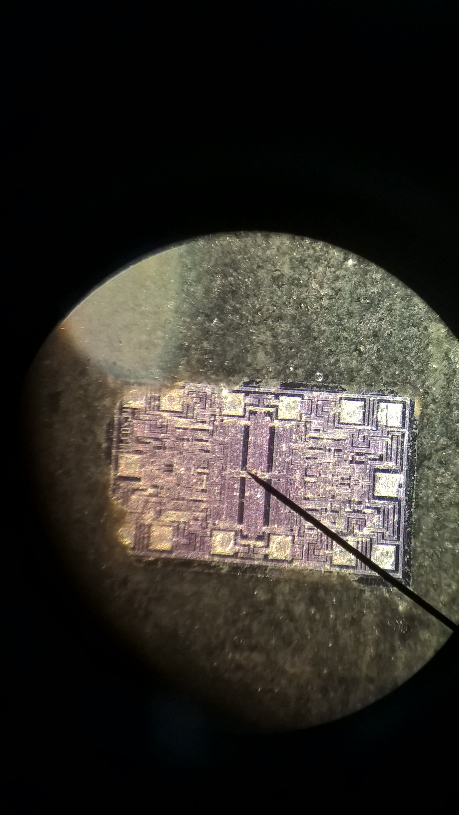
images/Handy/WP_20211112_14_19_33_Pro.jpg
