jufo-ufo/Breadboard-Computer/images/Handy/WP_20211112_14_19_51_Pro.jpg

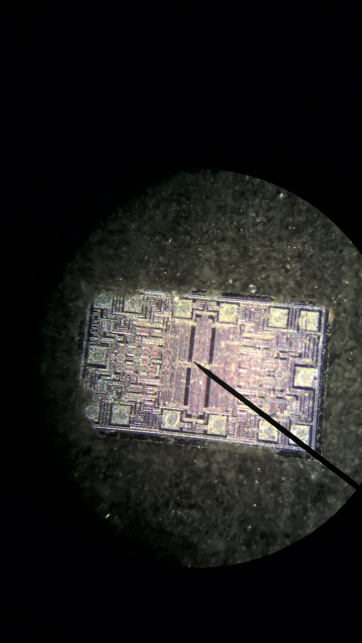
images/Handy/WP_20211112_14_19_51_Pro.jpg
