jufo-ufo/Breadboard-Computer/images/Handy/WP_20211112_14_25_07_Pro.jpg

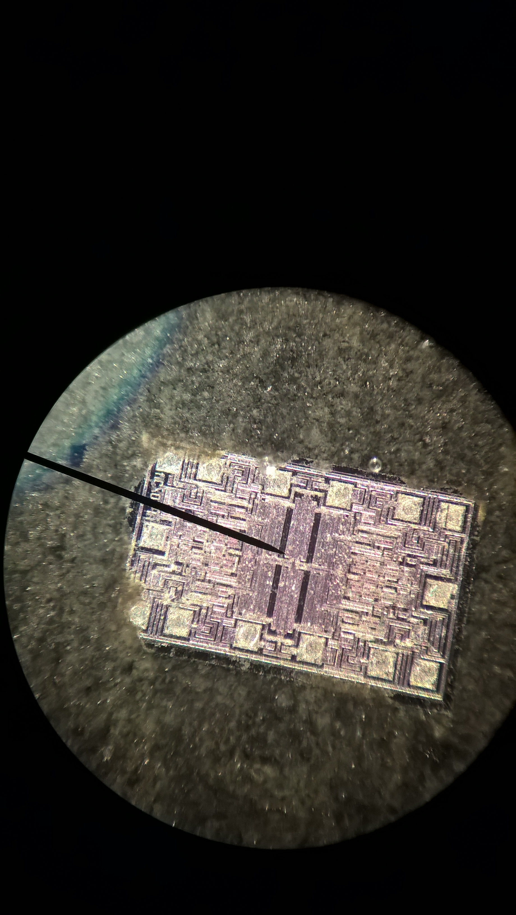
images/Handy/WP_20211112_14_25_07_Pro.jpg
