jufo-ufo/Breadboard-Computer/images/Handy/WP_20211112_14_26_58_Pro.jpg

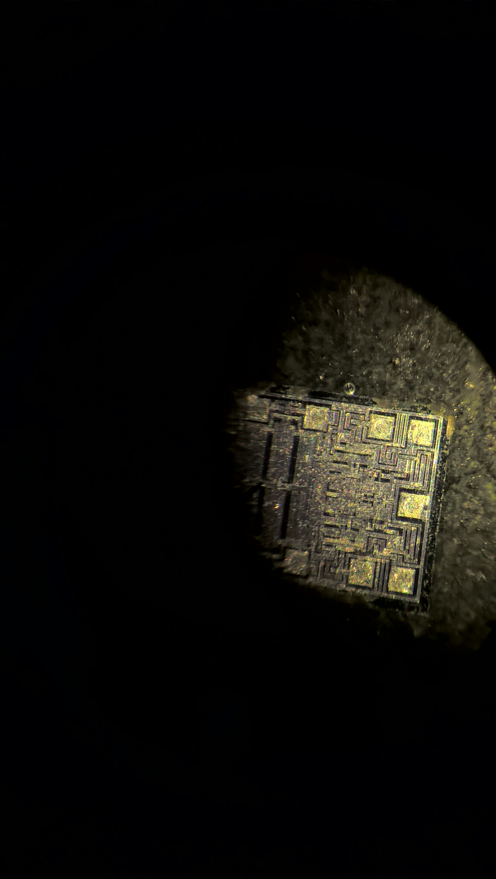
images/Handy/WP_20211112_14_26_58_Pro.jpg
