jufo-ufo/Breadboard-Computer/images/Handy/WP_20211112_14_27_18_Pro.jpg

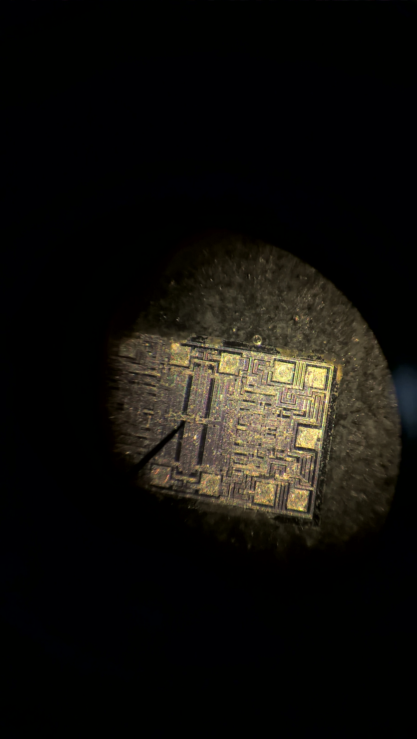
images/Handy/WP_20211112_14_27_18_Pro.jpg
