jufo-ufo/Breadboard-Computer/images/Handy/WP_20211112_14_27_22_Pro.jpg

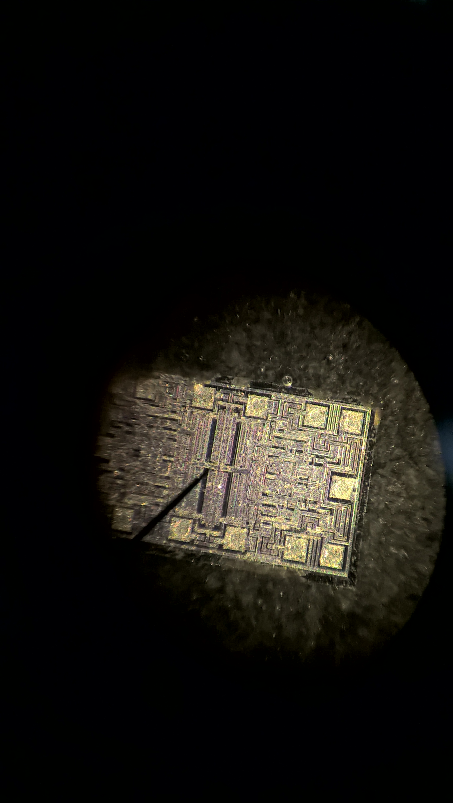
images/Handy/WP_20211112_14_27_22_Pro.jpg
