jufo-ufo/Breadboard-Computer/images/Handy/WP_20211112_14_40_52_Pro.jpg

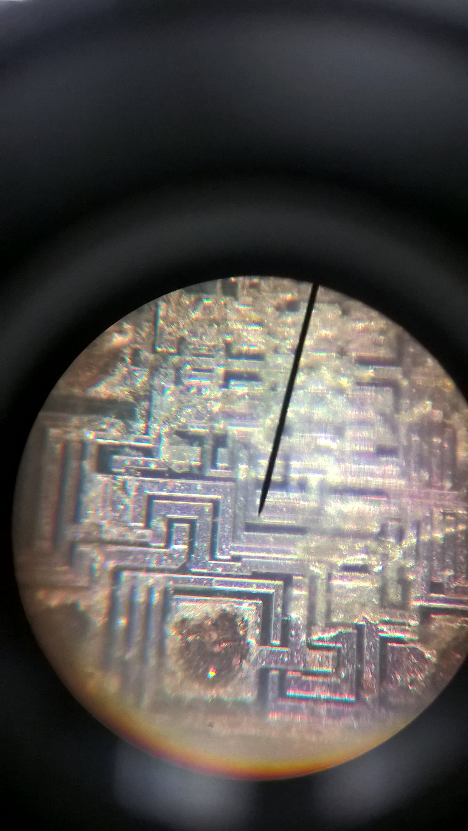
images/Handy/WP_20211112_14_40_52_Pro.jpg
