jufo-ufo/Breadboard-Computer/images/Handy/WP_20211112_14_41_12_Pro.jpg

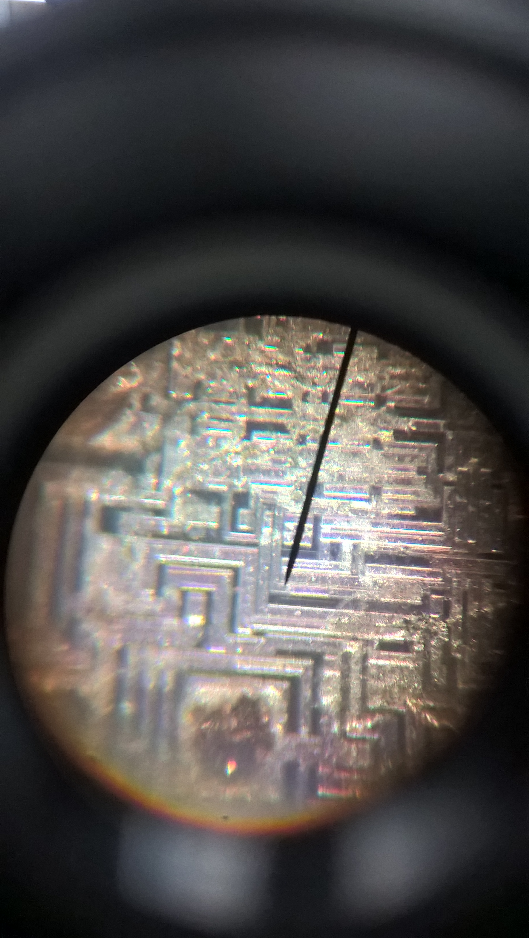
images/Handy/WP_20211112_14_41_12_Pro.jpg
