jufo-ufo/Breadboard-Computer/images/Handy/WP_20211216_16_39_46_Pro (3).jpg

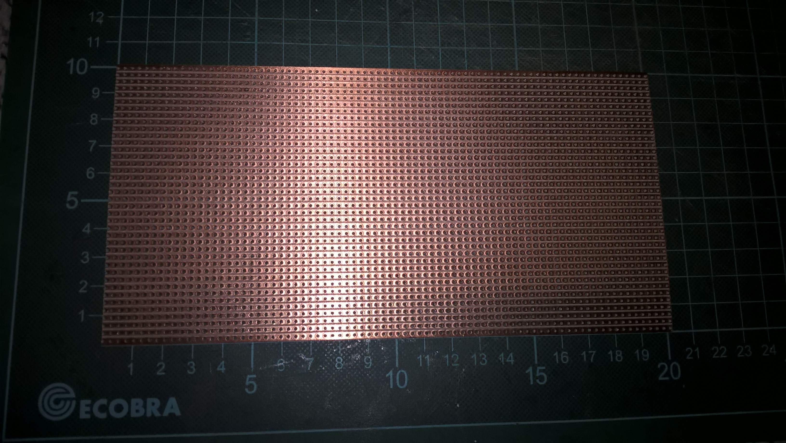
images/Handy/WP_20211216_16_39_46_Pro (3).jpg
