jufo-ufo/Breadboard-Computer/images/Handy/WP_20211216_16_39_46_Pro.jpg

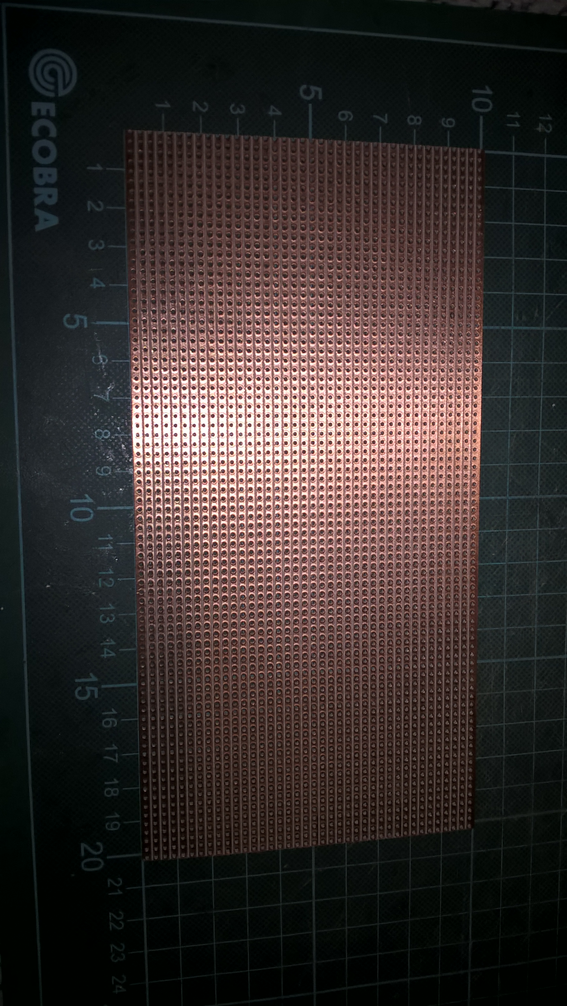
images/Handy/WP_20211216_16_39_46_Pro.jpg
