jufo-ufo/Breadboard-Computer/images/Handy/WP_20211216_16_40_58_Pro.jpg

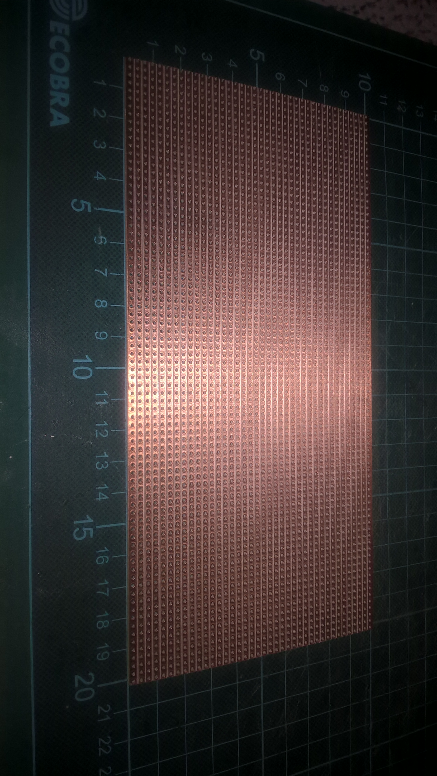
images/Handy/WP_20211216_16_40_58_Pro.jpg
