jufo-ufo/Breadboard-Computer/images/Handy/WP_20211216_16_41_11_Pro.jpg

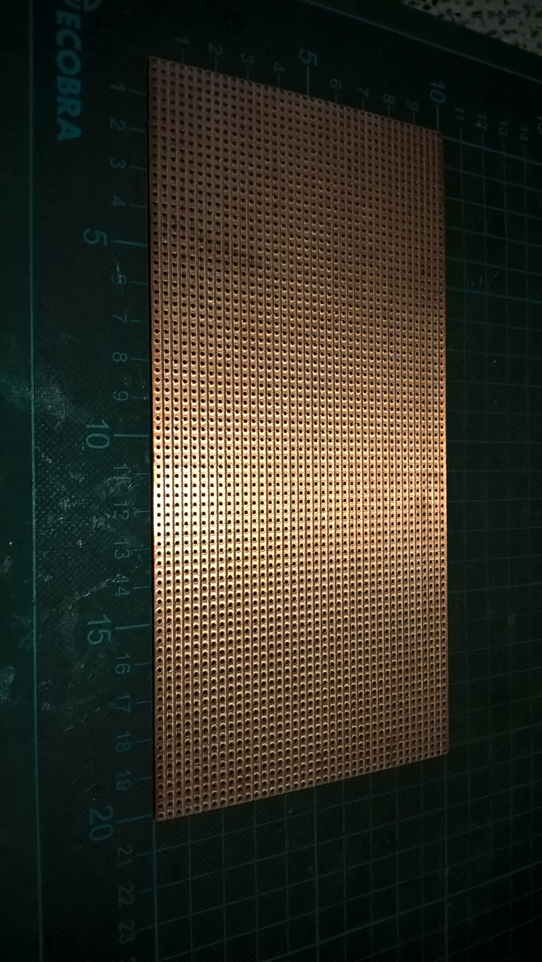
images/Handy/WP_20211216_16_41_11_Pro.jpg
