jufo-ufo/Breadboard-Computer/images/Handy/WP_20211217_13_47_51_Pro.jpg

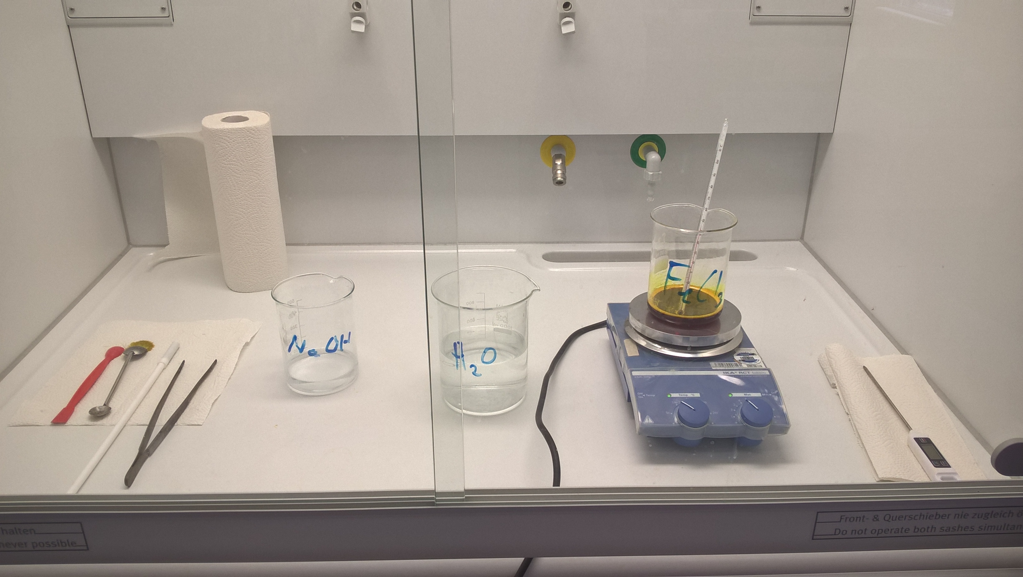
images/Handy/WP_20211217_13_47_51_Pro.jpg
