jufo-ufo/Breadboard-Computer/images/Handy/WP_20211217_14_58_34_Pro.jpg

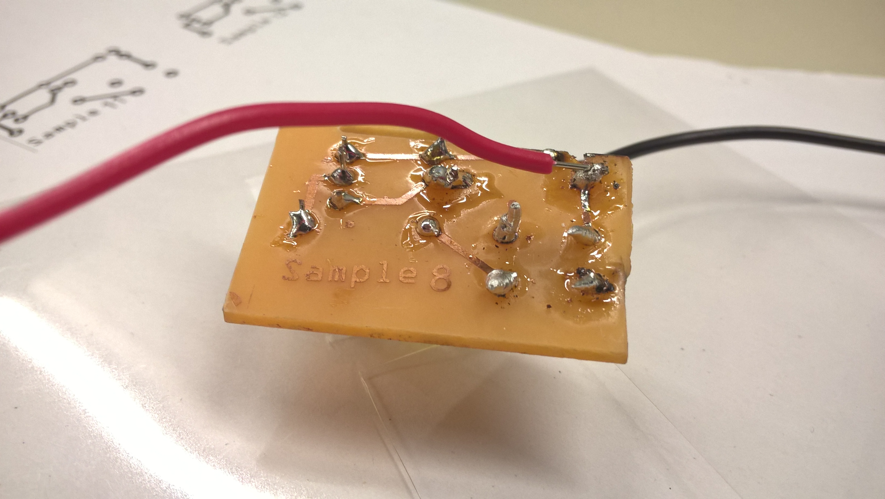
images/Handy/WP_20211217_14_58_34_Pro.jpg
