jufo-ufo/Breadboard-Computer/images/Hintergurnd.jpg

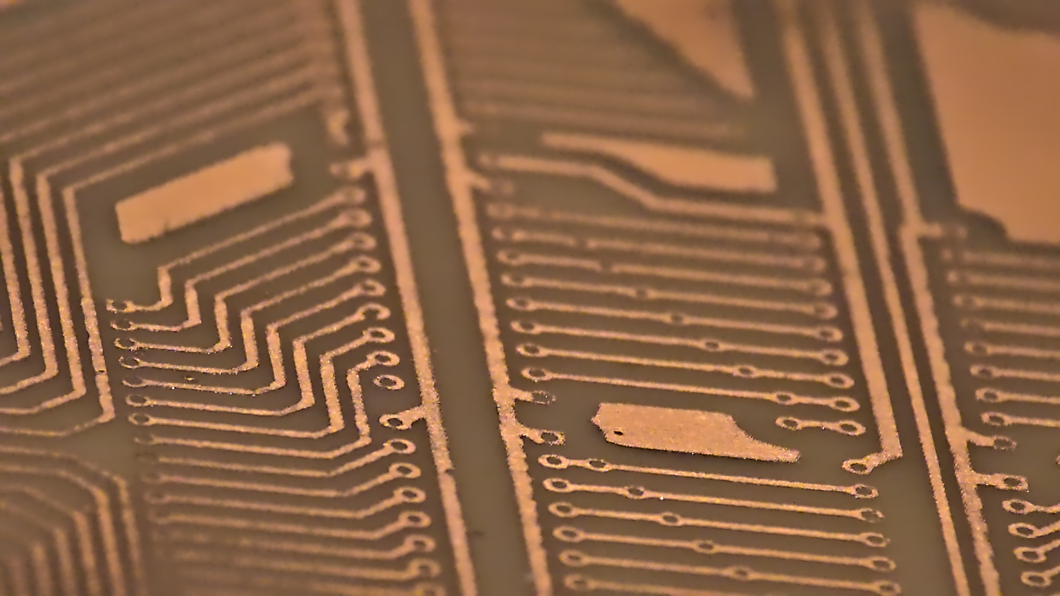
images/Hintergurnd.jpg
