jufo-ufo/Breadboard-Computer/images/kicad_pcb.png

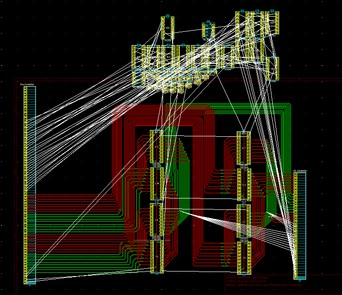
images/kicad_pcb.png
