jufo-ufo/Breadboard-Computer/images/kicad_schematic.png

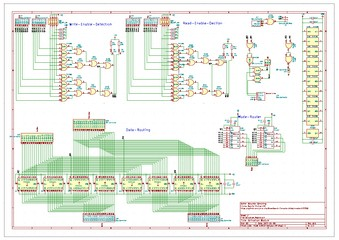
images/kicad_schematic.png
