jufo-ufo/Breadboard-Computer/images/mem_map.png

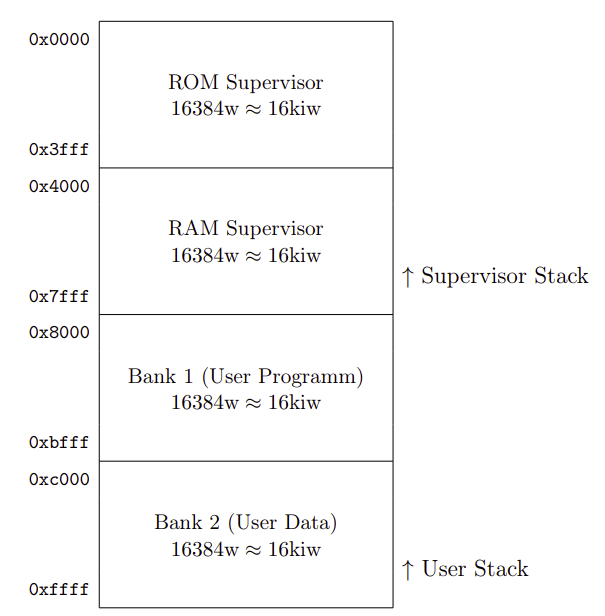
images/mem_map.png
