jufo-ufo/Breadboard-Computer/images/Memory_Map_.png

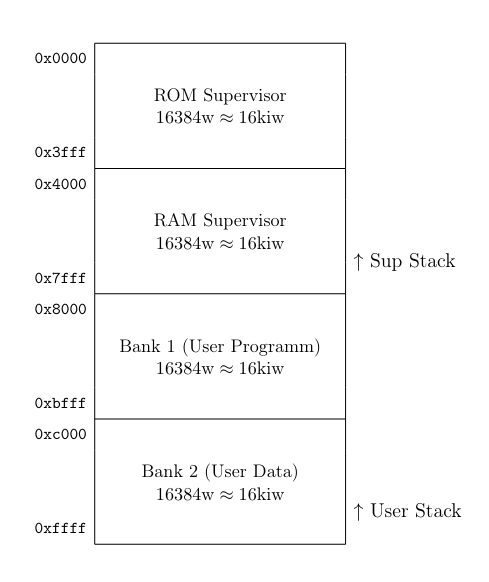
images/Memory_Map_.png
