jufo-ufo/Breadboard-Computer/images/Memory_Minimalistic_V01_02.jpg

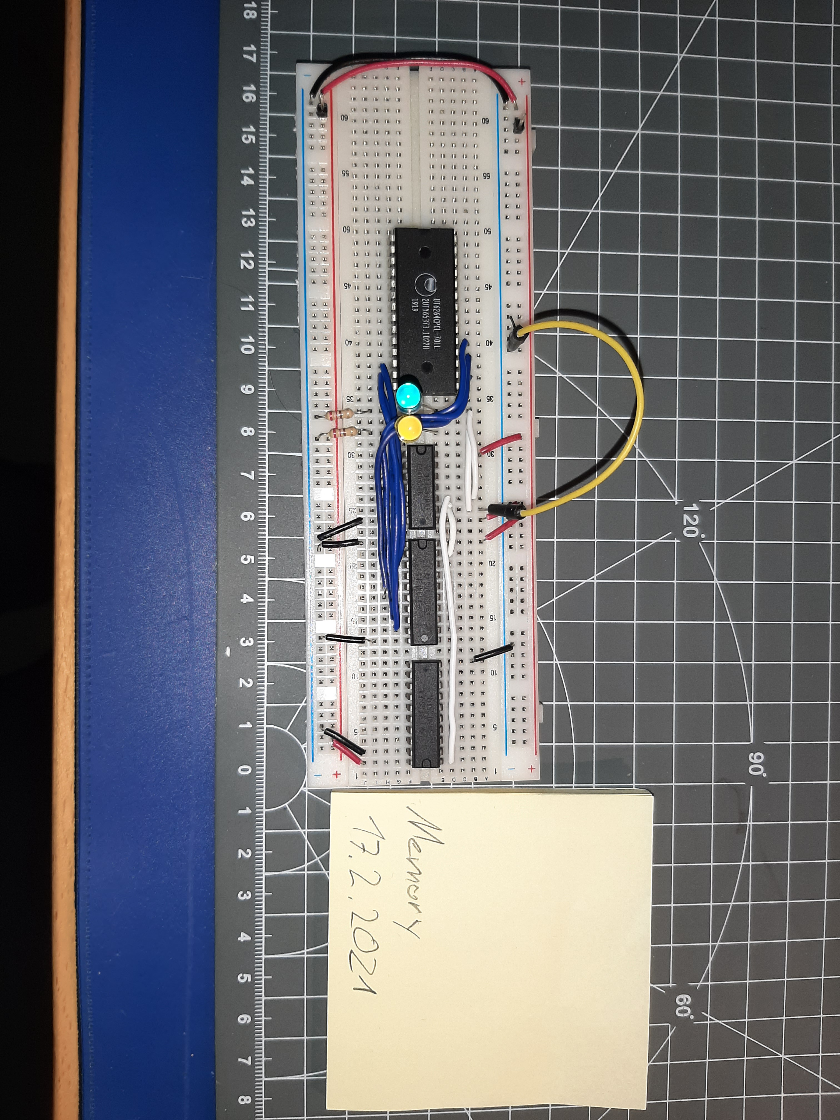
images/Memory_Minimalistic_V01_02.jpg
