jufo-ufo/Breadboard-Computer/images/NAND_1.jpg

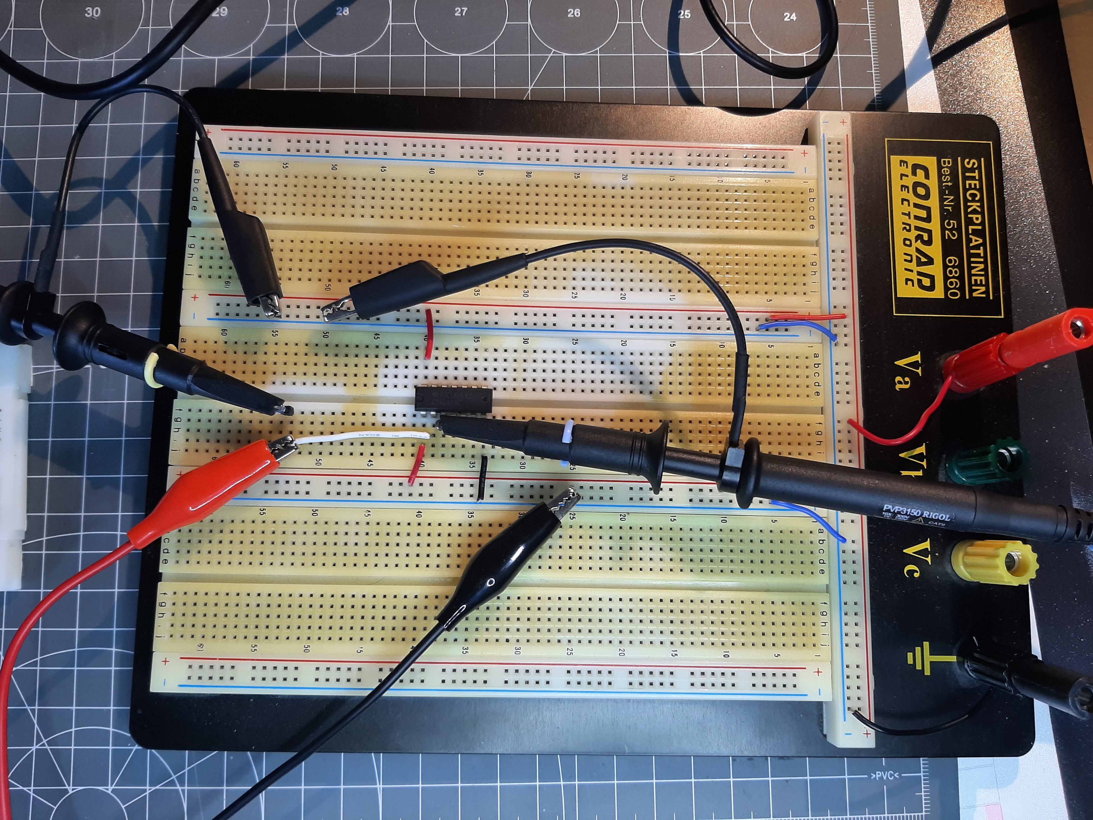
images/NAND_1.jpg
