jufo-ufo/Breadboard-Computer/images/NAND_2.jpg

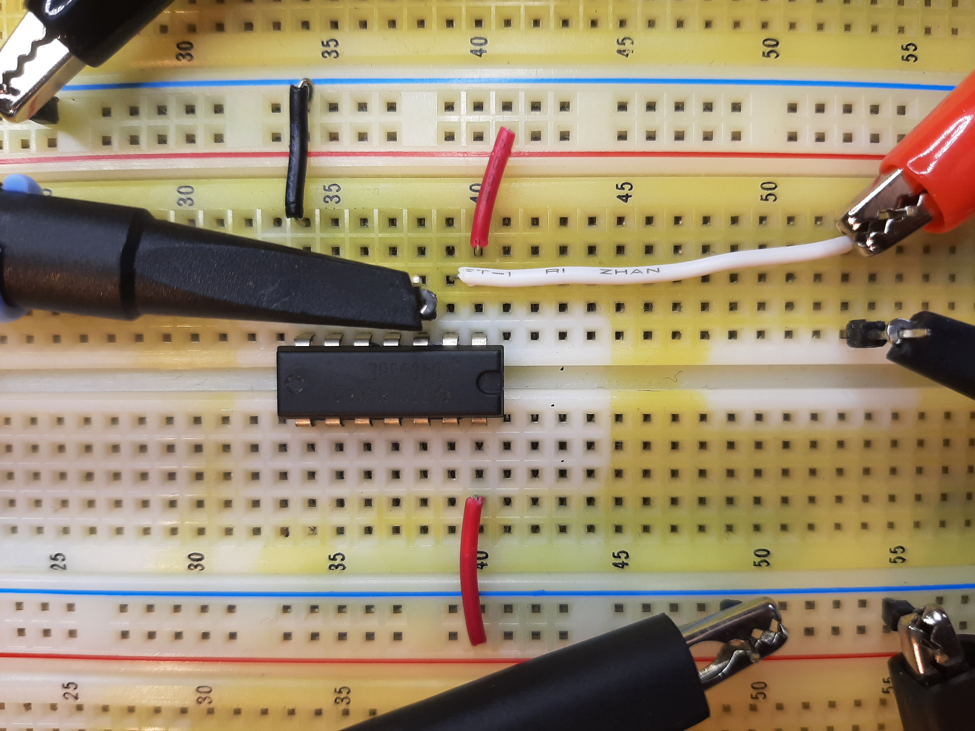
images/NAND_2.jpg
