jufo-ufo/Breadboard-Computer/images/Neu Hintergrund 2.jpg

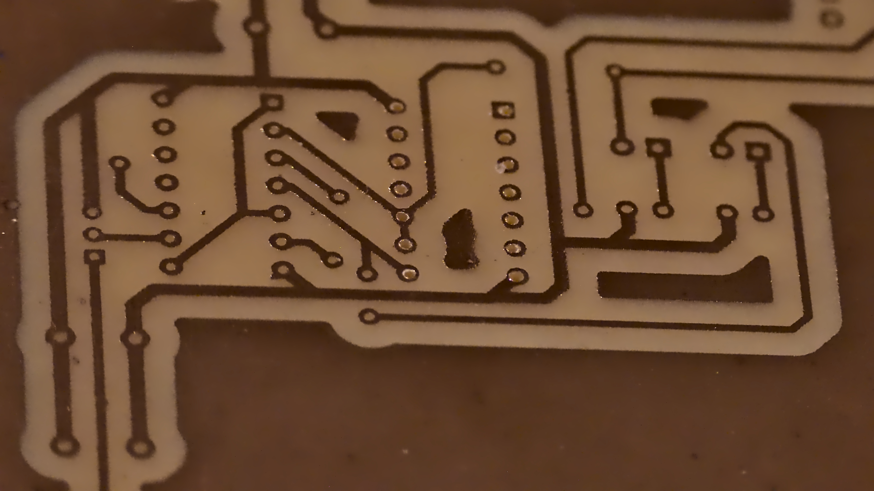
images/Neu Hintergrund 2.jpg
