jufo-ufo/Breadboard-Computer/images/Newspaper_PerspektiveP.jpg

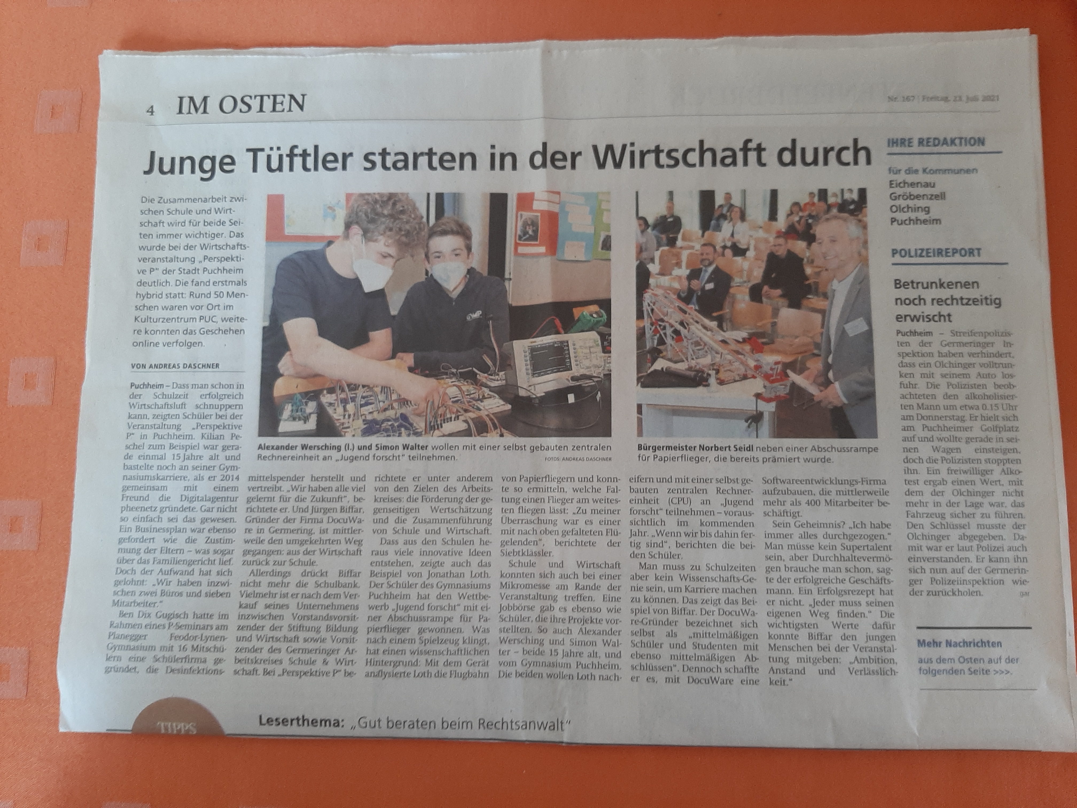
images/Newspaper_PerspektiveP.jpg
