jufo-ufo/Breadboard-Computer/images/Note_2.jpg

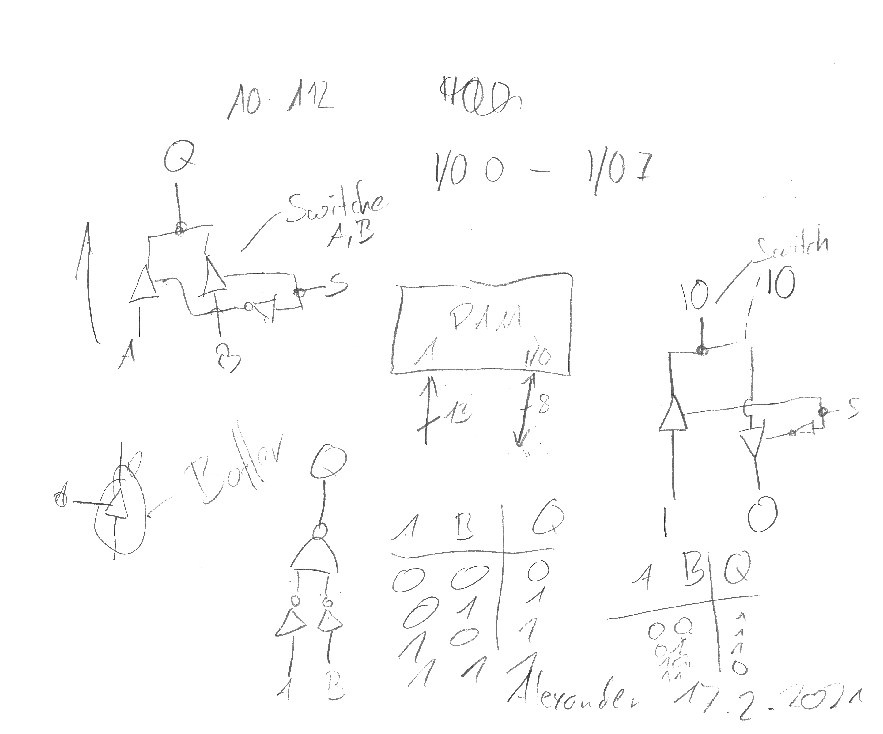
images/Note_2.jpg
