jufo-ufo/Breadboard-Computer/images/Note_3.jpg

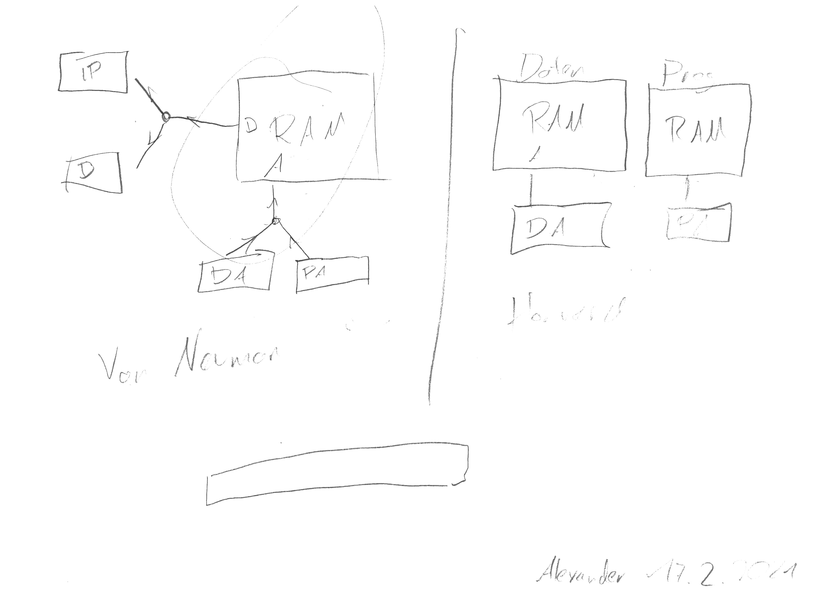
images/Note_3.jpg
