jufo-ufo/Breadboard-Computer/images/Osciloscope_Off_01.jpg

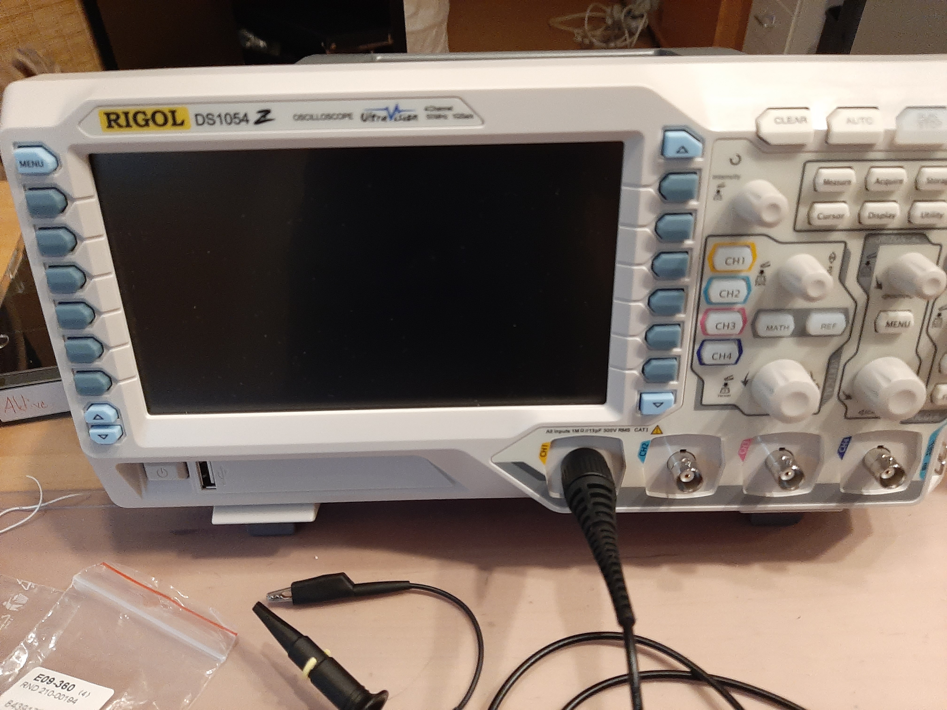
images/Osciloscope_Off_01.jpg
