jufo-ufo/Breadboard-Computer/images/pcb/20220119_215228.jpg

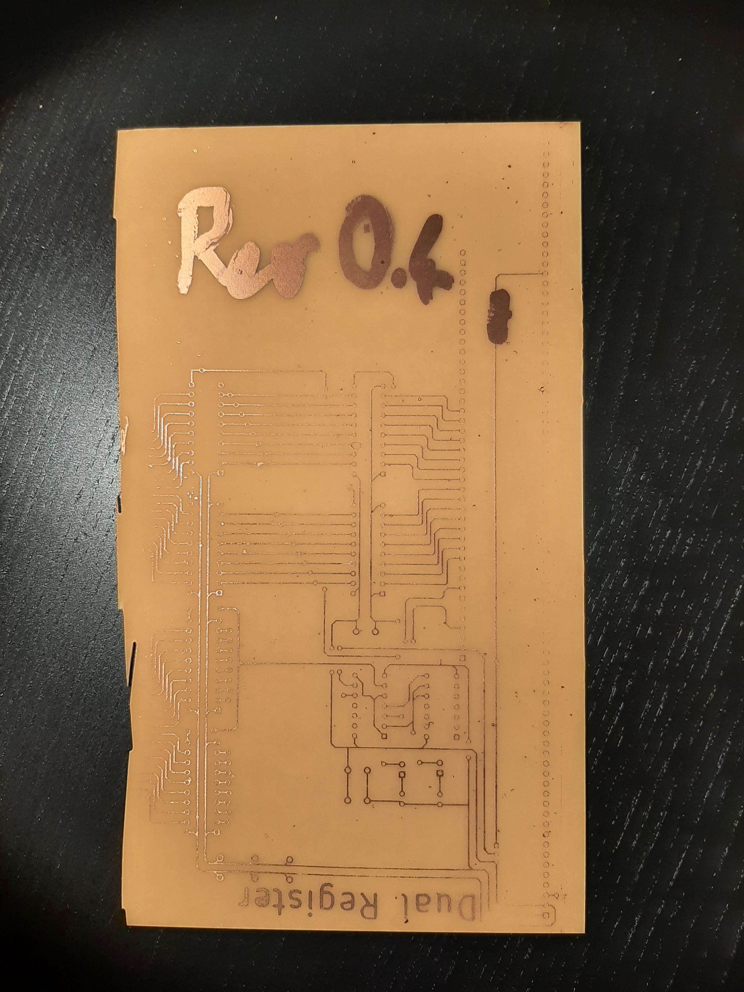
images/pcb/20220119_215228.jpg
