jufo-ufo/Breadboard-Computer/images/pcb/Schichtung.jpg

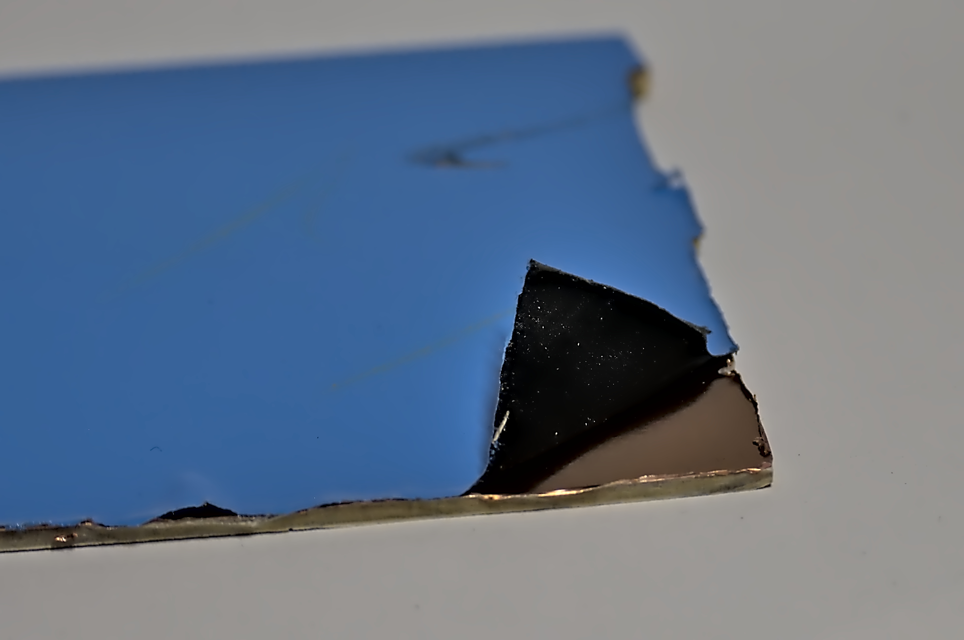
images/pcb/Schichtung.jpg
