jufo-ufo/Breadboard-Computer/images/pcb/Versuch3.jpg

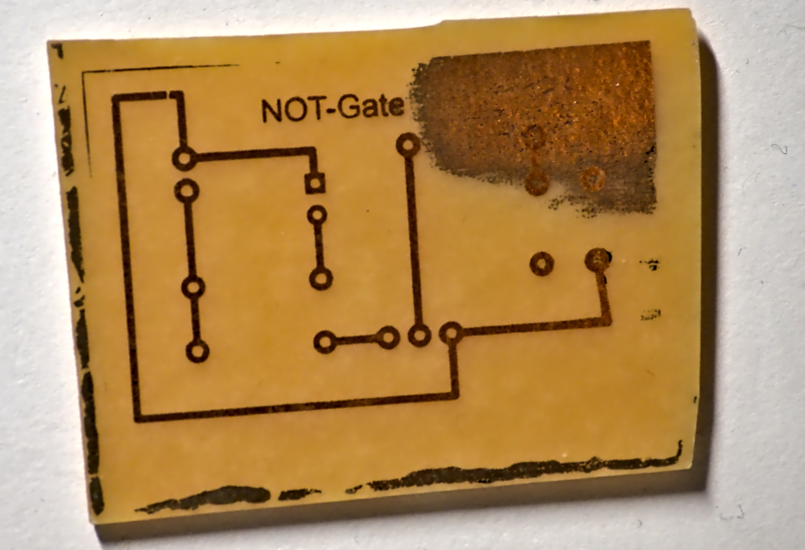
images/pcb/Versuch3.jpg
