jufo-ufo/Breadboard-Computer/images/Power_Source_Off_01.jpg

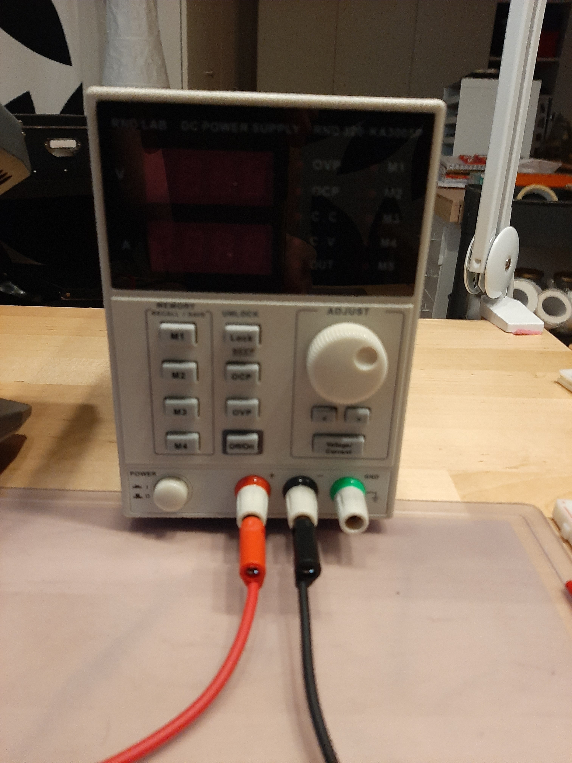
images/Power_Source_Off_01.jpg
