jufo-ufo/Breadboard-Computer/images/PropDelay_28C256-150_HL.png

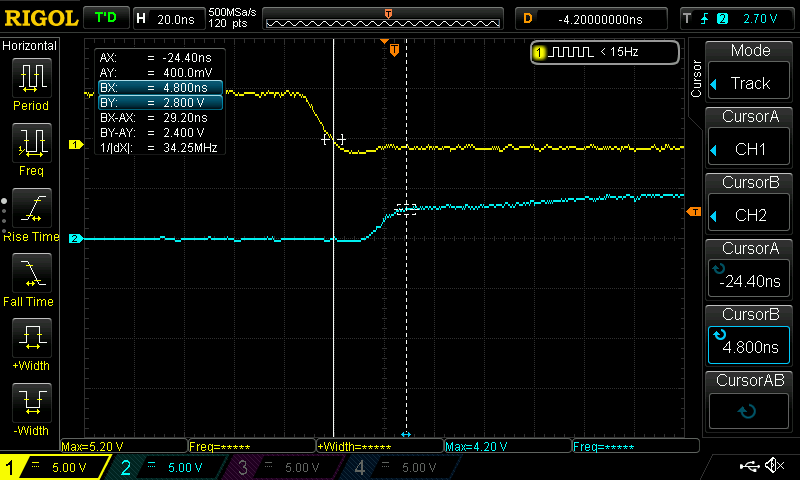
images/PropDelay_28C256-150_HL.png
