jufo-ufo/Breadboard-Computer/images/PropDelay_74HC00_LH.png

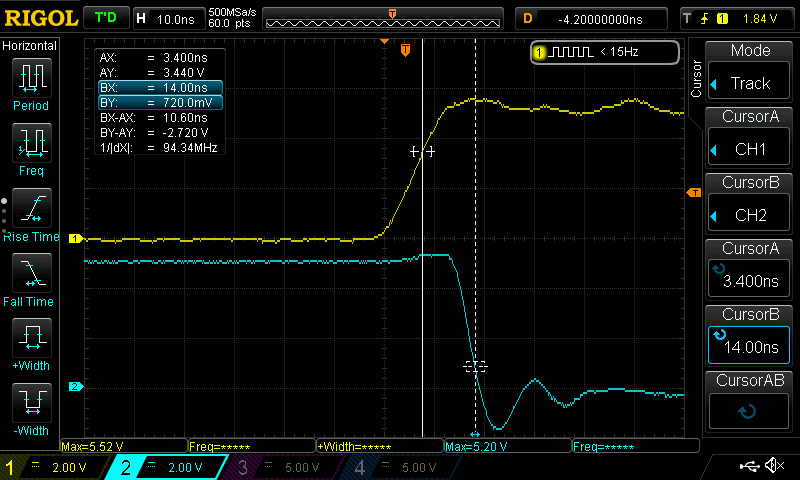
images/PropDelay_74HC00_LH.png
