jufo-ufo/Breadboard-Computer/images/Transistor_01.jpg

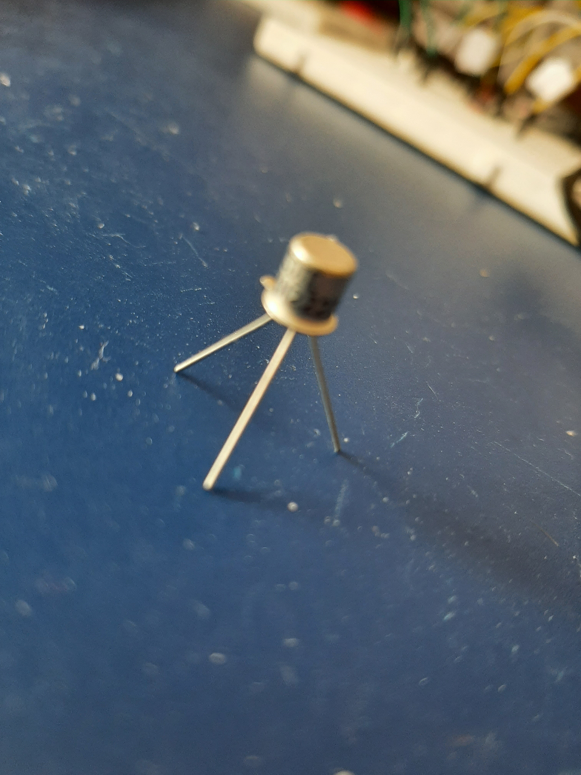
images/Transistor_01.jpg
