jufo-ufo/Breadboard-Computer/images/Transistor_02.jpg

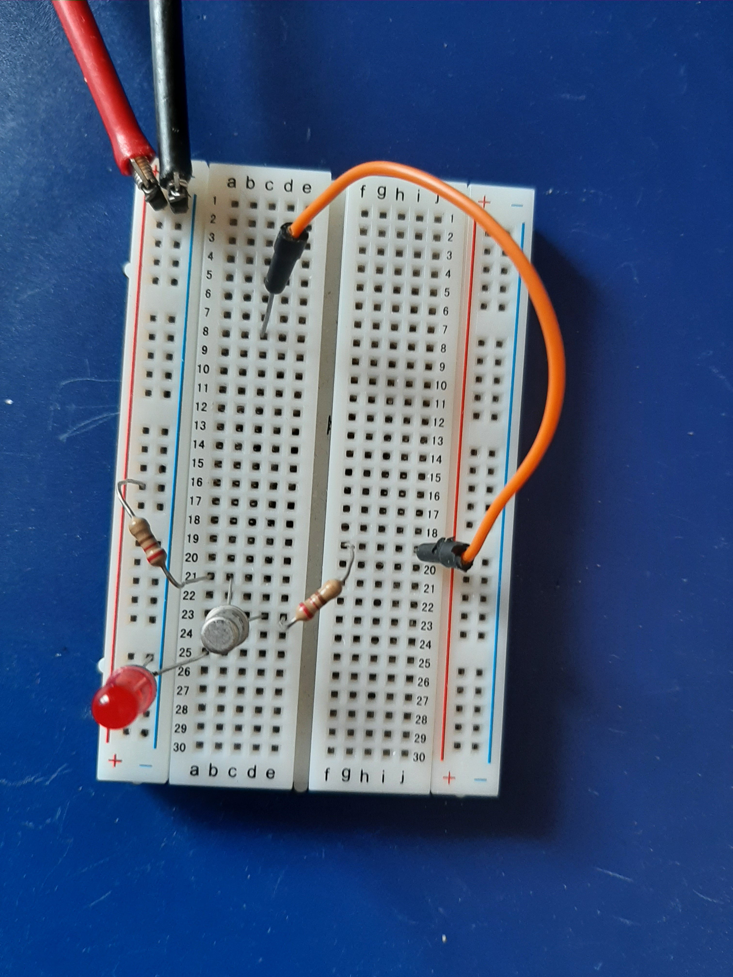
images/Transistor_02.jpg
