jufo-ufo/Breadboard-Computer/images/Transistor_03.jpg

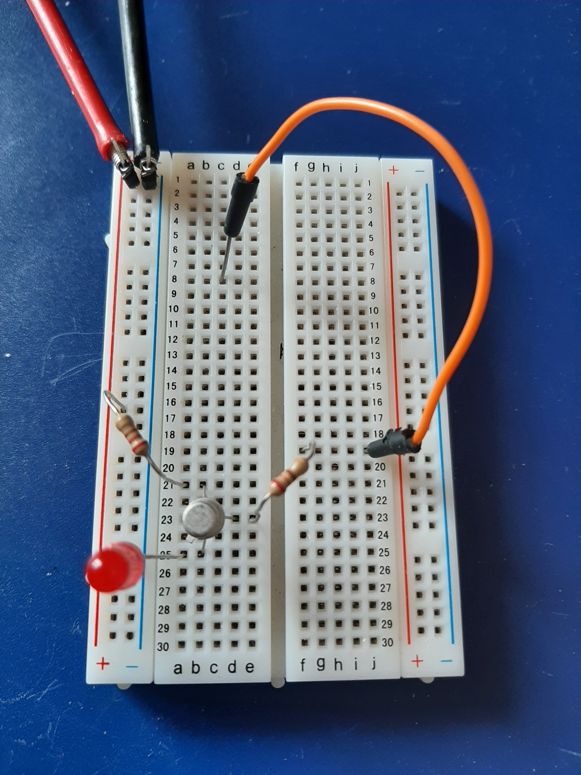
images/Transistor_03.jpg
