jufo-ufo/Breadboard-Computer/images/Transistor_04.jpg

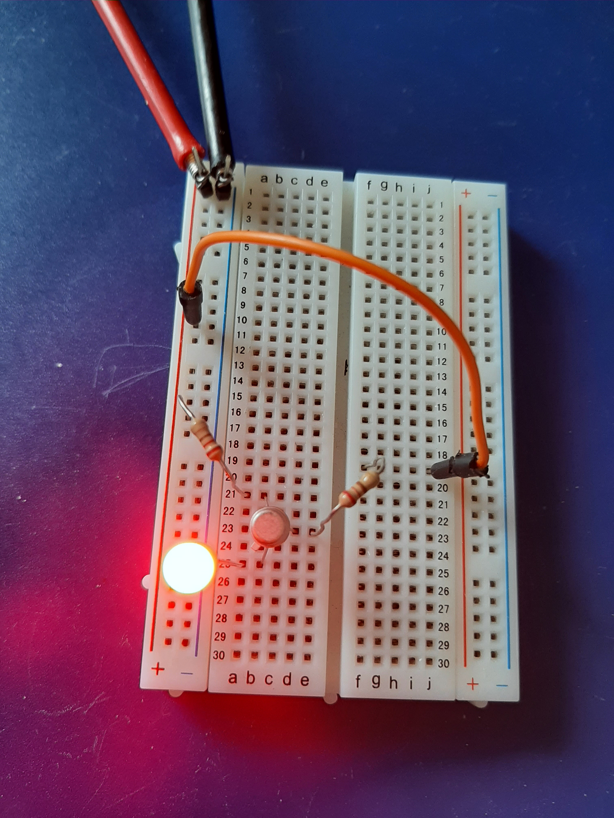
images/Transistor_04.jpg
