jufo-ufo/Breadboard-Computer/images/Transistor_06.jpg

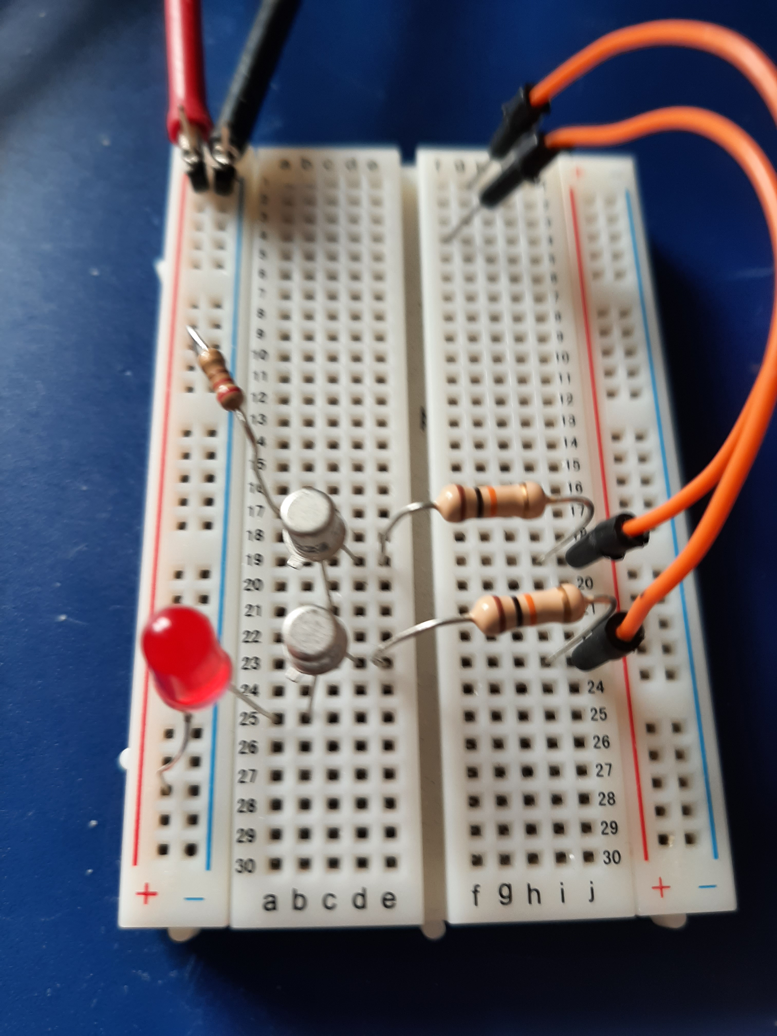
images/Transistor_06.jpg
