jufo-ufo/Breadboard-Computer/images/Transistor_07.jpg

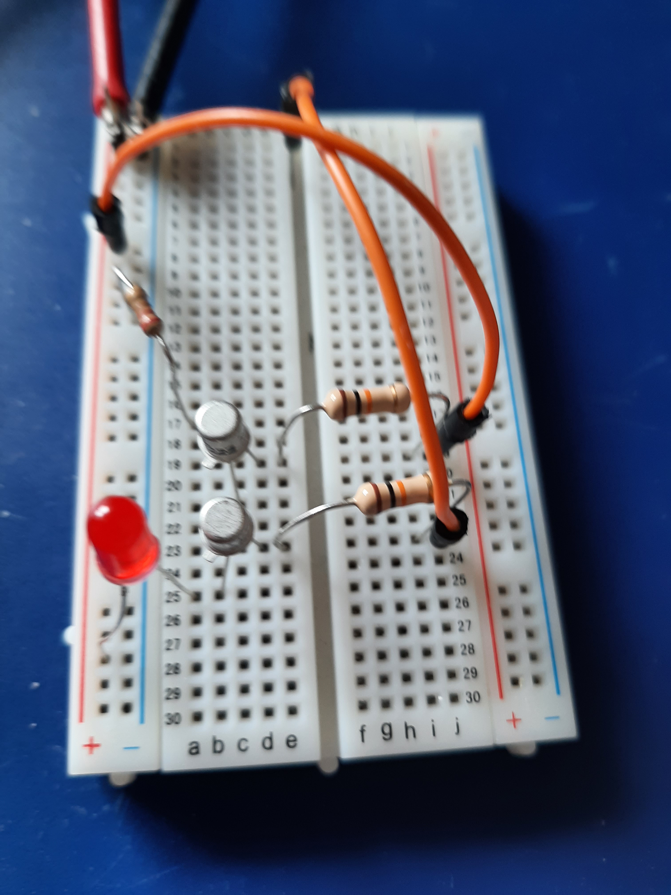
images/Transistor_07.jpg
