jufo-ufo/Breadboard-Computer/images/Transistor_08.jpg

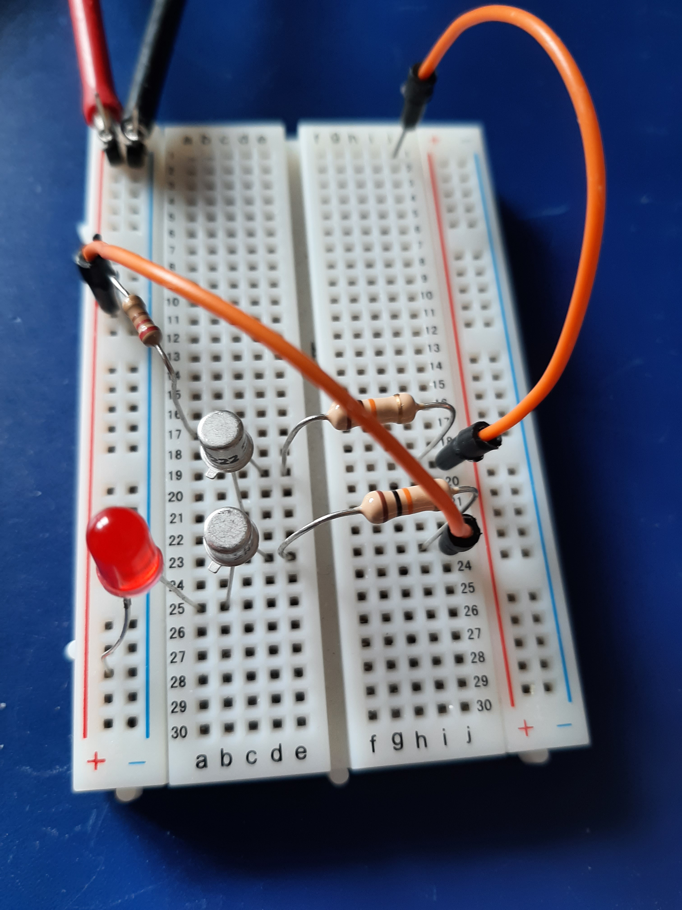
images/Transistor_08.jpg
