jufo-ufo/Breadboard-Computer/images/Transistor_10.jpg

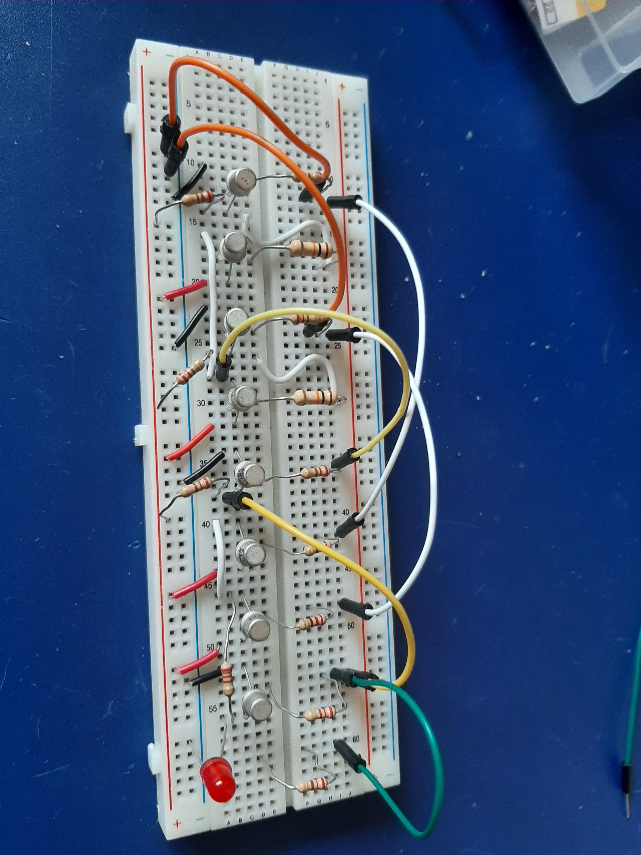
images/Transistor_10.jpg
