jufo-ufo/Breadboard-Computer/images/WP1_09_.jpg

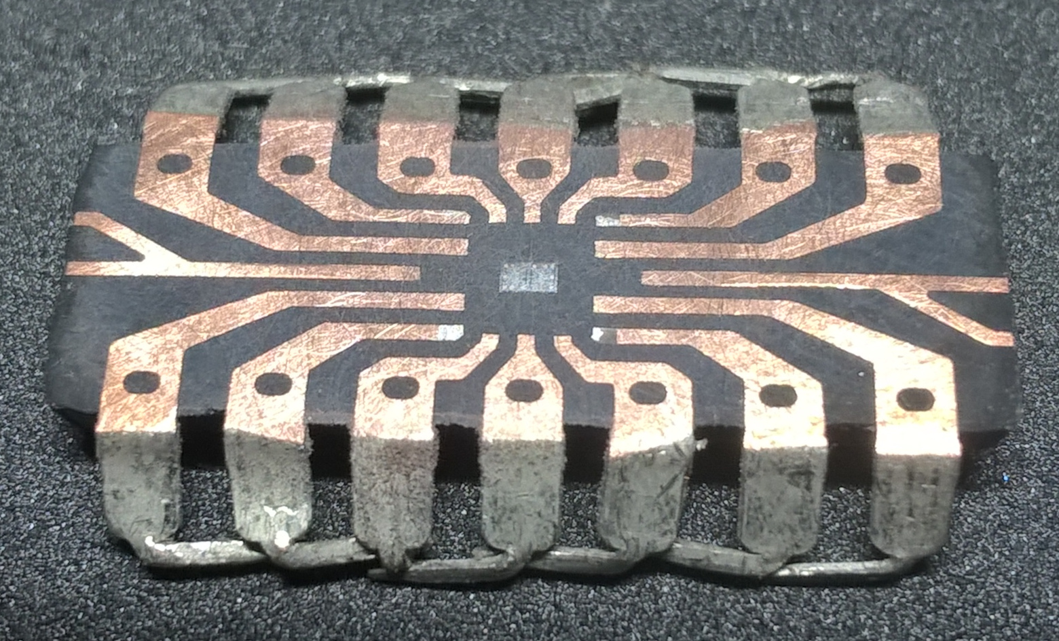
images/WP1_09_.jpg
