jufo-ufo/Breadboard-Computer/images/WP_20210917_16_56_15_.jpg

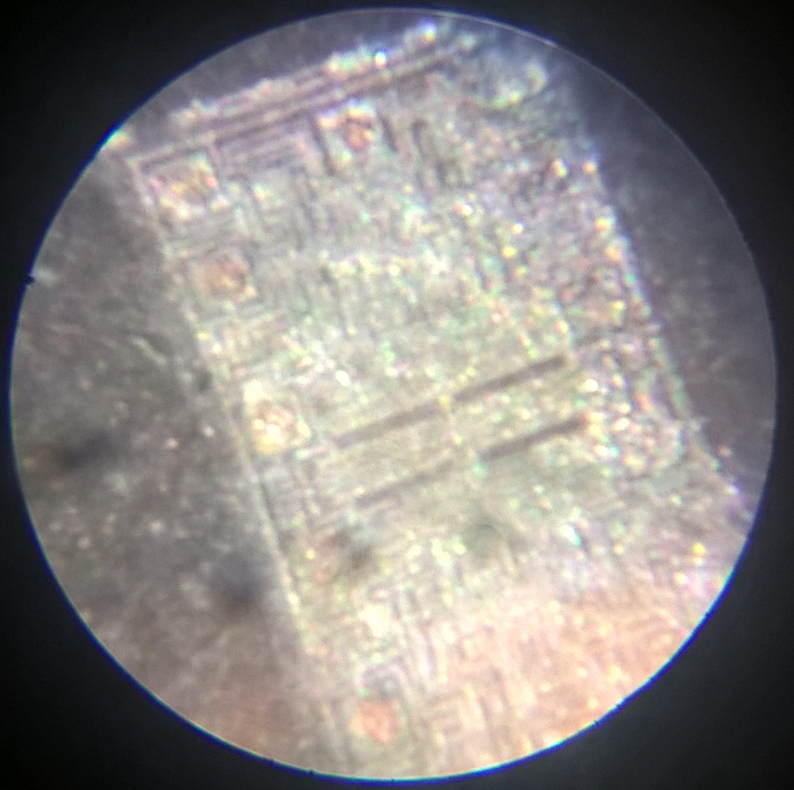
images/WP_20210917_16_56_15_.jpg
