jufo-ufo/Breadboard-Computer/paper/Presentation1/2022-01-30-144704.jpg

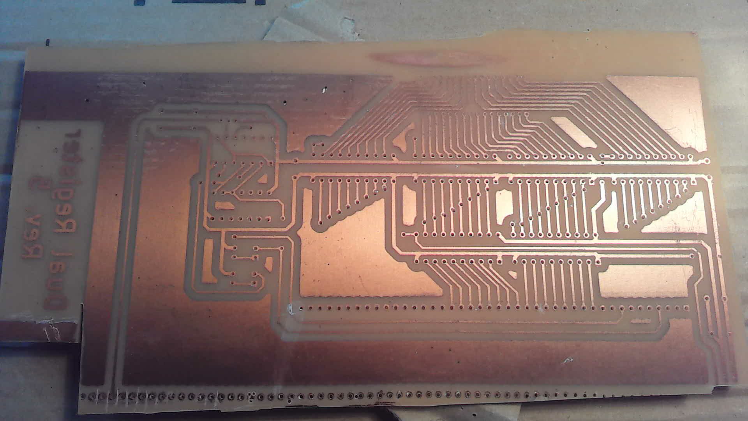
paper/Presentation1/2022-01-30-144704.jpg
