jufo-ufo/Breadboard-Computer/paper/Presentation1/2022-02-08-165100.jpg

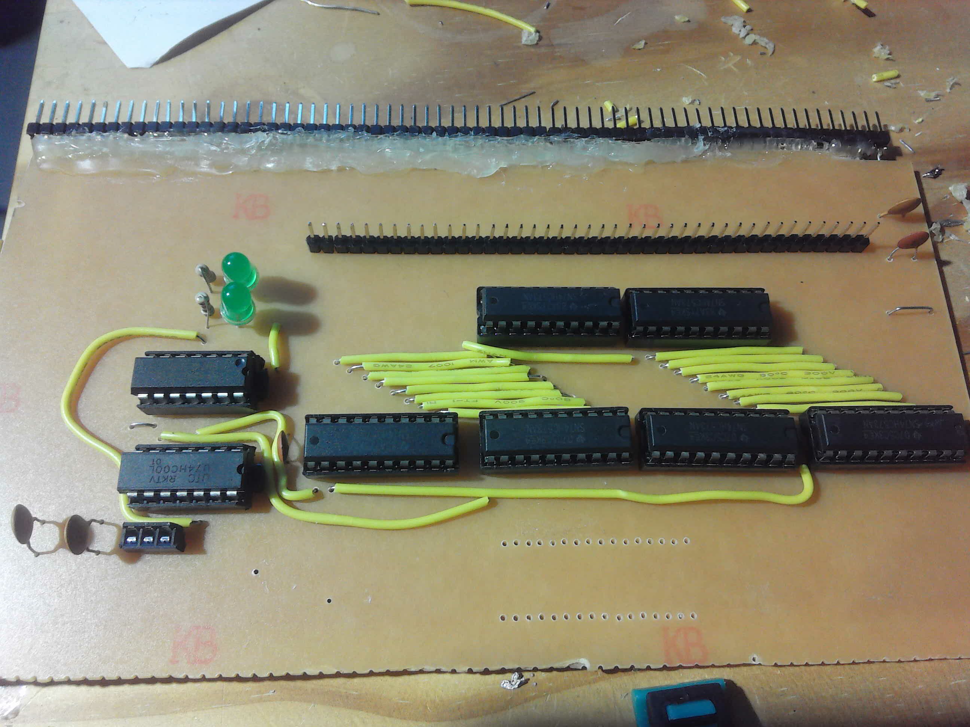
paper/Presentation1/2022-02-08-165100.jpg
