jufo-ufo/Breadboard-Computer/paper/Presentation1/2022-02-08-165116.jpg

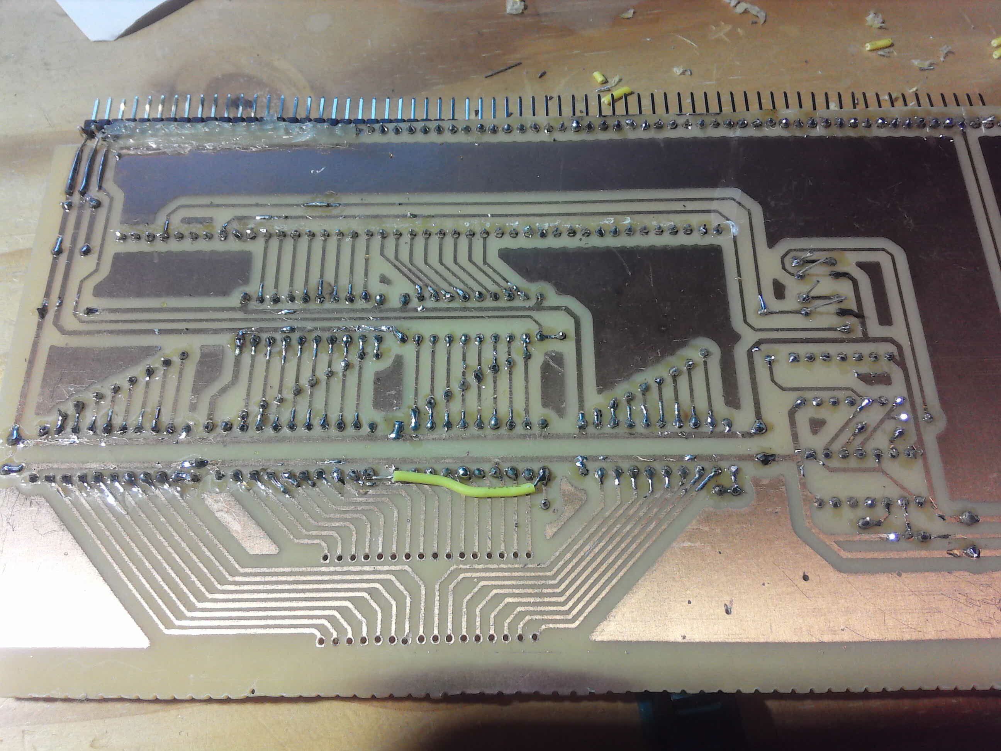
paper/Presentation1/2022-02-08-165116.jpg
