jufo-ufo/Breadboard-Computer/paper/Presentation1/20220114_142515.jpg

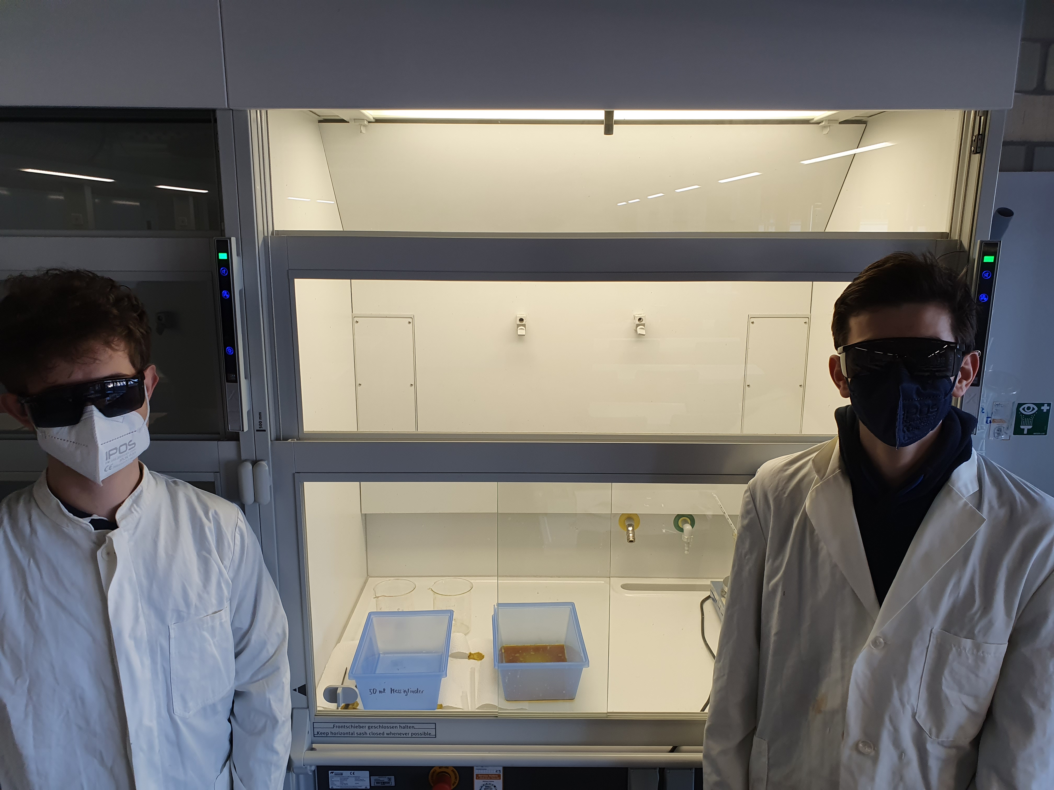
paper/Presentation1/20220114_142515.jpg
