jufo-ufo/Breadboard-Computer/paper/Presentation1/20220129_140335.jpg

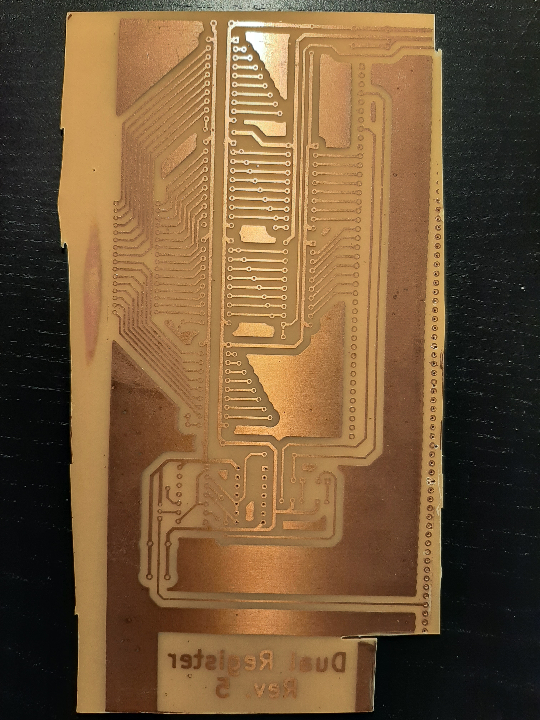
paper/Presentation1/20220129_140335.jpg
