jufo-ufo/Breadboard-Computer/paper/Presentation1/bg_pcb.jpg

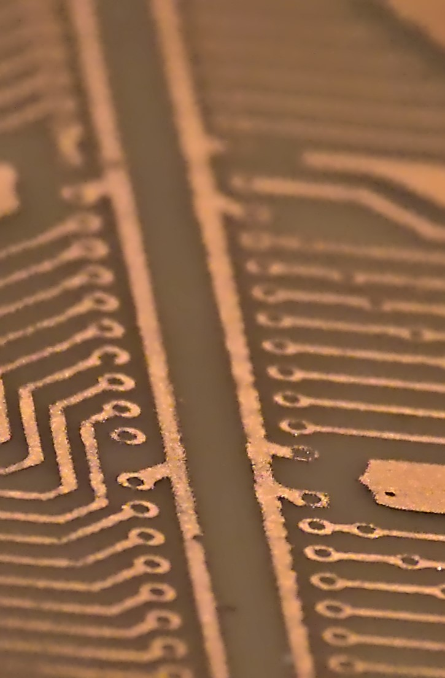
paper/Presentation1/bg_pcb.jpg
