jufo-ufo/Breadboard-Computer/paper/Presentation1/DSC_1062.jpg

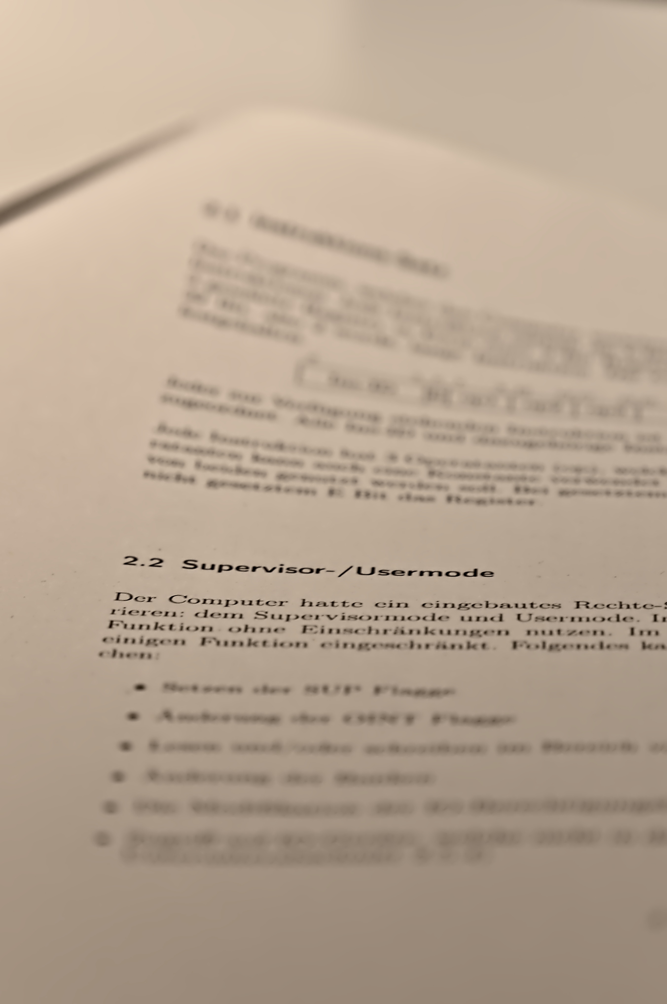
paper/Presentation1/DSC_1062.jpg
