jufo-ufo/Breadboard-Computer/paper/Presentation1/DSC_1062asb.jpg

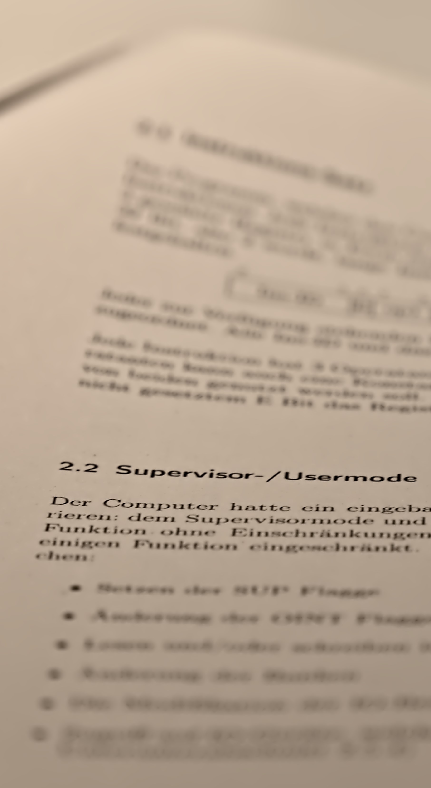
paper/Presentation1/DSC_1062asb.jpg
