jufo-ufo/Breadboard-Computer/paper/Presentation1/Emulator Code.PNG

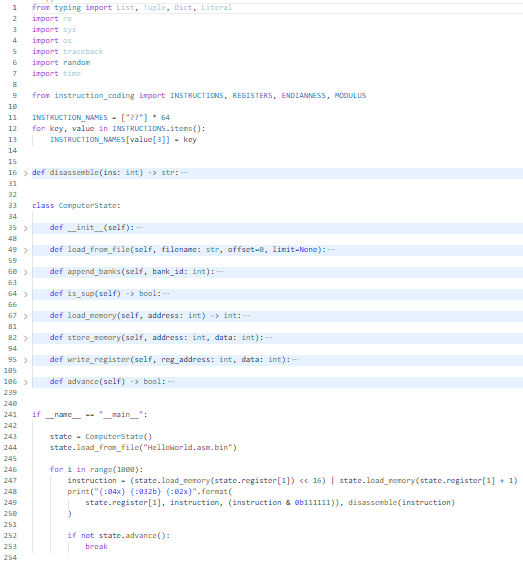
paper/Presentation1/Emulator Code.PNG
