jufo-ufo/Breadboard-Computer/paper/Presentation1/kicad1.png

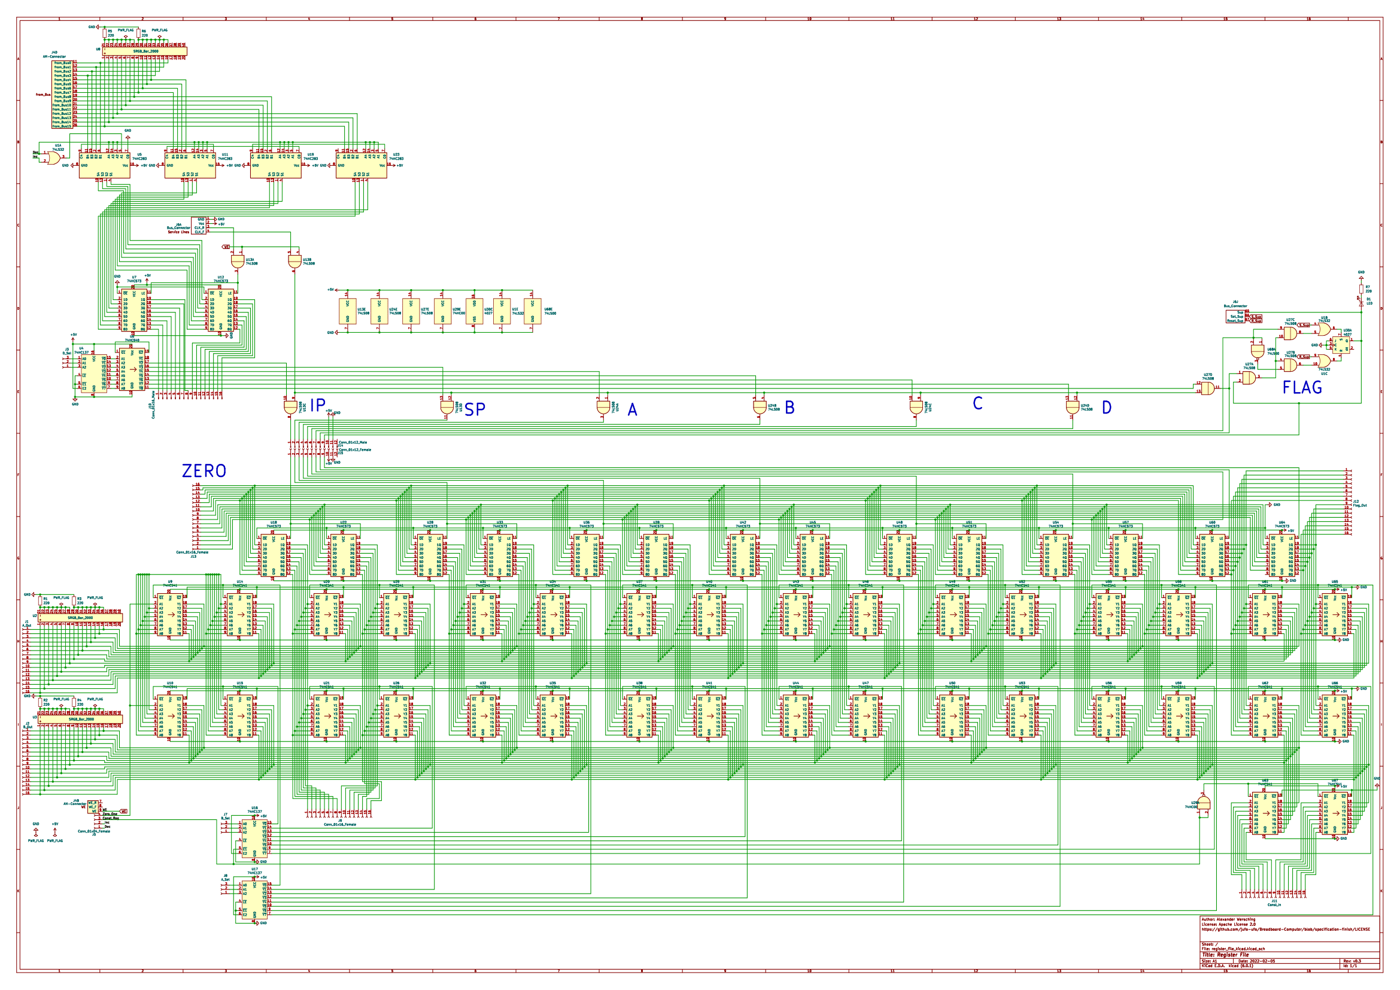
paper/Presentation1/kicad1.png
