jufo-ufo/Breadboard-Computer/paper/Presentation1/kicad2.png

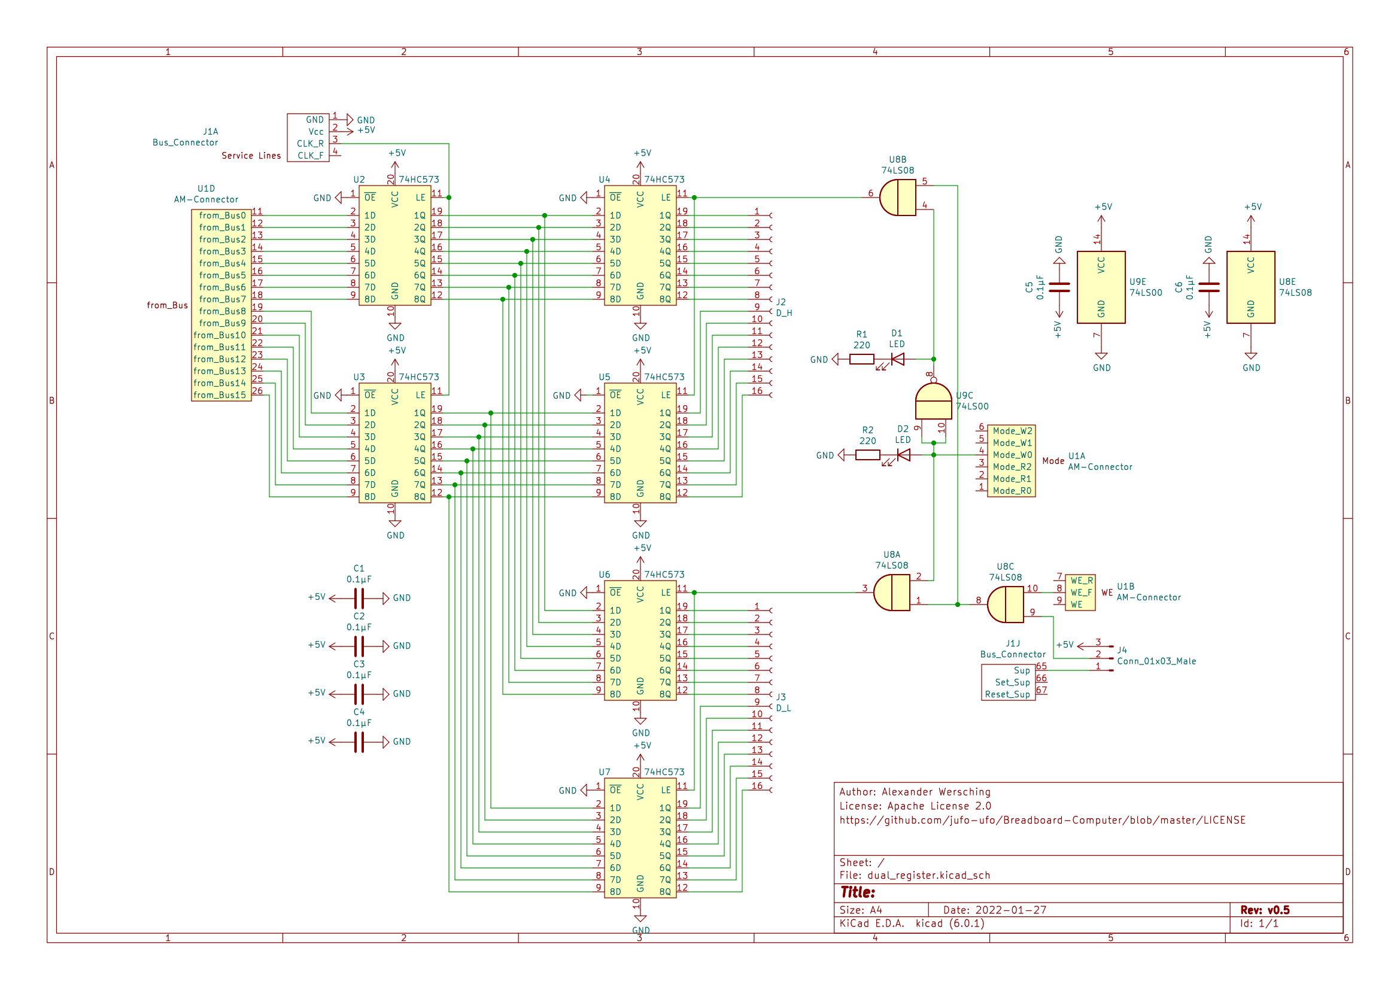
paper/Presentation1/kicad2.png
