jufo-ufo/Breadboard-Computer/paper/Presentation1/logisim1.png

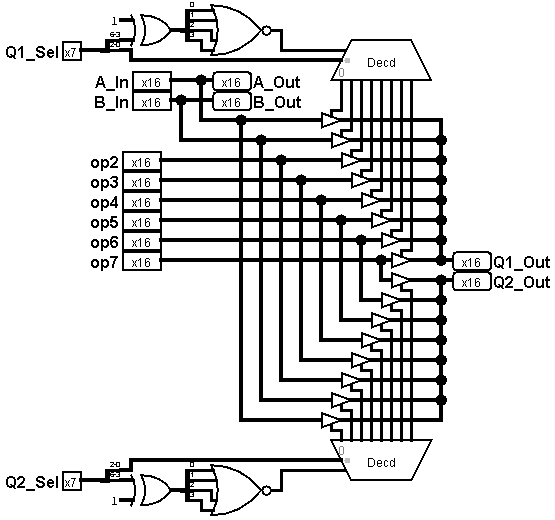
paper/Presentation1/logisim1.png
