jufo-ufo/Breadboard-Computer/paper/Presentation1/logisim2.png

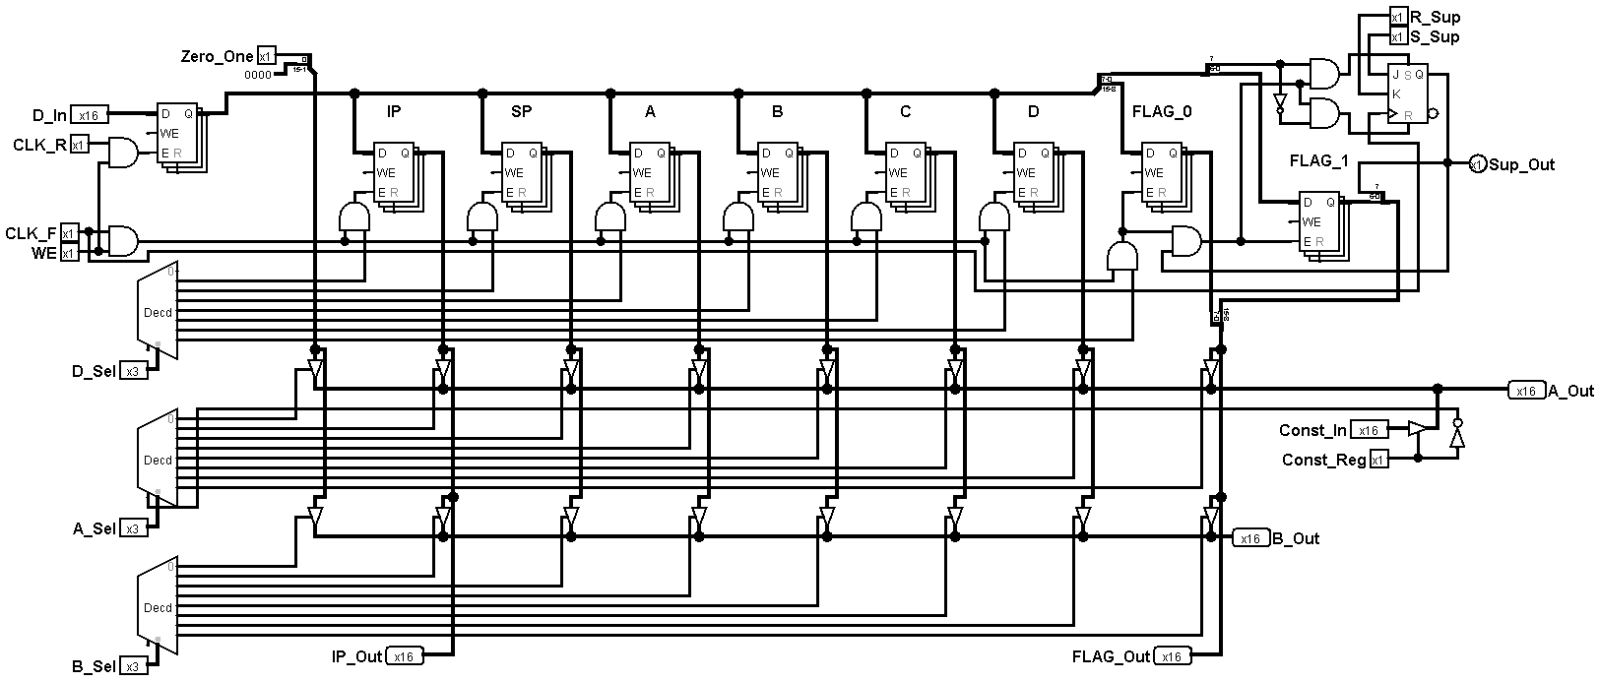
paper/Presentation1/logisim2.png
