jufo-ufo/Breadboard-Computer/paper/Presentation1/Logisim3.png

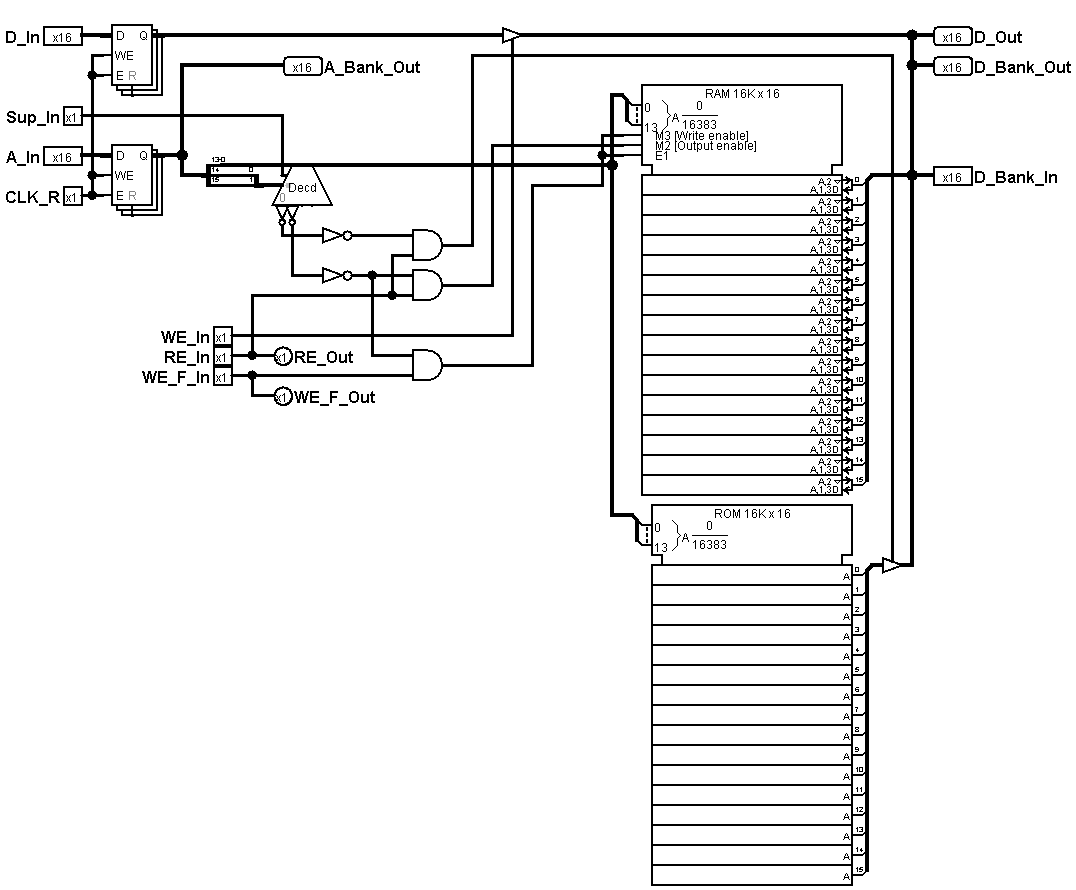
paper/Presentation1/Logisim3.png
