jufo-ufo/Breadboard-Computer/paper/Presentation1/Logisim4.png

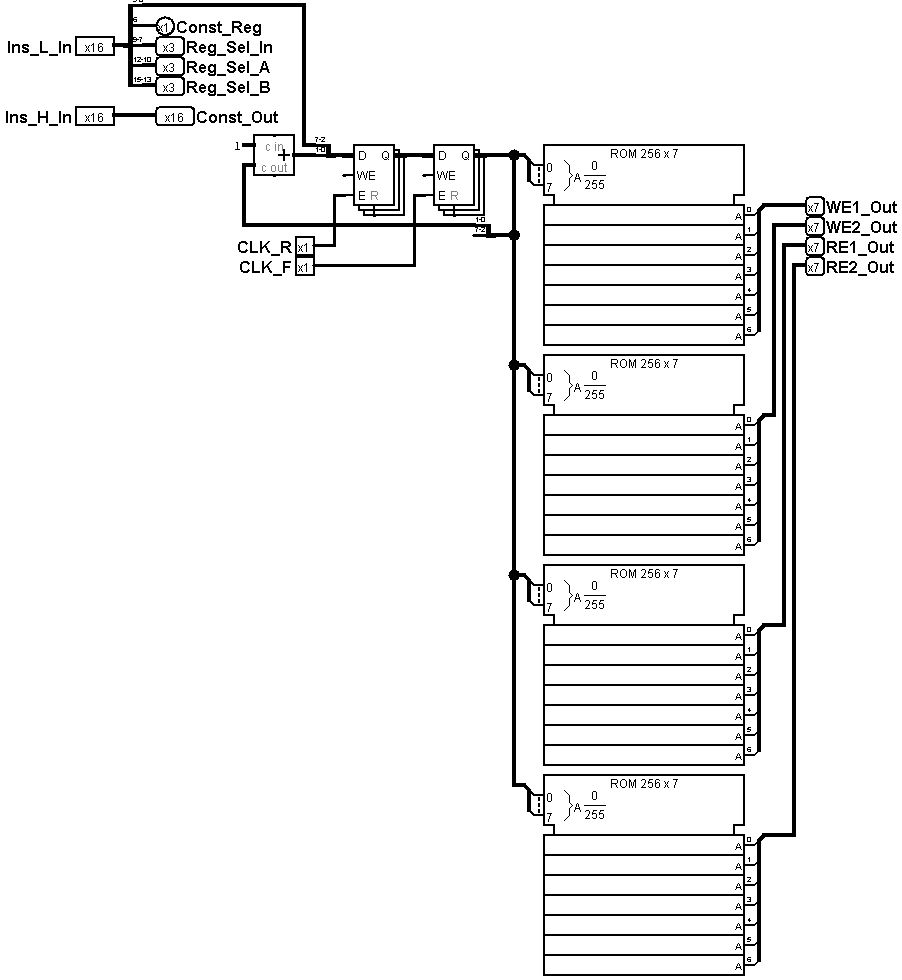
paper/Presentation1/Logisim4.png
