jufo-ufo/Breadboard-Computer/paper/Presentation1/Logisim5.png

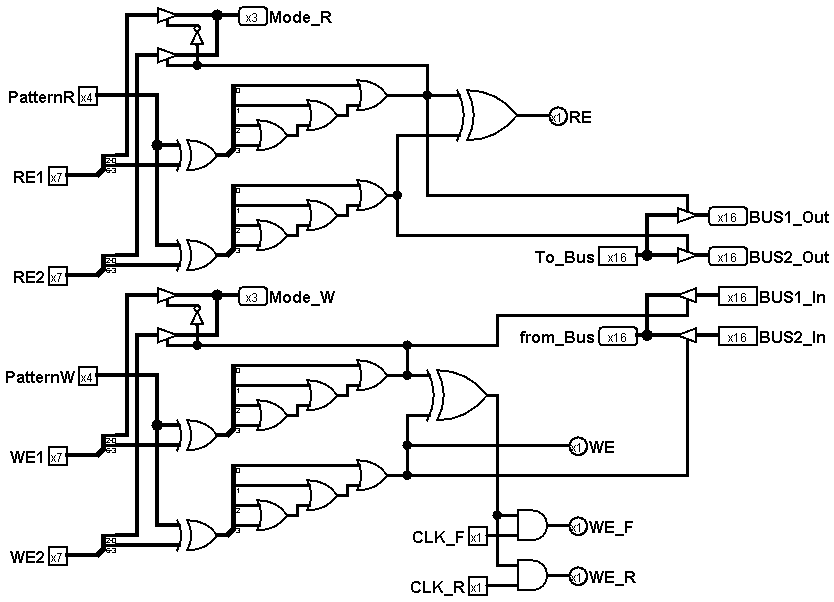
paper/Presentation1/Logisim5.png
