jufo-ufo/Breadboard-Computer/paper/Presentation1/Logisim6.PNG

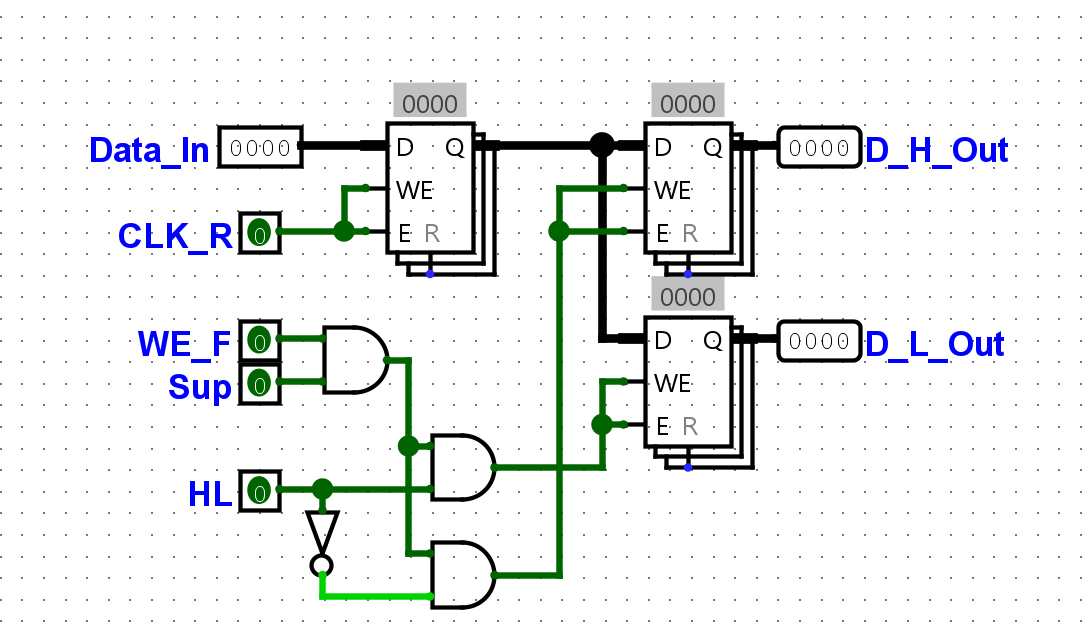
paper/Presentation1/Logisim6.PNG
