jufo-ufo/Breadboard-Computer/paper/Presentation1/pcb1.PNG

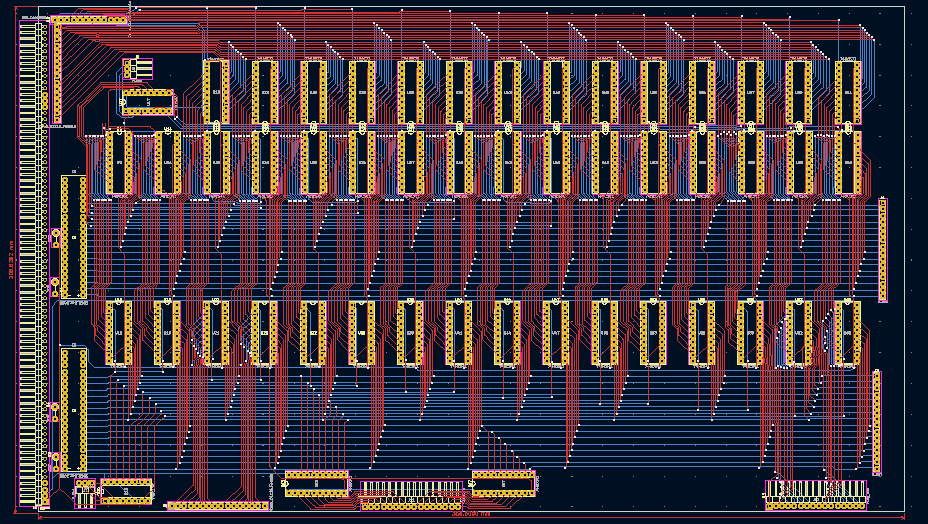
paper/Presentation1/pcb1.PNG
