jufo-ufo/Breadboard-Computer/paper/Presentation1/pcb2.PNG

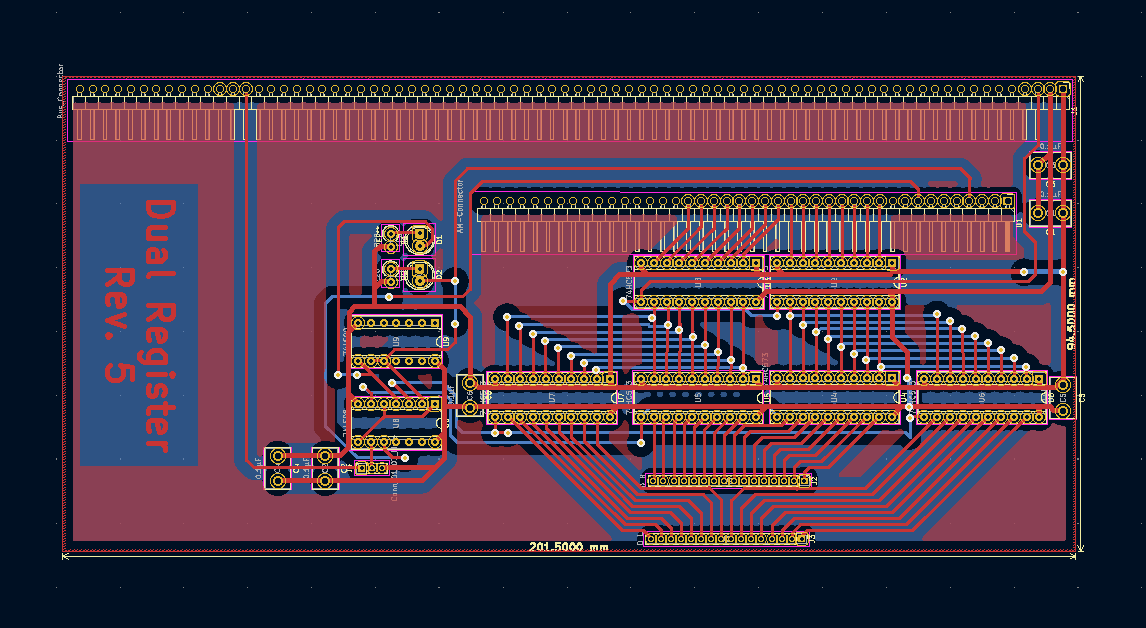
paper/Presentation1/pcb2.PNG
