jufo-ufo/Breadboard-Computer/paper/Presentation1/pcb3.png

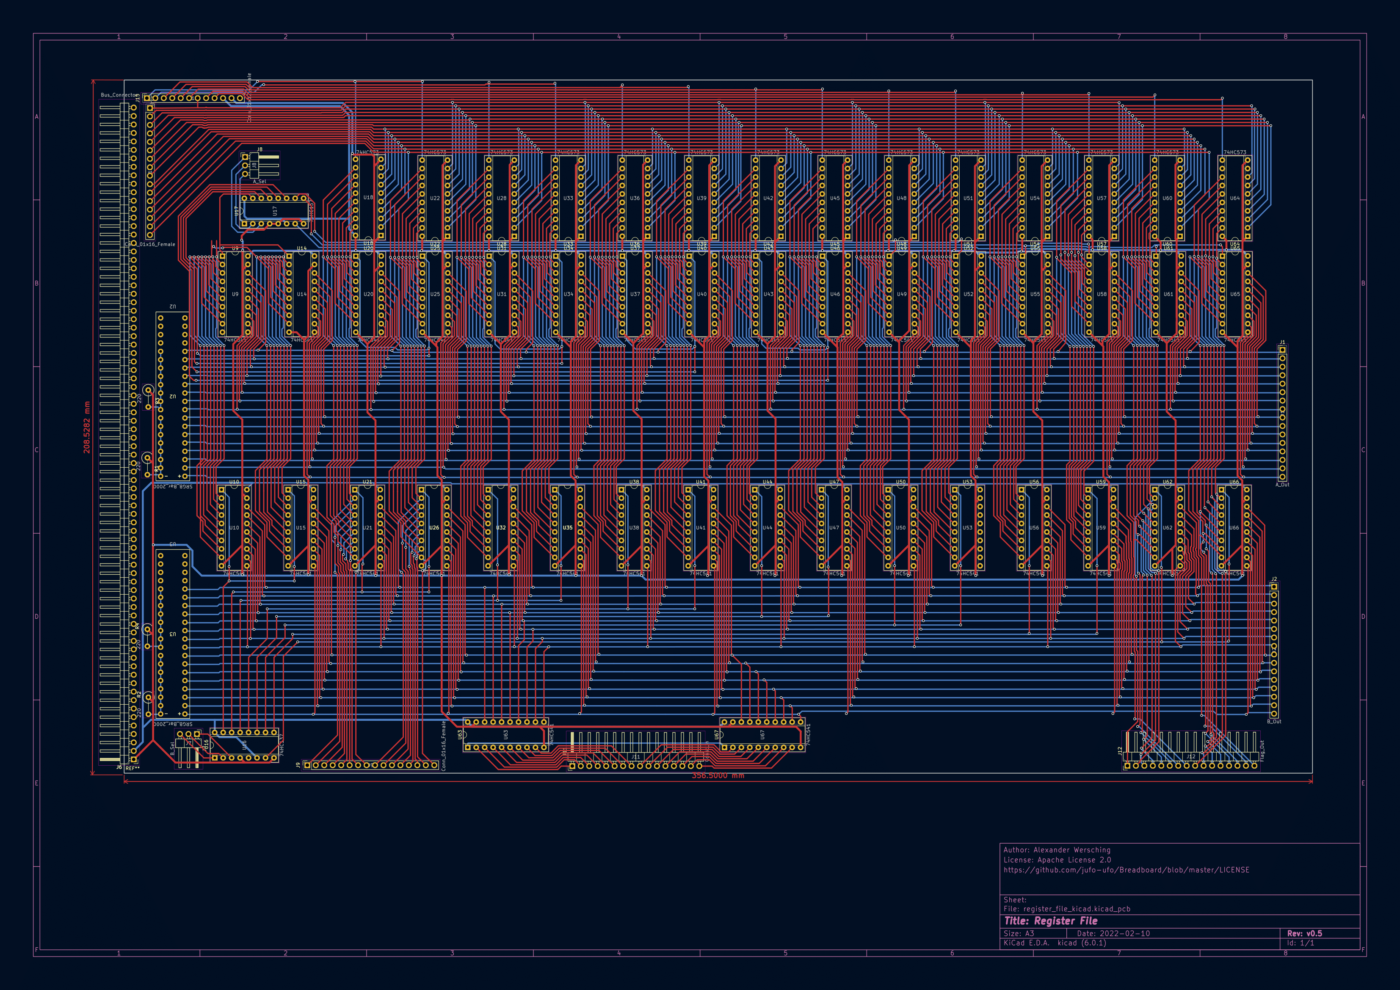
paper/Presentation1/pcb3.png
