jufo-ufo/Breadboard-Computer/paper/Presentation1/WP_20211112_14_25_19_Pro.jpg

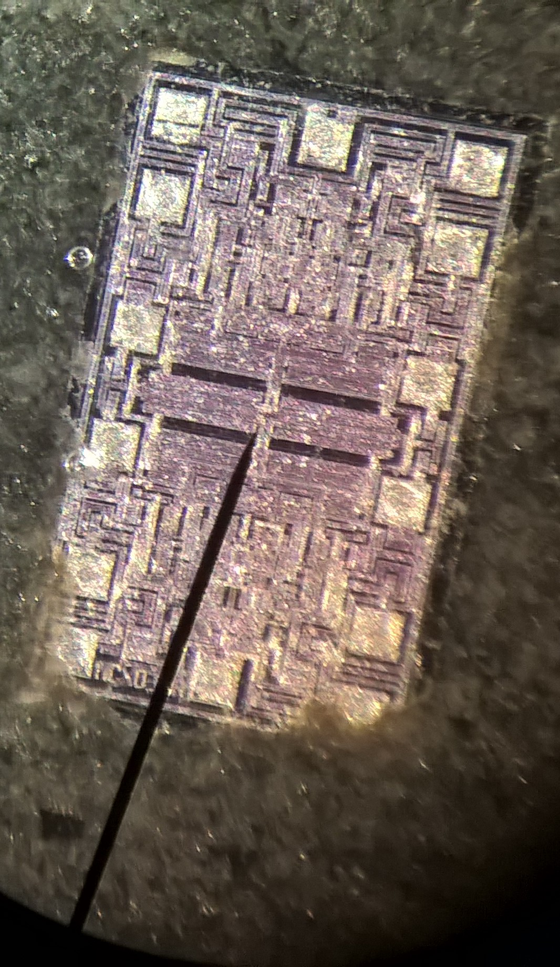
paper/Presentation1/WP_20211112_14_25_19_Pro.jpg
