jufo-ufo/Breadboard-Computer/paper/Presentation1/WP_20211217_13_47_51_Pro.jpg

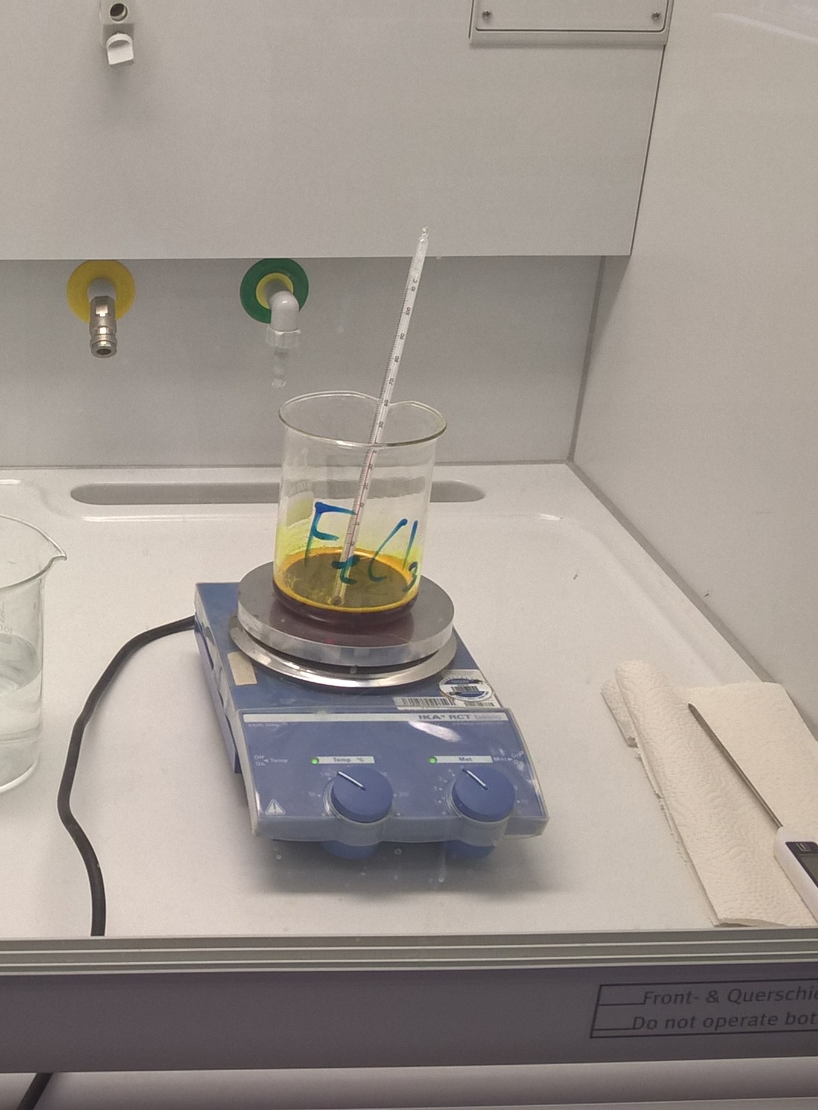
paper/Presentation1/WP_20211217_13_47_51_Pro.jpg
