jufo-ufo/Breadboard-Computer/images/PropDelay_Setup_02.jpg

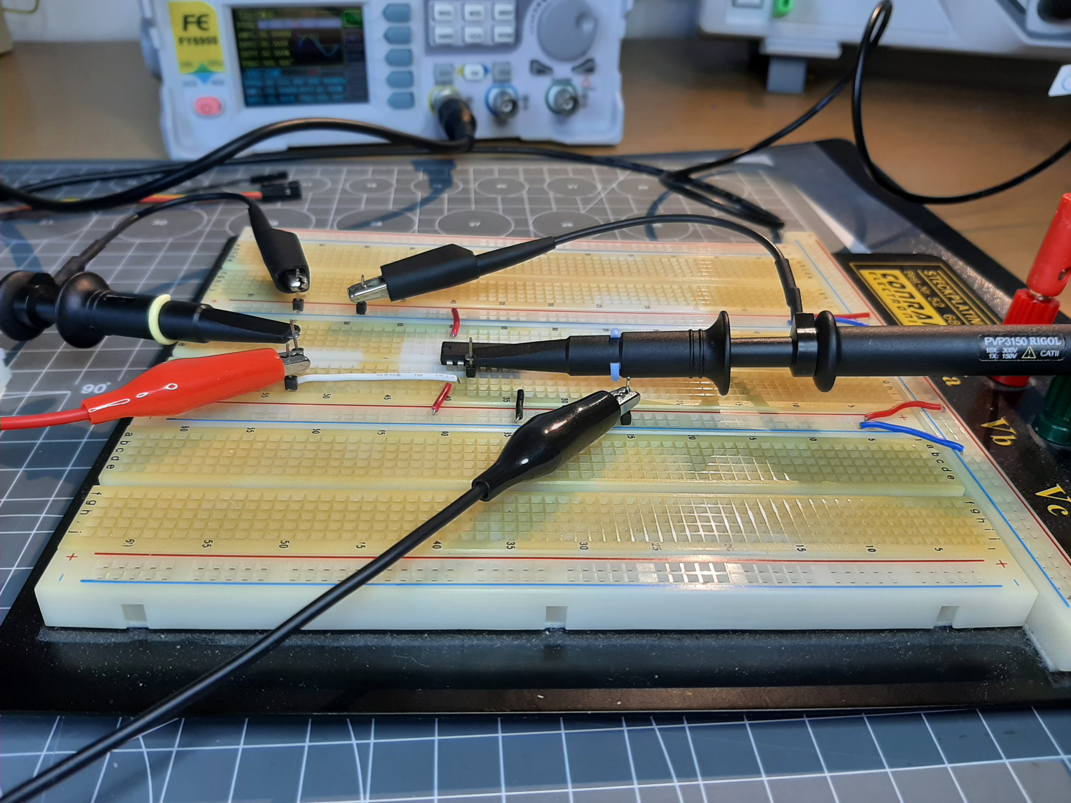
images/PropDelay_Setup_02.jpg
