jufo-ufo/Breadboard-Computer/images/PropDelay_Setup_04.jpg

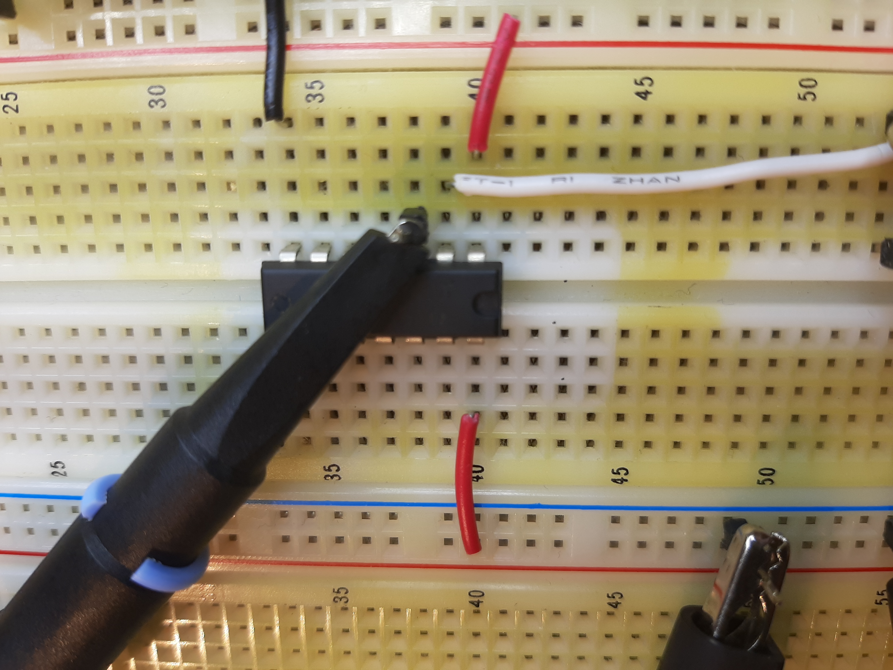
images/PropDelay_Setup_04.jpg
