jufo-ufo/Breadboard-Computer/images/ROM_Programmer_Manual_01_.jpg

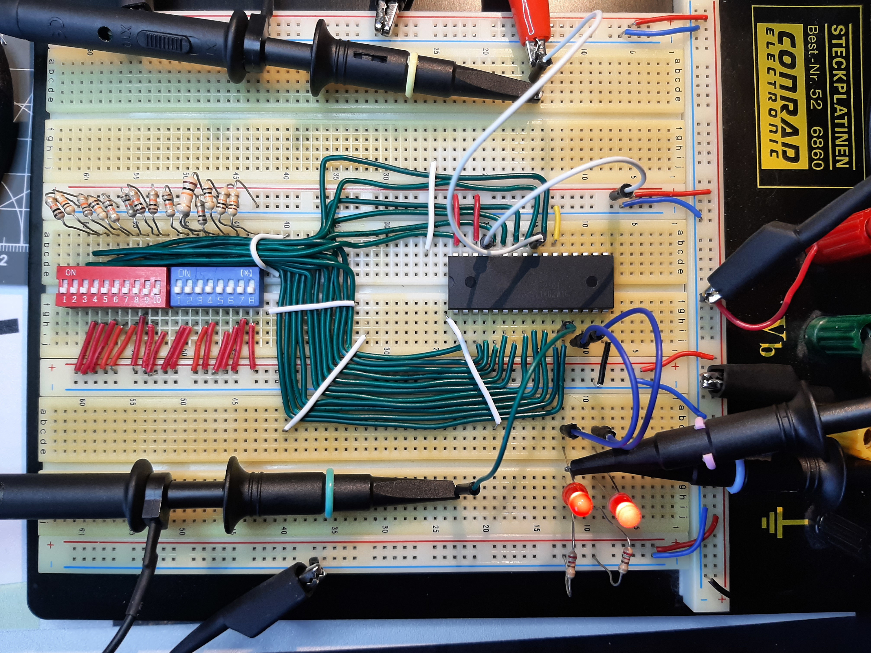
images/ROM_Programmer_Manual_01_.jpg
