jufo-ufo/Breadboard-Computer/images/ROM_Programmer_Manual_02.jpg

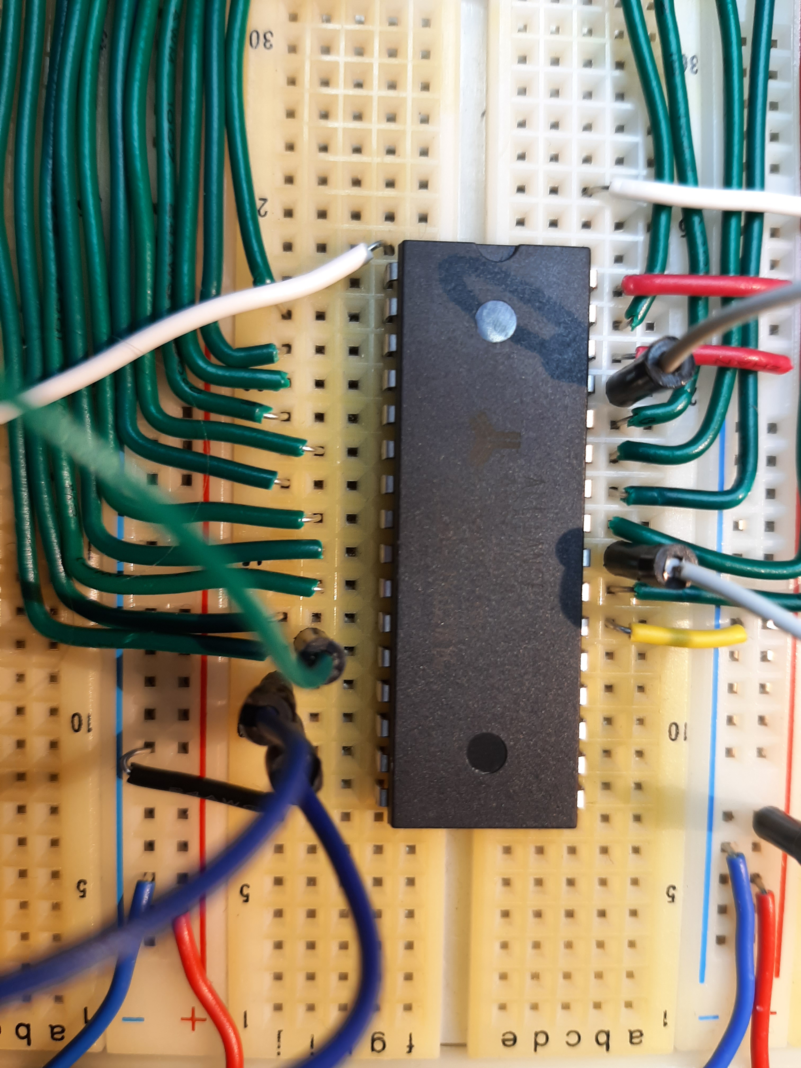
images/ROM_Programmer_Manual_02.jpg
