jufo-ufo/Breadboard-Computer/paper/Presentation1/Assembly.PNG

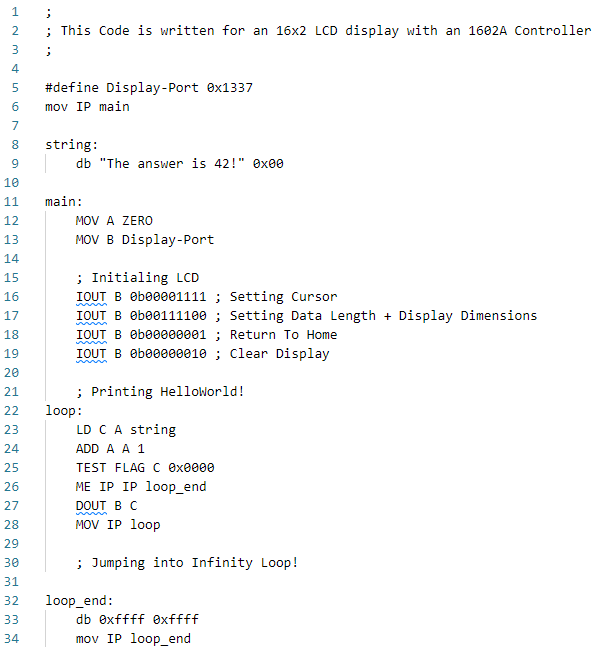
paper/Presentation1/Assembly.PNG
