jufo-ufo/Breadboard-Computer/tools/propagation-delay-tester-new/data/Buffer_Response_Falling/sample_10.csv

time channel1 channel2 channel3
-3.4e-08 4.800000000000001 4.800000000000001 4.800000000000001
-3.39e-08 4.800000000000001 4.800000000000001 4.800000000000001
-3.38e-08 4.6000000000000005 4.800000000000001 5.0
-3.37e-08 4.6000000000000005 4.800000000000001 5.0
-3.36e-08 4.6000000000000005 4.800000000000001 5.0
-3.35e-08 4.6000000000000005 4.800000000000001 5.0
-3.34e-08 4.6000000000000005 4.800000000000001 5.0
-3.33e-08 4.6000000000000005 4.800000000000001 5.0
-3.32e-08 4.6000000000000005 4.6000000000000005 4.800000000000001
-3.31e-08 4.6000000000000005 4.6000000000000005 4.800000000000001
-3.3e-08 4.6000000000000005 4.800000000000001 4.800000000000001
-3.29e-08 4.6000000000000005 4.800000000000001 4.800000000000001
-3.28e-08 4.6000000000000005 4.800000000000001 4.800000000000001
-3.27e-08 4.6000000000000005 4.800000000000001 4.800000000000001
-3.26e-08 4.800000000000001 4.6000000000000005 5.0
-3.25e-08 4.800000000000001 4.6000000000000005 5.0
-3.24e-08 4.6000000000000005 4.800000000000001 4.800000000000001
-3.23e-08 4.6000000000000005 4.800000000000001 4.800000000000001
-3.22e-08 4.6000000000000005 4.800000000000001 5.0
-3.21e-08 4.6000000000000005 4.800000000000001 5.0
-3.2e-08 4.800000000000001 4.800000000000001 4.800000000000001
-3.19e-08 4.800000000000001 4.800000000000001 4.800000000000001
-3.18e-08 4.6000000000000005 4.800000000000001 5.0
-3.17e-08 4.6000000000000005 4.800000000000001 5.0
-3.16e-08 4.6000000000000005 4.800000000000001 5.0
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
8.35e-08 -0.4 -0.6000000000000001 -0.4
8.360000000000001e-08 -0.4 -0.6000000000000001 -0.4
8.37e-08 -0.4 -0.6000000000000001 -0.4
8.380000000000001e-08 -0.4 -0.8 -0.4
8.39e-08 -0.4 -0.8 -0.4
8.4e-08 -0.4 -0.6000000000000001 -0.4
8.41e-08 -0.4 -0.6000000000000001 -0.4
8.42e-08 -0.4 -0.6000000000000001 -0.4
8.430000000000001e-08 -0.4 -0.6000000000000001 -0.4
8.44e-08 -0.4 -0.8 -0.4
8.450000000000001e-08 -0.4 -0.8 -0.4
8.46e-08 -0.4 -0.8 -0.4
8.470000000000001e-08 -0.4 -0.8 -0.4
8.48e-08 -0.4 -0.6000000000000001 -0.4
8.49e-08 -0.4 -0.6000000000000001 -0.4
8.500000000000001e-08 -0.4 -0.6000000000000001 -0.4
8.51e-08 -0.4 -0.6000000000000001 -0.4
8.520000000000001e-08 -0.4 -0.6000000000000001 -0.4
8.530000000000002e-08 -0.4 -0.6000000000000001 -0.4
8.54e-08 -0.4 -0.6000000000000001 -0.4
8.55e-08 -0.4 -0.6000000000000001 -0.4
8.560000000000001e-08 -0.4 -0.6000000000000001 -0.6000000000000001
8.569999999999999e-08 -0.4 -0.6000000000000001 -0.6000000000000001
8.58e-08 -0.4 -0.6000000000000001 -0.6000000000000001
8.590000000000001e-08 -0.4 -0.6000000000000001 -0.6000000000000001
