jufo-ufo/Breadboard-Computer/tools/propagation-delay-tester-new/data/Buffer_Response_Falling/sample_102.csv

time channel1 channel2 channel3
-3.4e-08 4.800000000000001 4.800000000000001 5.0
-3.39e-08 4.800000000000001 4.800000000000001 5.0
-3.38e-08 4.6000000000000005 4.800000000000001 5.0
-3.37e-08 4.6000000000000005 4.800000000000001 5.0
-3.36e-08 4.6000000000000005 4.6000000000000005 5.0
-3.35e-08 4.6000000000000005 4.6000000000000005 5.0
-3.34e-08 4.6000000000000005 4.800000000000001 5.0
-3.33e-08 4.6000000000000005 4.800000000000001 5.0
-3.32e-08 4.6000000000000005 4.800000000000001 5.0
-3.31e-08 4.6000000000000005 4.800000000000001 5.0
-3.3e-08 4.6000000000000005 4.800000000000001 5.0
-3.29e-08 4.6000000000000005 4.800000000000001 5.0
-3.28e-08 4.6000000000000005 4.800000000000001 4.800000000000001
-3.27e-08 4.6000000000000005 4.800000000000001 4.800000000000001
-3.26e-08 4.800000000000001 4.6000000000000005 5.0
-3.25e-08 4.800000000000001 4.6000000000000005 5.0
-3.24e-08 4.6000000000000005 4.800000000000001 5.0
-3.23e-08 4.6000000000000005 4.800000000000001 5.0
-3.22e-08 4.6000000000000005 4.800000000000001 5.0
-3.21e-08 4.6000000000000005 4.800000000000001 5.0
-3.2e-08 4.800000000000001 4.6000000000000005 4.800000000000001
-3.19e-08 4.800000000000001 4.6000000000000005 4.800000000000001
-3.18e-08 4.6000000000000005 4.800000000000001 4.800000000000001
-3.17e-08 4.6000000000000005 4.800000000000001 4.800000000000001
-3.16e-08 4.6000000000000005 4.800000000000001 4.800000000000001
-3.15e-08 4.6000000000000005 4.800000000000001 4.800000000000001
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
-5.699999999999998e-09 4.2 4.800000000000001 4.800000000000001
-5.6000000000000005e-09 4.4 4.800000000000001 4.800000000000001
-5.5e-09 4.4 4.800000000000001 4.800000000000001
-5.399999999999999e-09 4.2 4.800000000000001 4.800000000000001
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
