jufo-ufo/Breadboard-Computer/circets/test_circet/subtraction.PNG

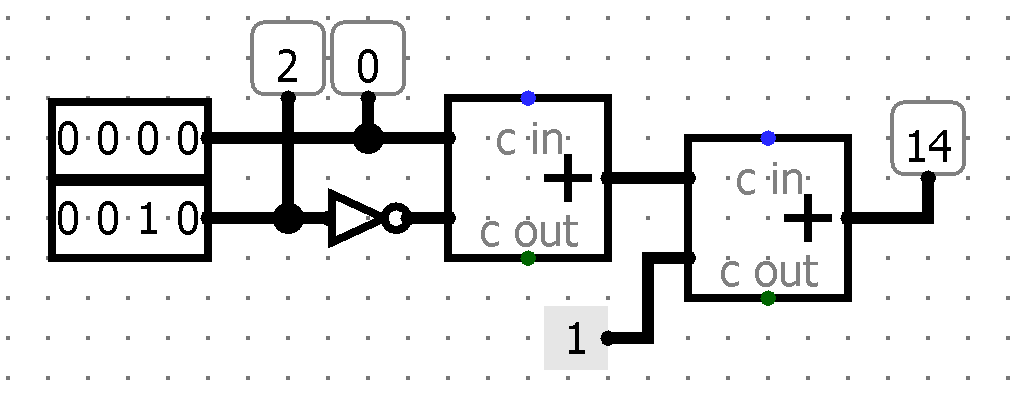
circets/test_circet/subtraction.PNG
