jufo-ufo/Breadboard-Computer/images/NANDs_Result_Falling.png

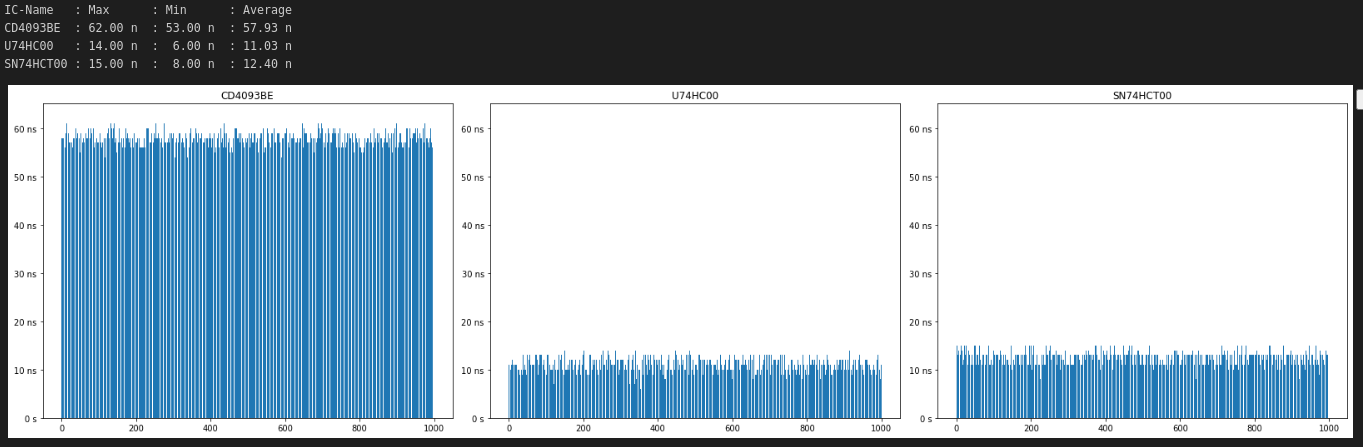
images/NANDs_Result_Falling.png
