jufo-ufo/Breadboard-Computer/images/Oscilation_Tests_Osci_01.jpg

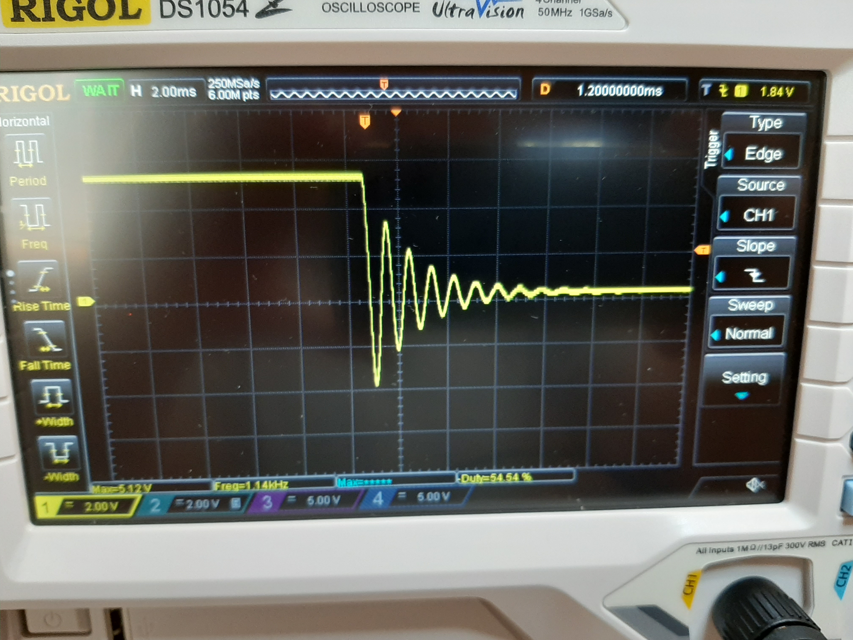
images/Oscilation_Tests_Osci_01.jpg
