jufo-ufo/Breadboard-Computer/images/Oscilation_Tests_Osci_02.jpg

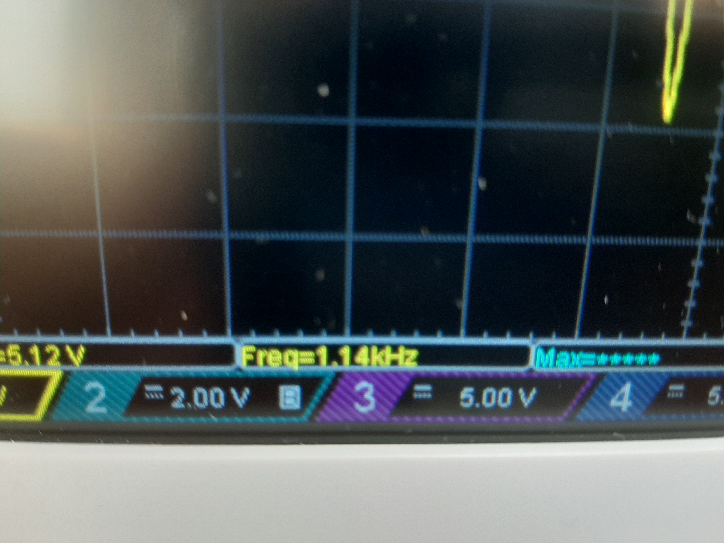
images/Oscilation_Tests_Osci_02.jpg
