jufo-ufo/Breadboard-Computer/images/Oscilation_Tests_Overview_02.jpg

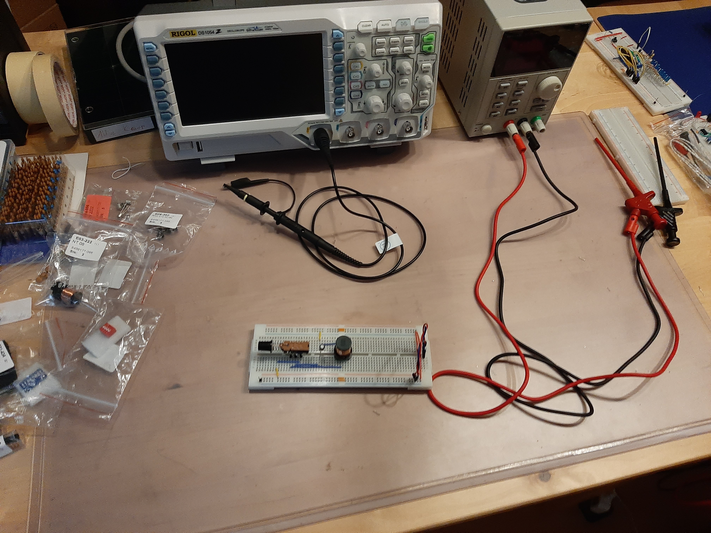
images/Oscilation_Tests_Overview_02.jpg
