jufo-ufo/Breadboard-Computer/circets/Dual_Register/dual_register/pcb_layout_Cu_bottom.pdf

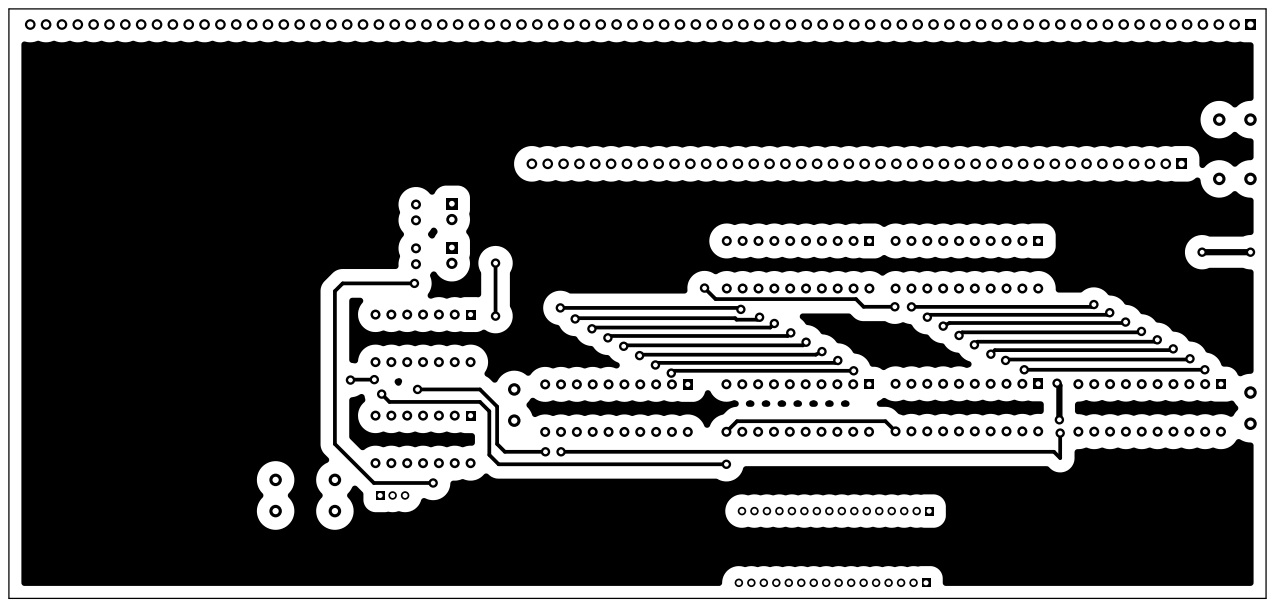
[picture p291: page 1]
