jufo-ufo/Breadboard-Computer/circets/Dual_Register/dual_register/pcb_layout_Cu_top.pdf

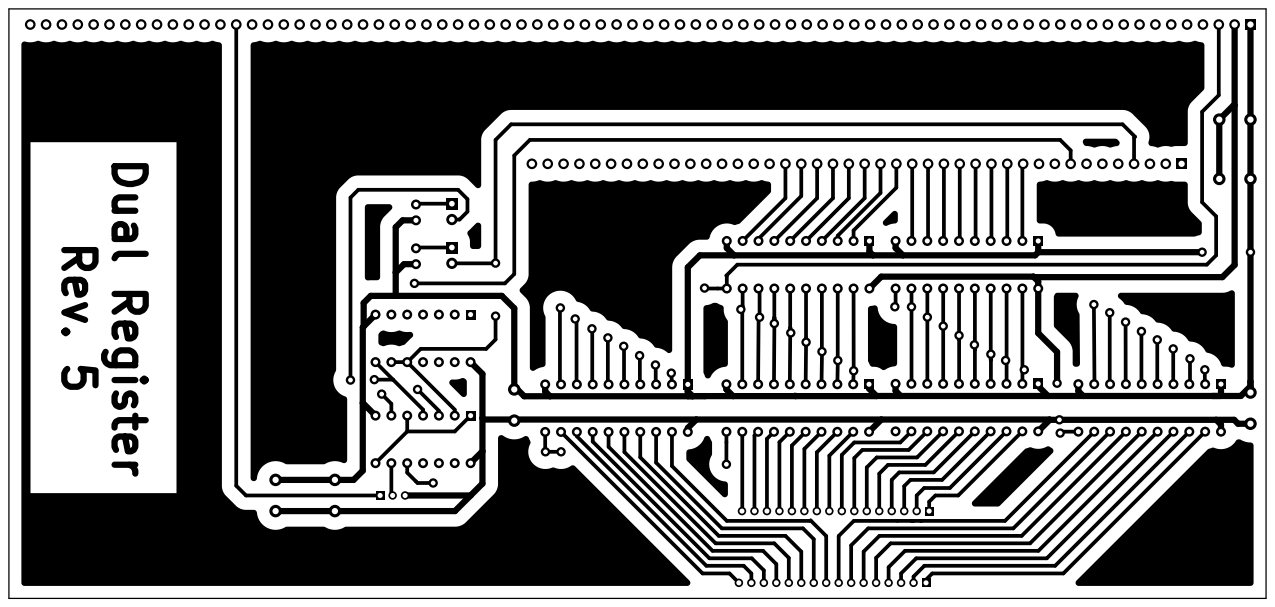
[picture p292: page 1]
