jufo-ufo/Breadboard-Computer/images/20211219_222521.jpg

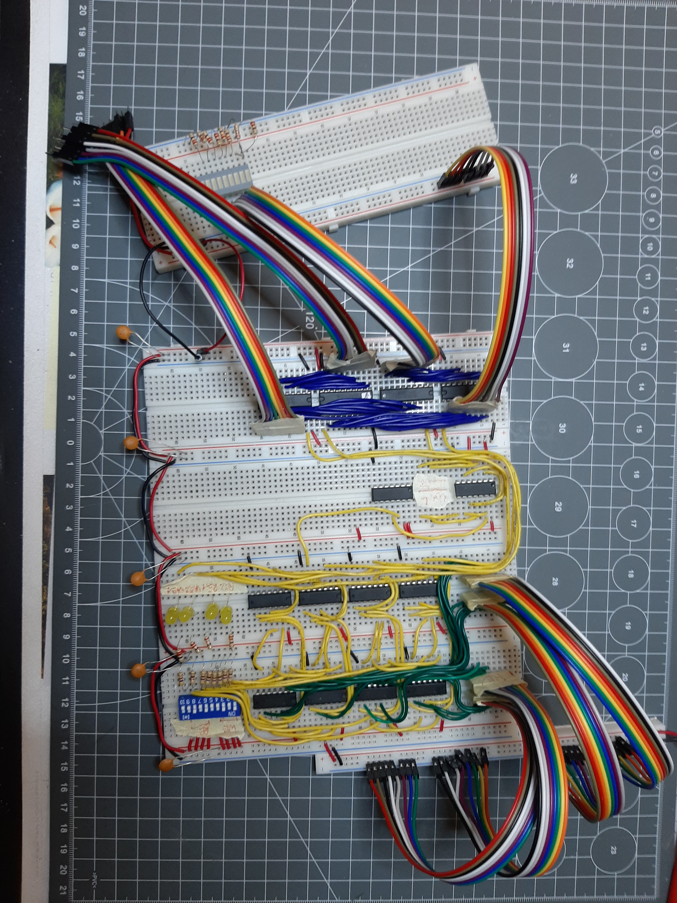
images/20211219_222521.jpg
