jufo-ufo/Breadboard-Computer/images/Activation_Module_V01_BB_04.jpg

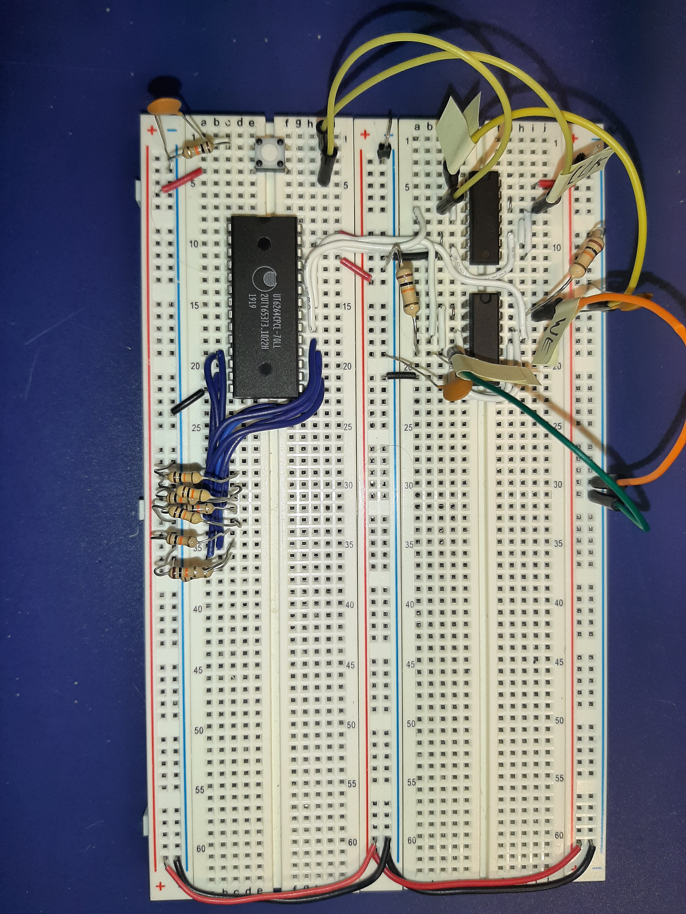
images/Activation_Module_V01_BB_04.jpg
