jufo-ufo/Breadboard-Computer/images/Computer_V01_Chaos_02.jpg

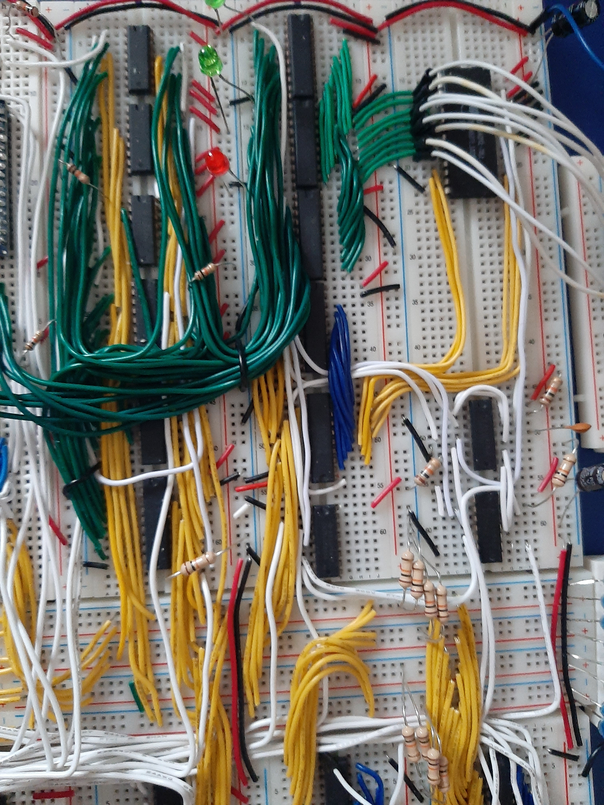
images/Computer_V01_Chaos_02.jpg
