jufo-ufo/Breadboard-Computer/images/Computer_V01_Chaos_04.jpg

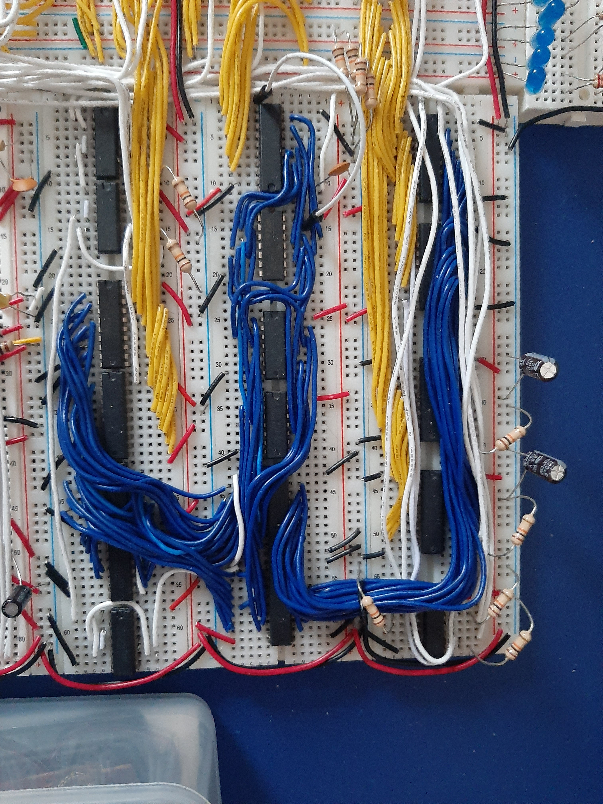
images/Computer_V01_Chaos_04.jpg
