jufo-ufo/Breadboard-Computer/images/Computer_V01_Chaos_08.jpg

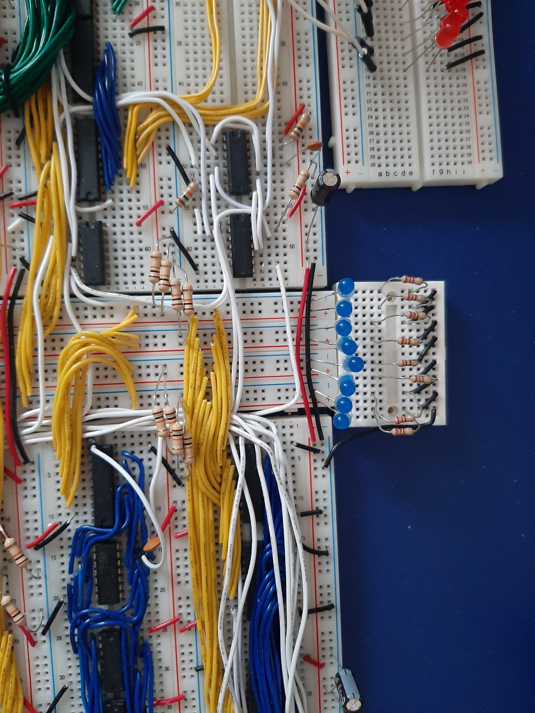
images/Computer_V01_Chaos_08.jpg
