jufo-ufo/Breadboard-Computer/images/Computer_V01_LCD_01.jpg

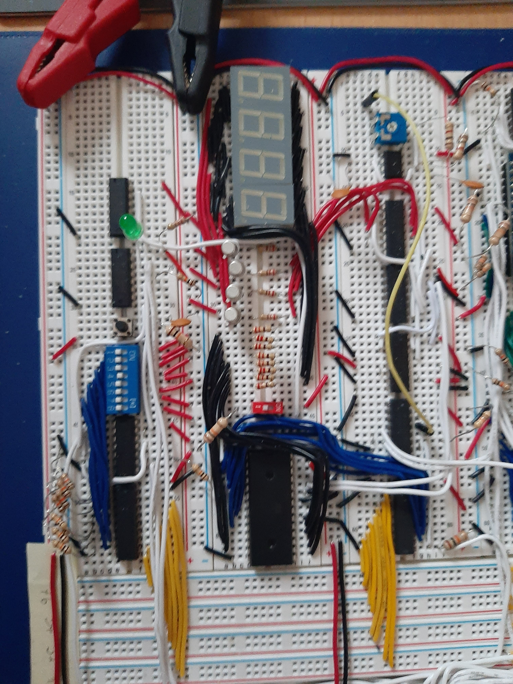
images/Computer_V01_LCD_01.jpg
