jufo-ufo/Breadboard-Computer/images/Computer_V01_Overview_02.jpg

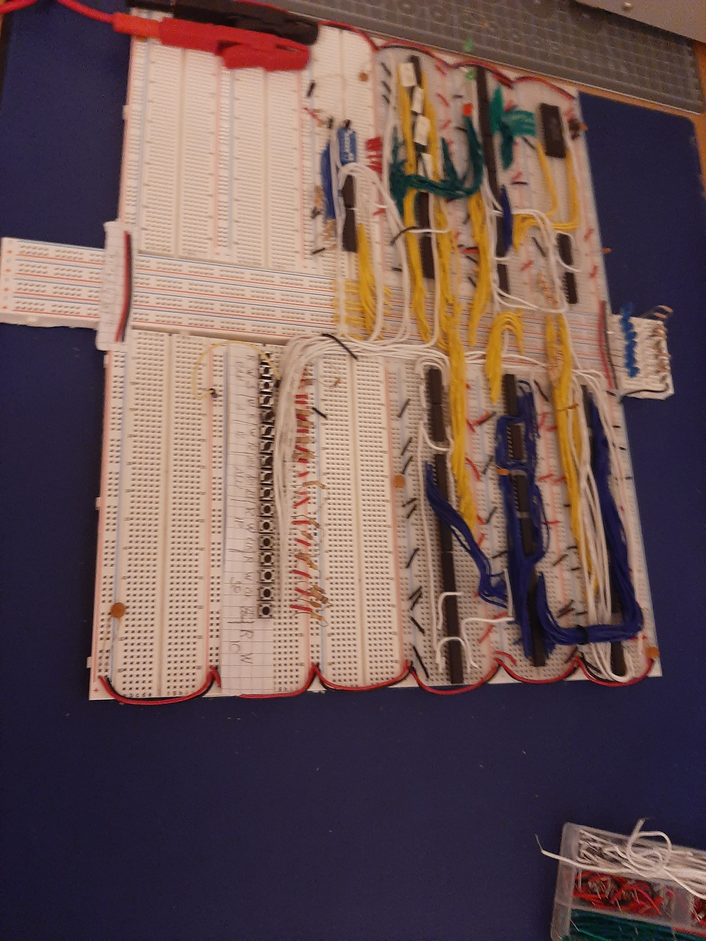
images/Computer_V01_Overview_02.jpg
