jufo-ufo/Breadboard-Computer/images/Computer_V01_Overview_04.jpg

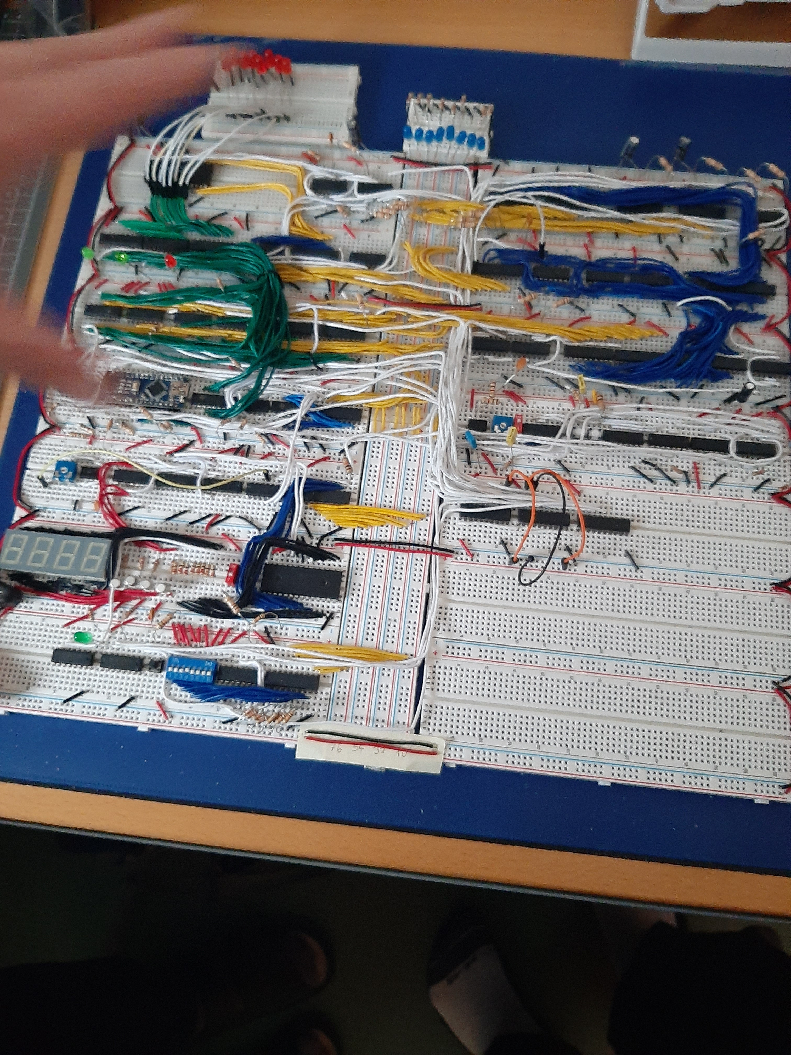
images/Computer_V01_Overview_04.jpg
