jufo-ufo/Breadboard-Computer/images/Computer_V01_PartView_02.jpg

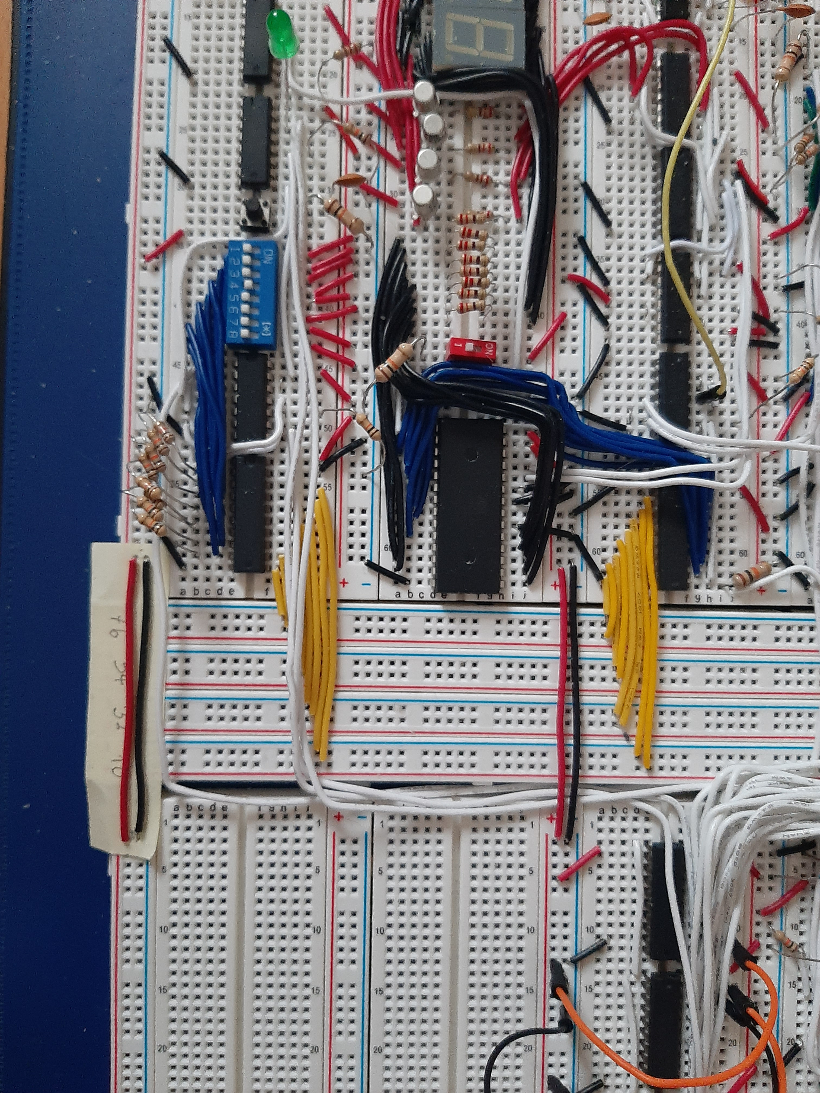
images/Computer_V01_PartView_02.jpg
