jufo-ufo/Breadboard-Computer/images/Computer_V01_PartView_03.jpg

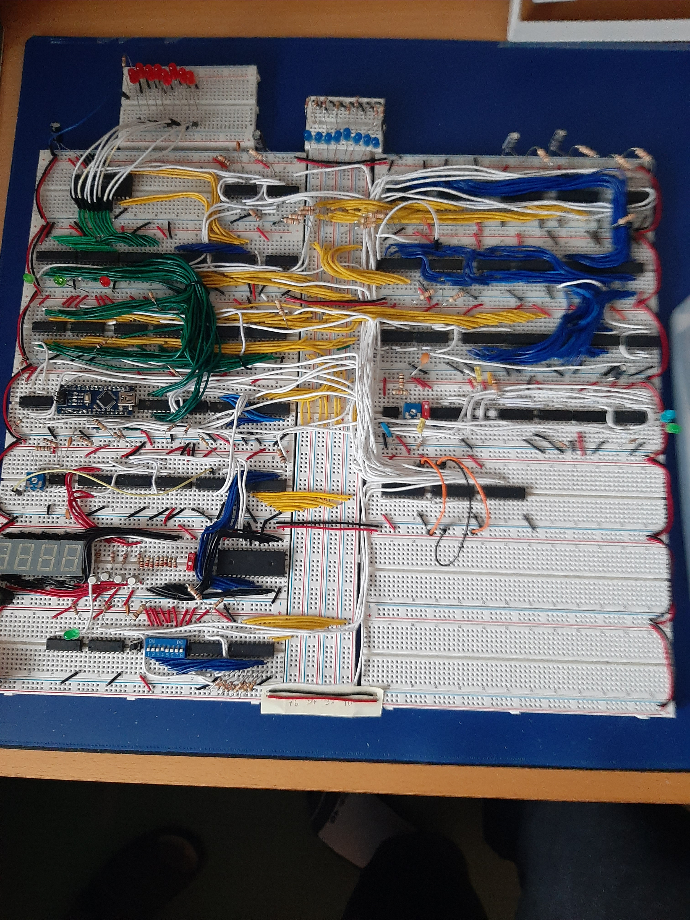
images/Computer_V01_PartView_03.jpg
