jufo-ufo/Breadboard-Computer/images/pcb/20220119_215302.jpg

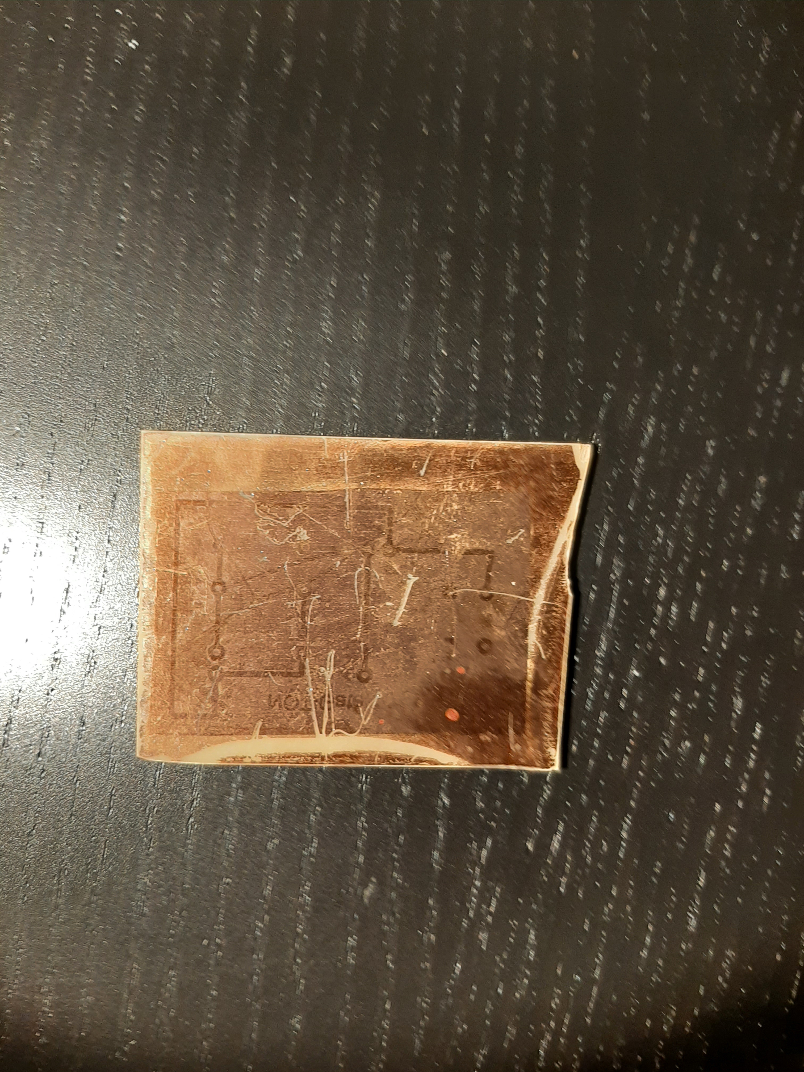
images/pcb/20220119_215302.jpg
