jufo-ufo/Breadboard-Computer/images/WP_20211029_144239.jpg

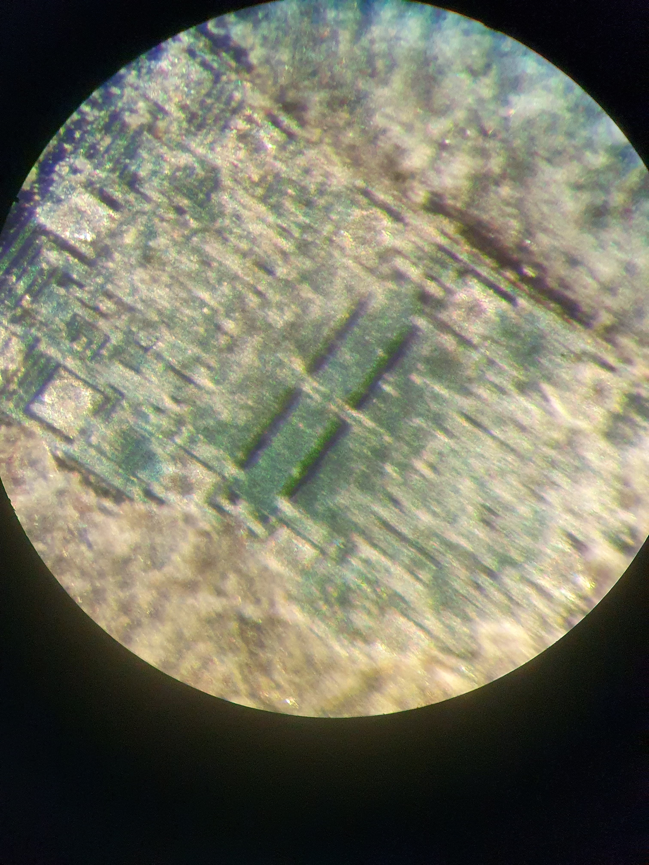
images/WP_20211029_144239.jpg
