jufo-ufo/Breadboard-Computer/images/Oscilation_Tests_Overview_03.jpg

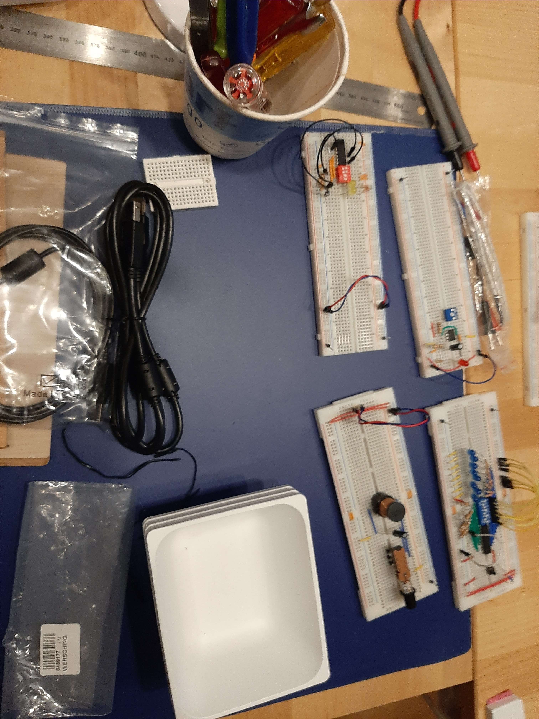
images/Oscilation_Tests_Overview_03.jpg
